gitberthe/BertheVarioTac/CompZoneAerienne/zones_gnuplot/000.png

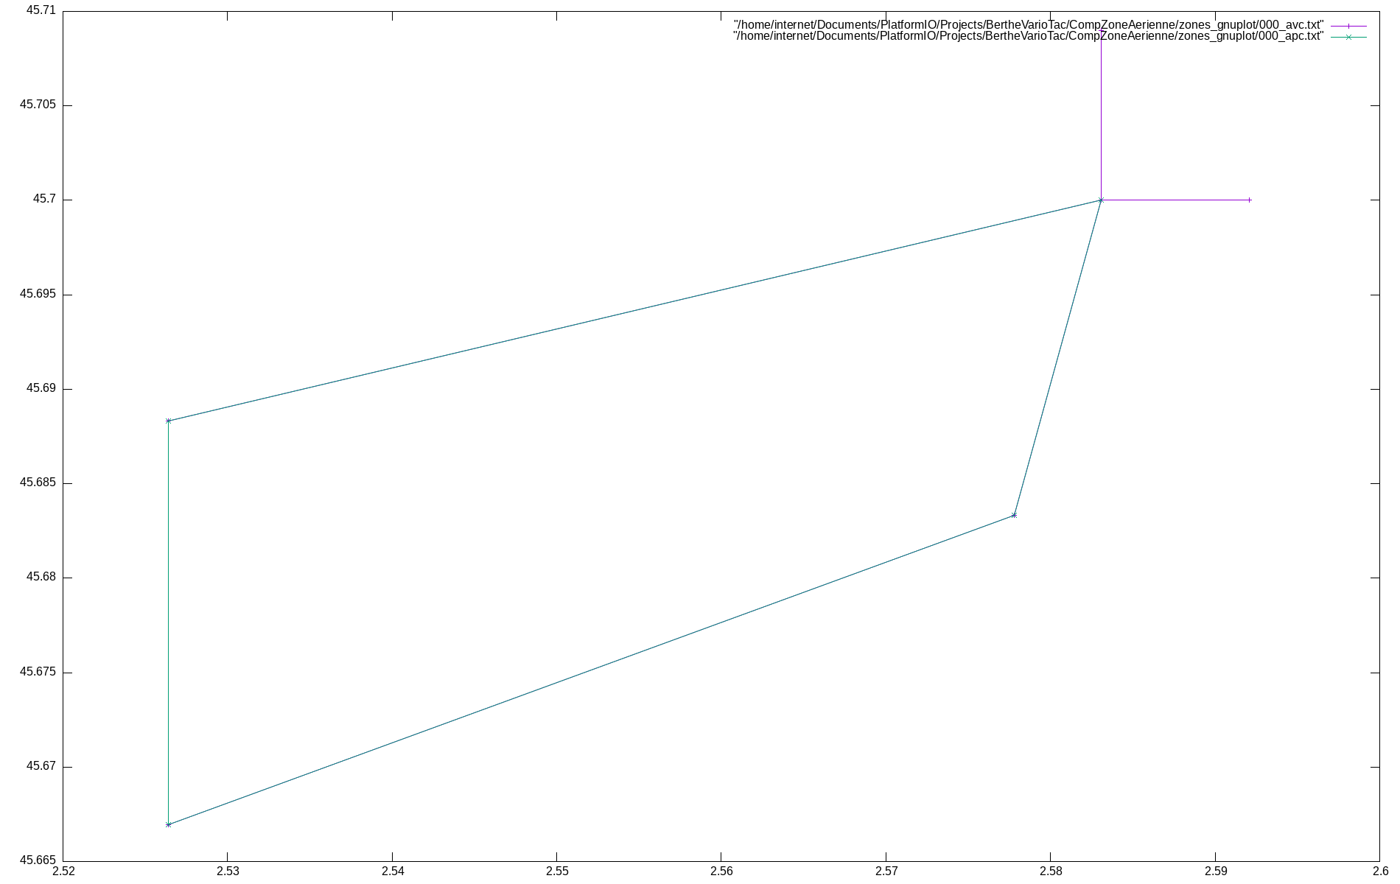
CompZoneAerienne/zones_gnuplot/000.png
