gitberthe/BertheVarioTac/CompZoneAerienne/zones_gnuplot/001.png

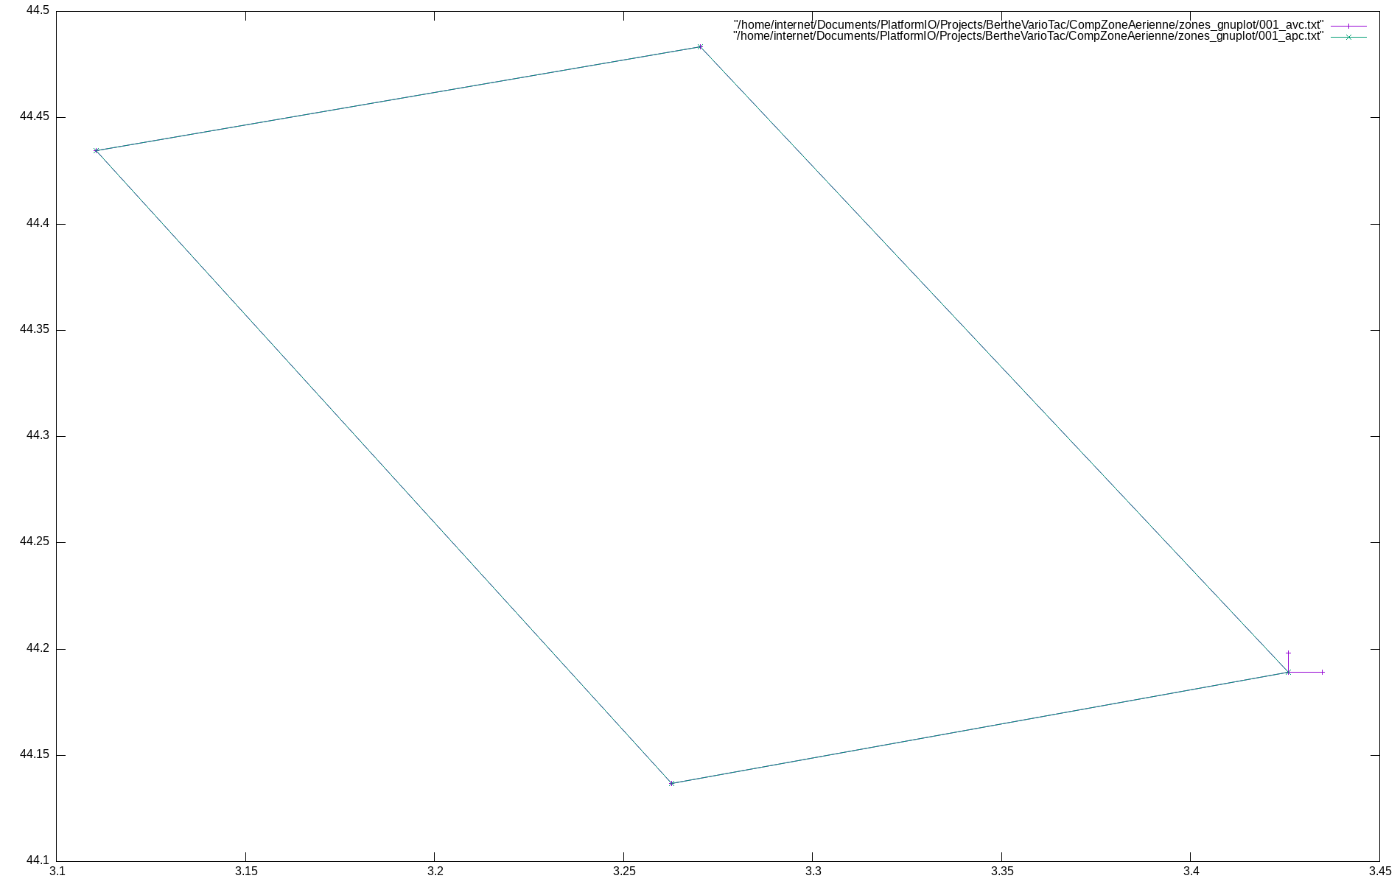
CompZoneAerienne/zones_gnuplot/001.png
