gitberthe/BertheVarioTac/CompZoneAerienne/zones_gnuplot/002.png

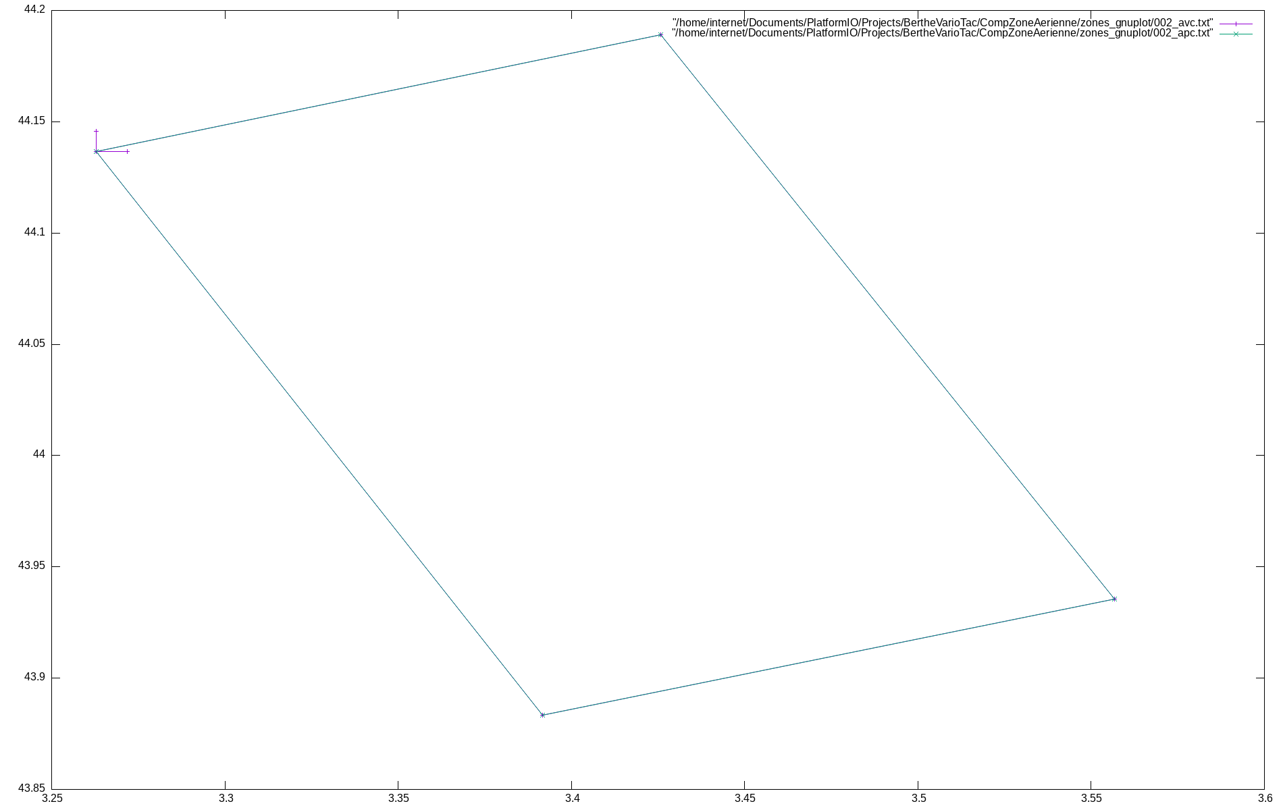
CompZoneAerienne/zones_gnuplot/002.png
