gitberthe/BertheVarioTac/CompZoneAerienne/zones_gnuplot/003.png

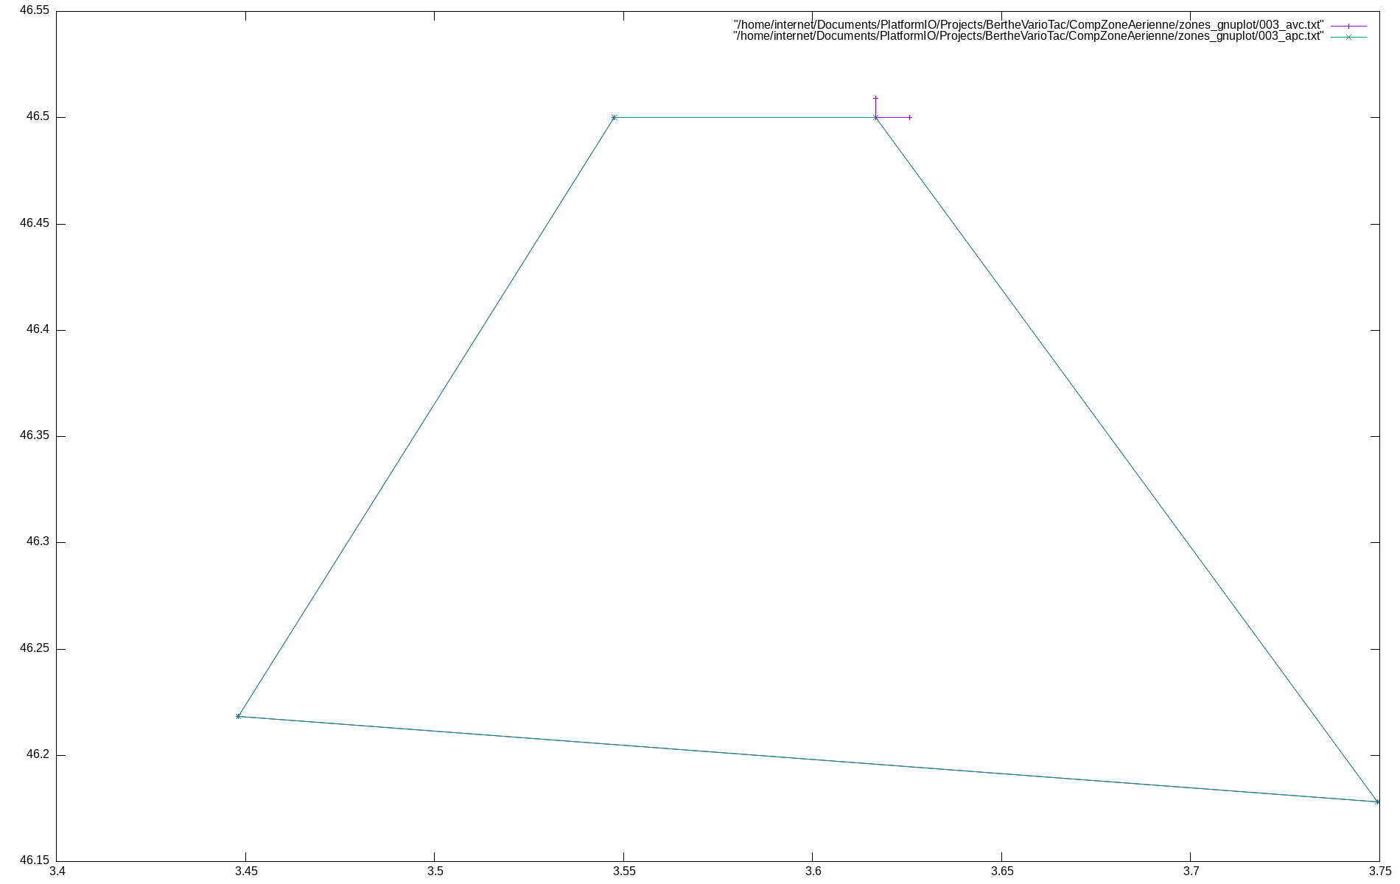
CompZoneAerienne/zones_gnuplot/003.png
