gitberthe/BertheVarioTac/CompZoneAerienne/zones_gnuplot/004.png

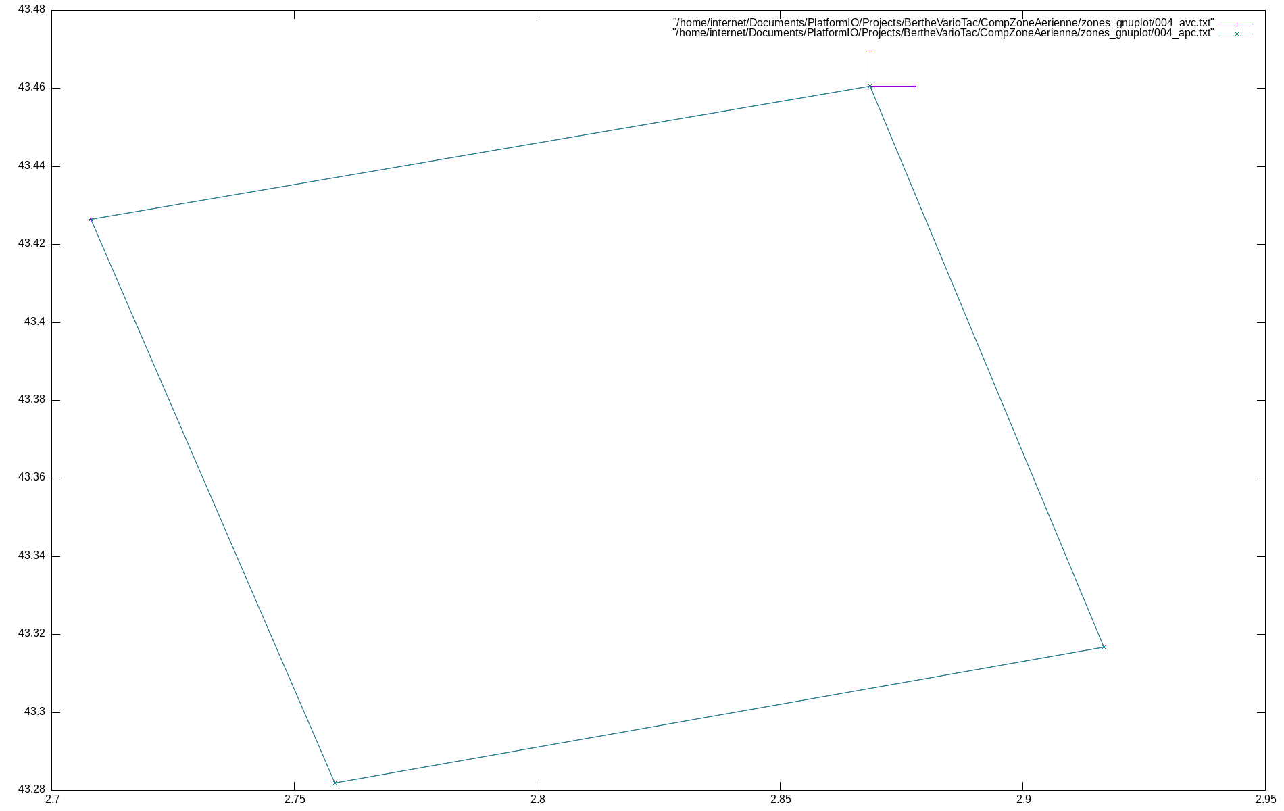
CompZoneAerienne/zones_gnuplot/004.png
