gitberthe/BertheVarioTac/CompZoneAerienne/zones_gnuplot/005.png

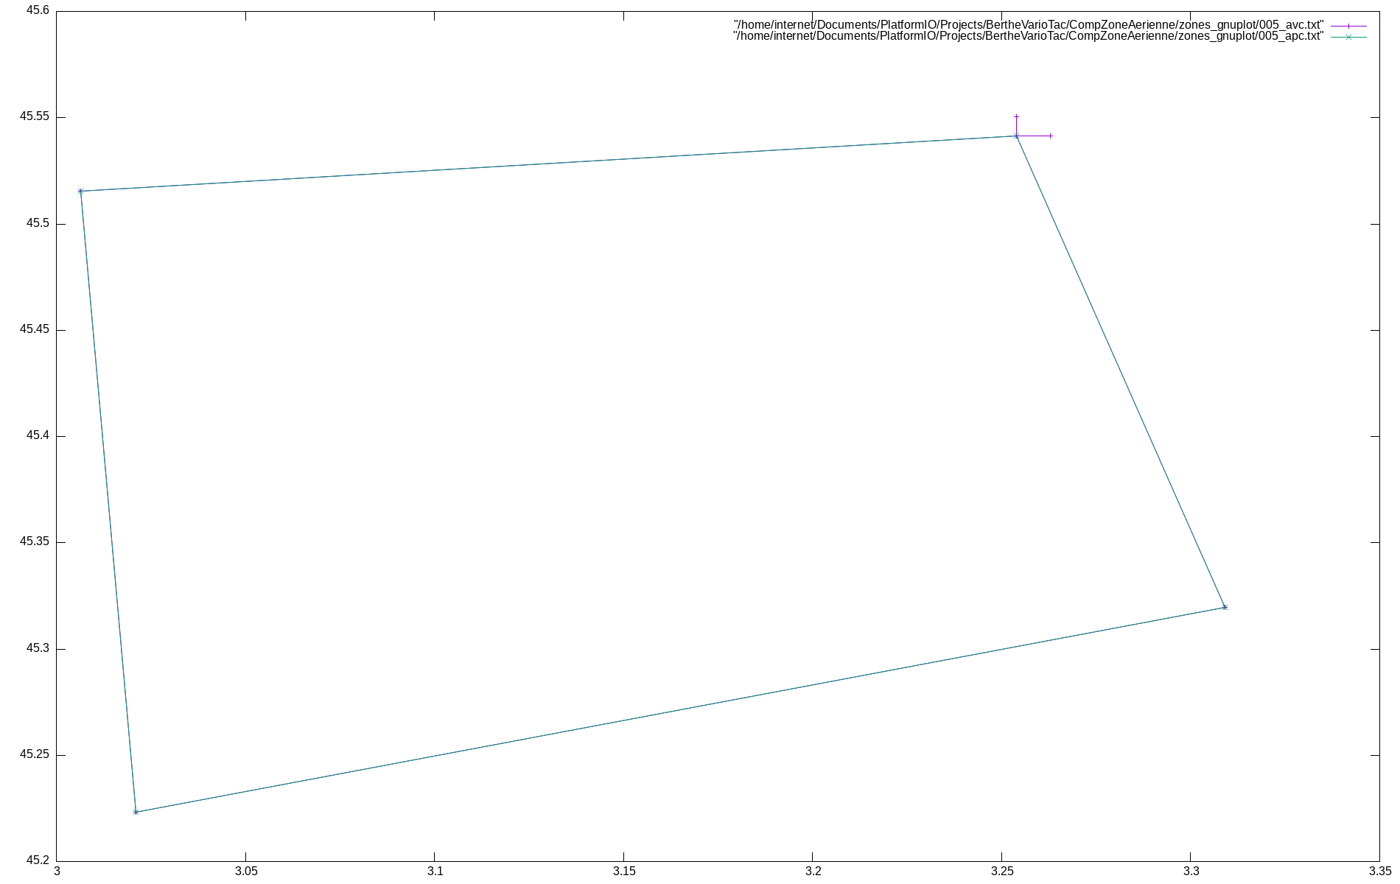
CompZoneAerienne/zones_gnuplot/005.png
