gitberthe/BertheVarioTac/CompZoneAerienne/zones_gnuplot/006.png

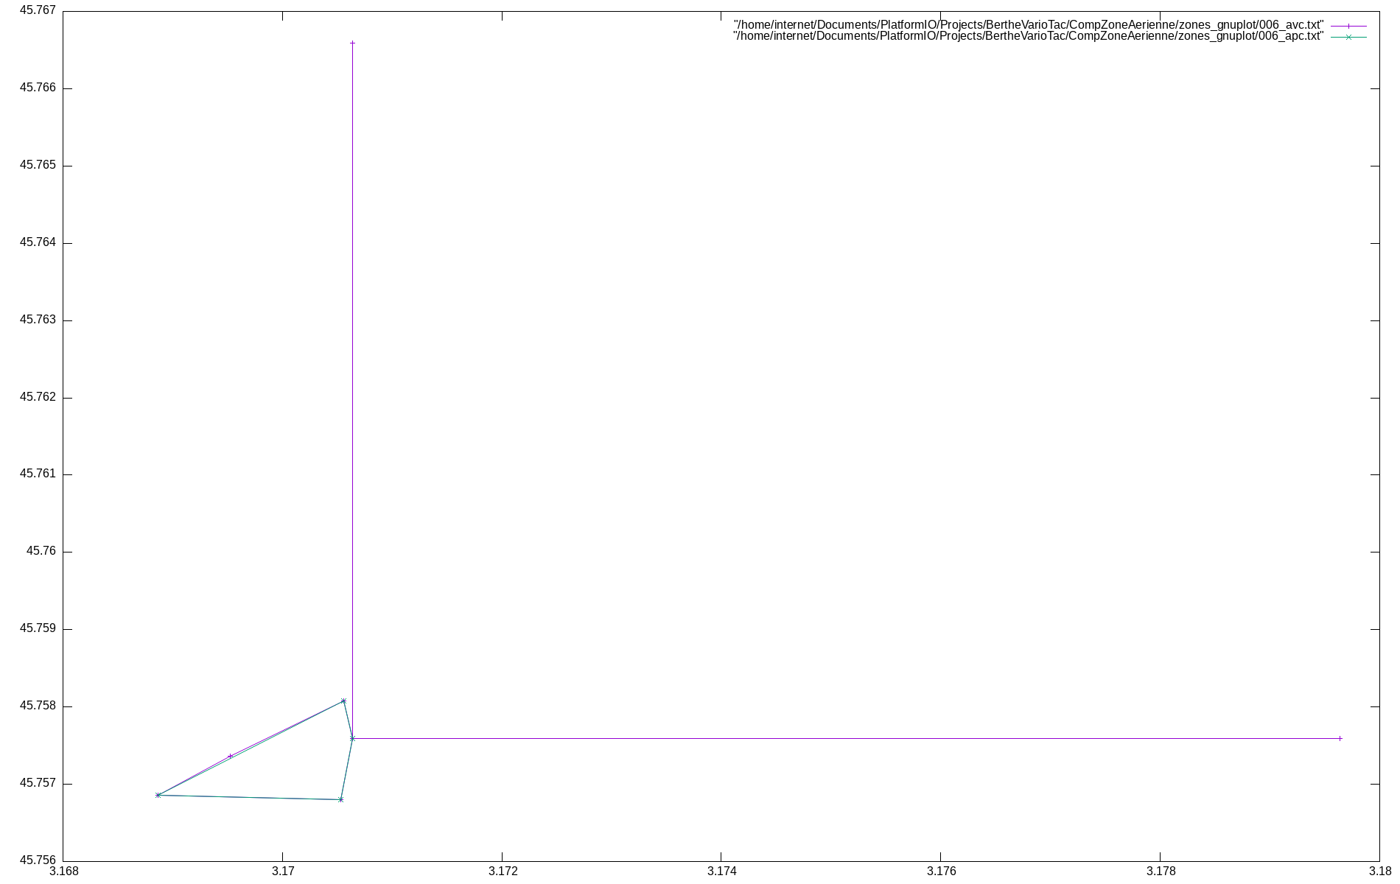
CompZoneAerienne/zones_gnuplot/006.png
