gitberthe/BertheVarioTac/CompZoneAerienne/zones_gnuplot/008.png

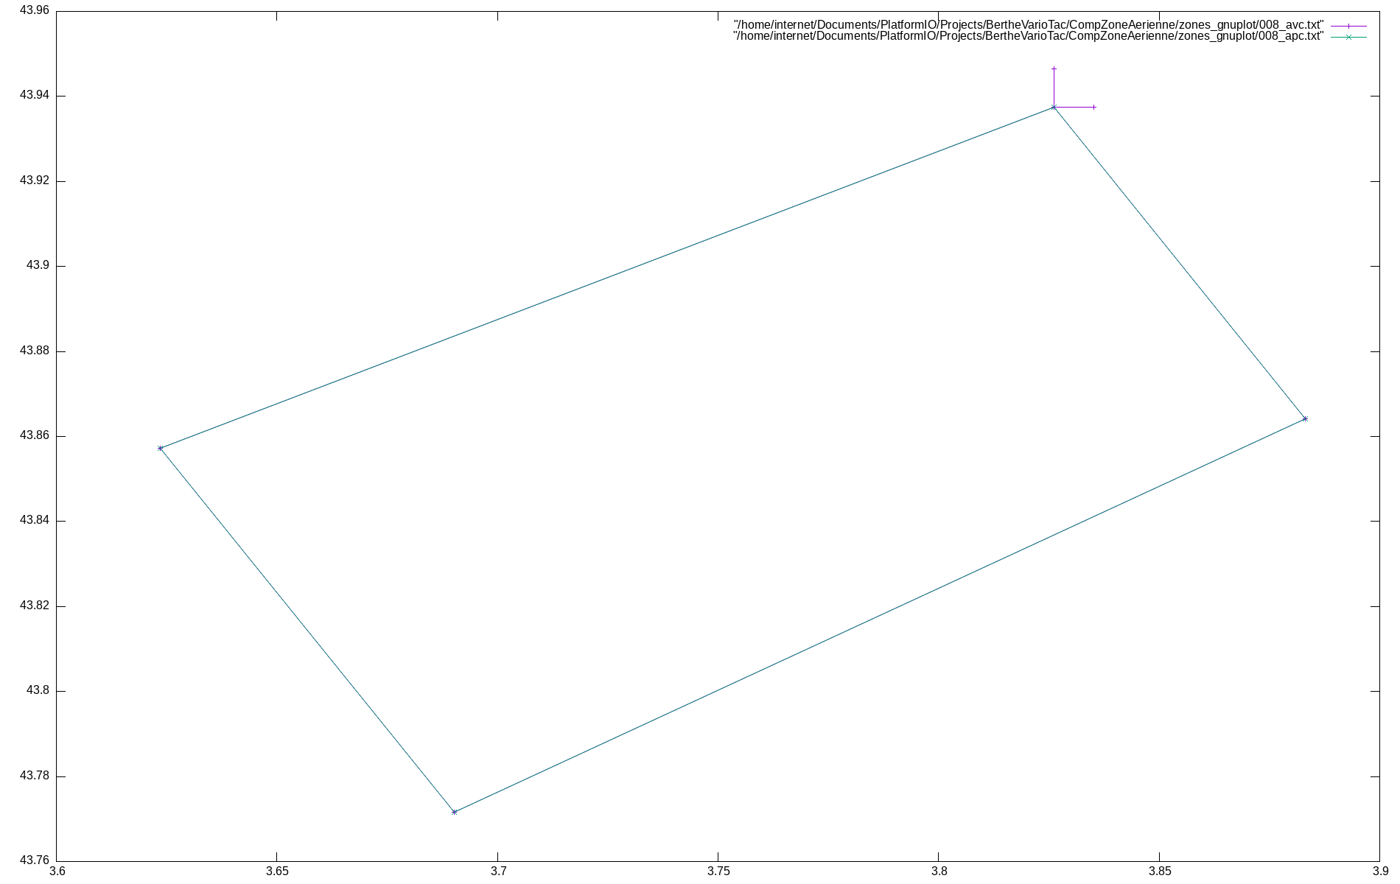
CompZoneAerienne/zones_gnuplot/008.png
