gitberthe/BertheVarioTac/CompZoneAerienne/zones_gnuplot/009.png

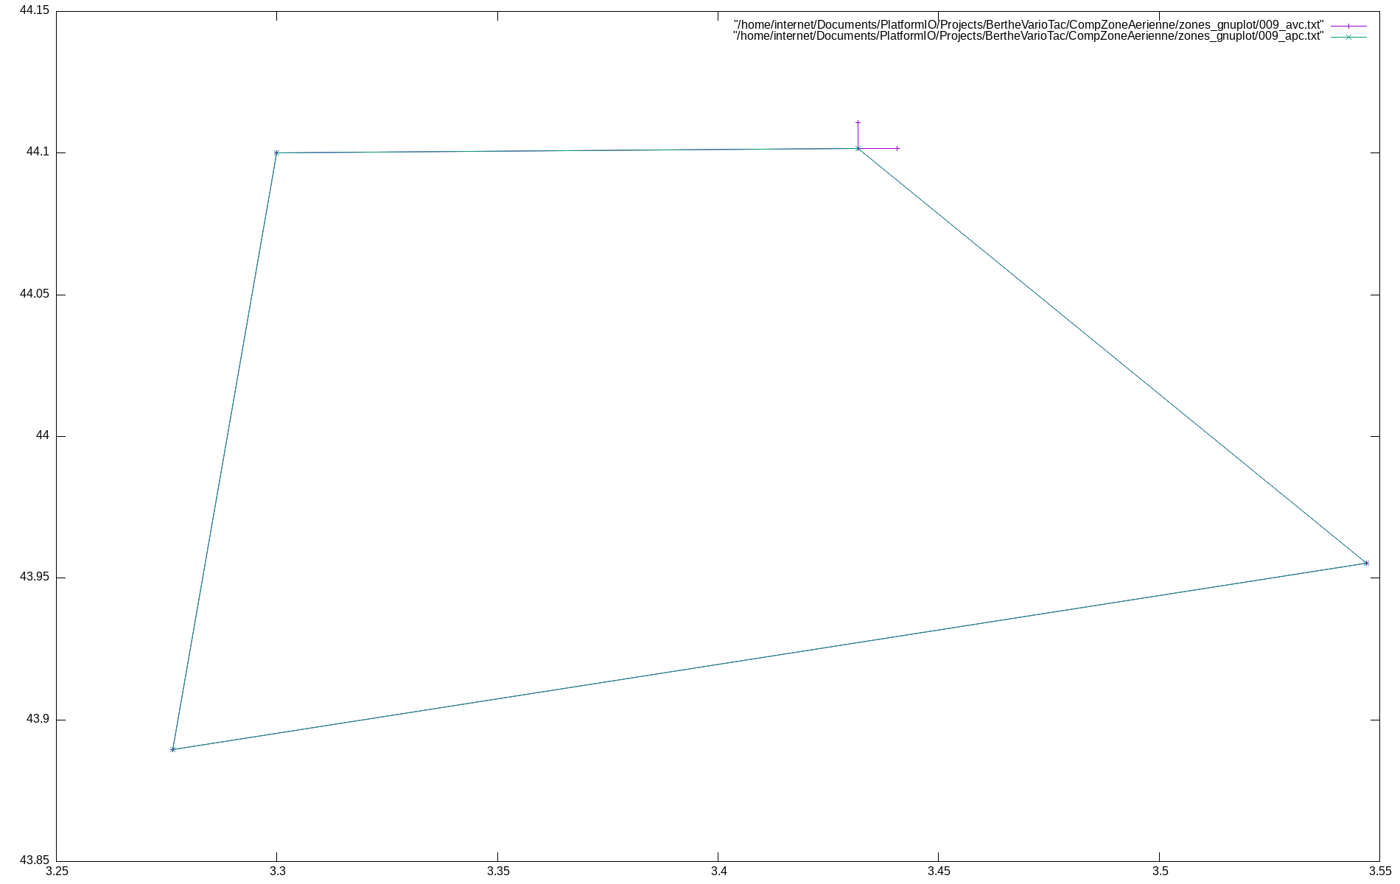
CompZoneAerienne/zones_gnuplot/009.png
