gitberthe/BertheVarioTac/CompZoneAerienne/zones_gnuplot/010.png

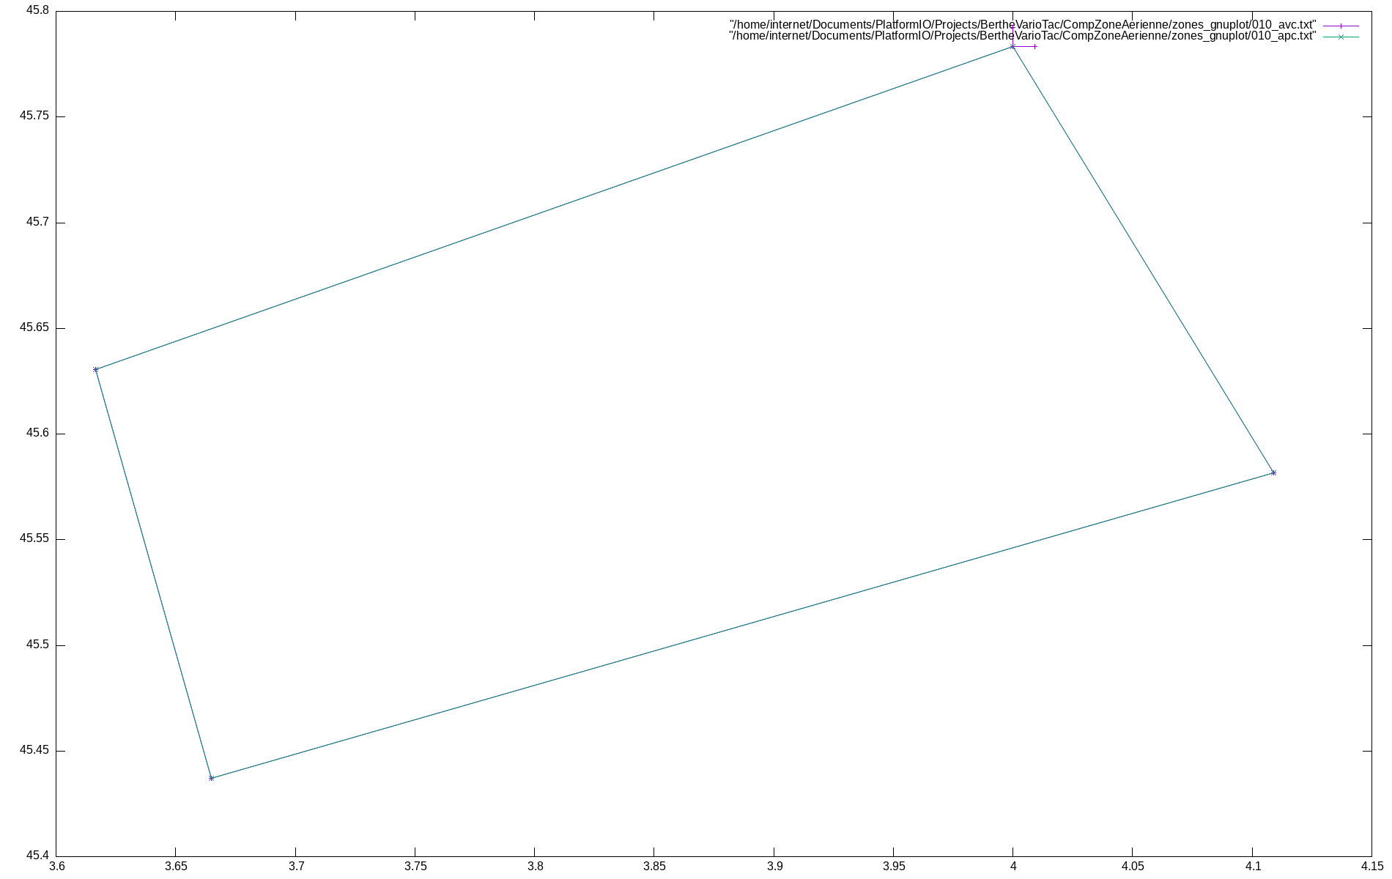
CompZoneAerienne/zones_gnuplot/010.png
