gitberthe/BertheVarioTac/CompZoneAerienne/zones_gnuplot/011.png

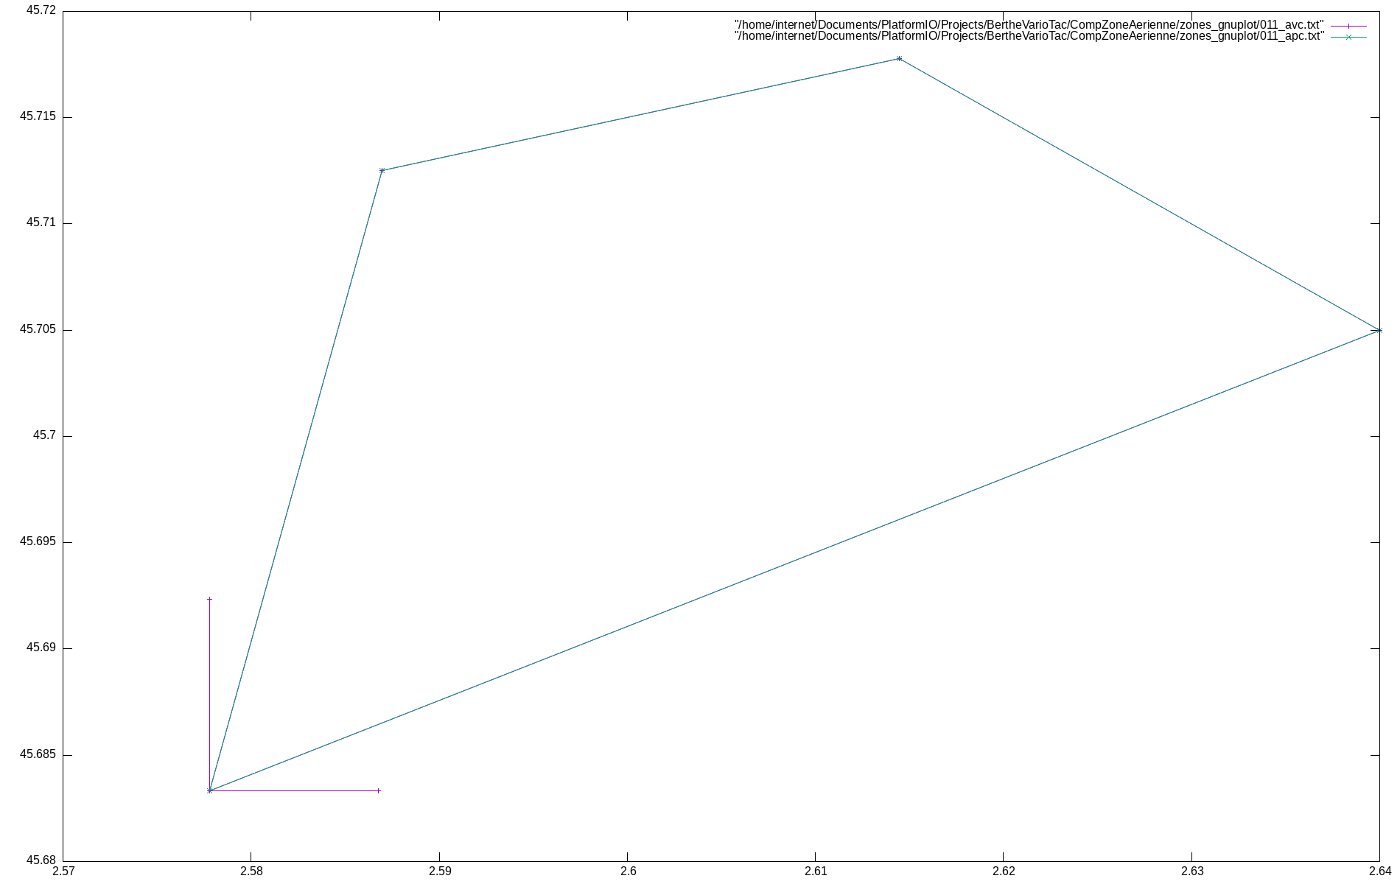
CompZoneAerienne/zones_gnuplot/011.png
