gitberthe/BertheVarioTac/CompZoneAerienne/zones_gnuplot/012.png

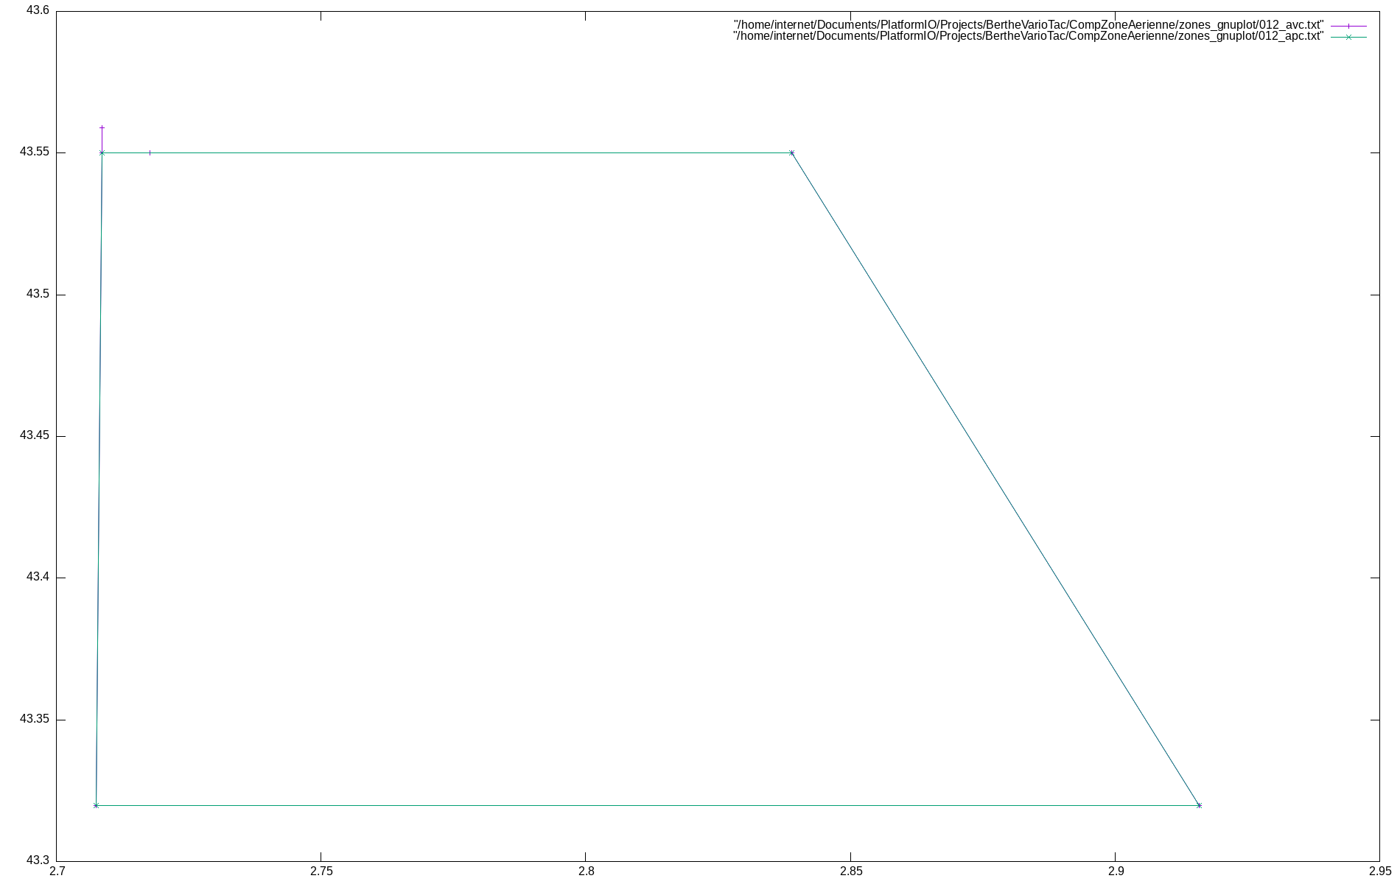
CompZoneAerienne/zones_gnuplot/012.png
