gitberthe/BertheVarioTac/CompZoneAerienne/zones_gnuplot/014.png

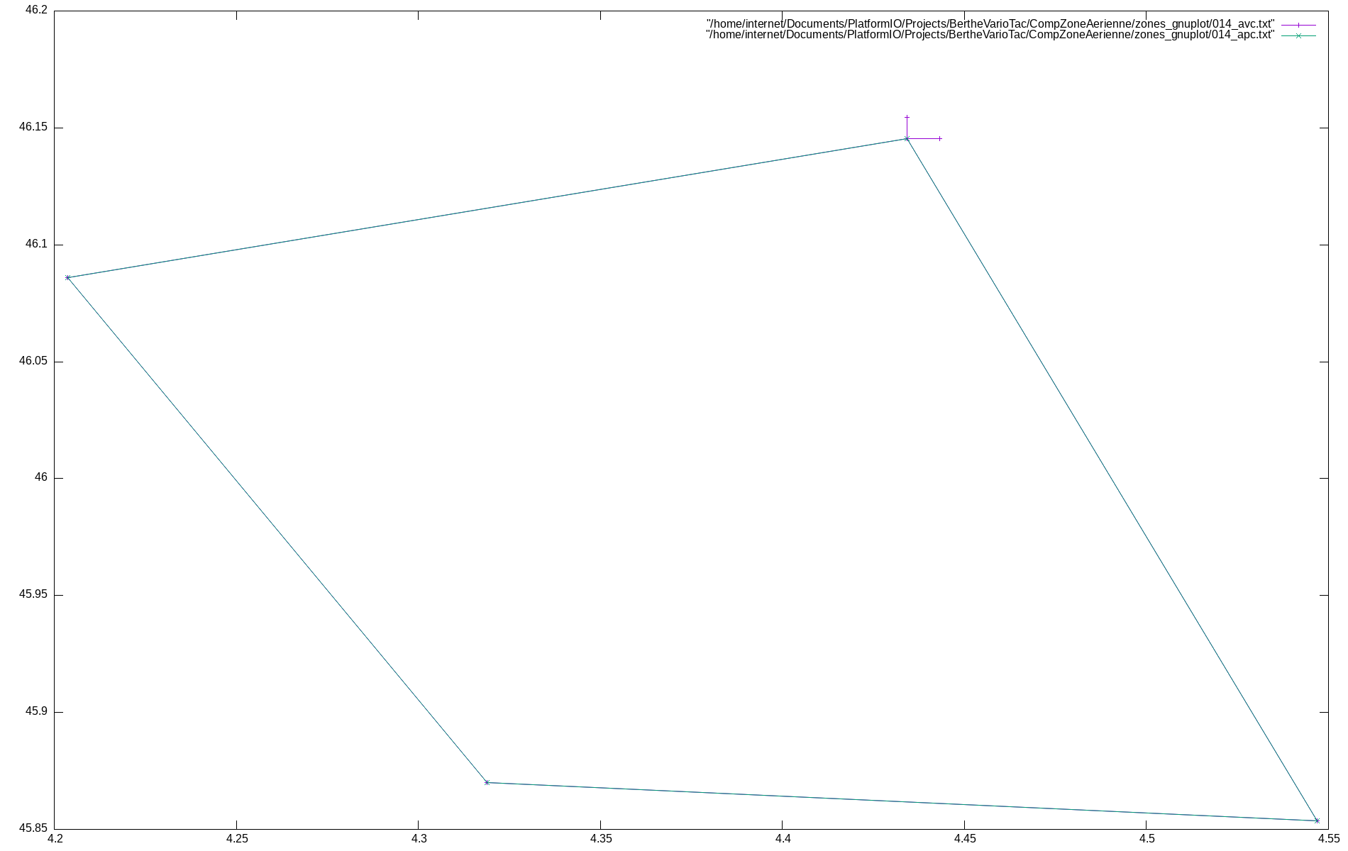
CompZoneAerienne/zones_gnuplot/014.png
