gitberthe/BertheVarioTac/CompZoneAerienne/zones_gnuplot/015.png

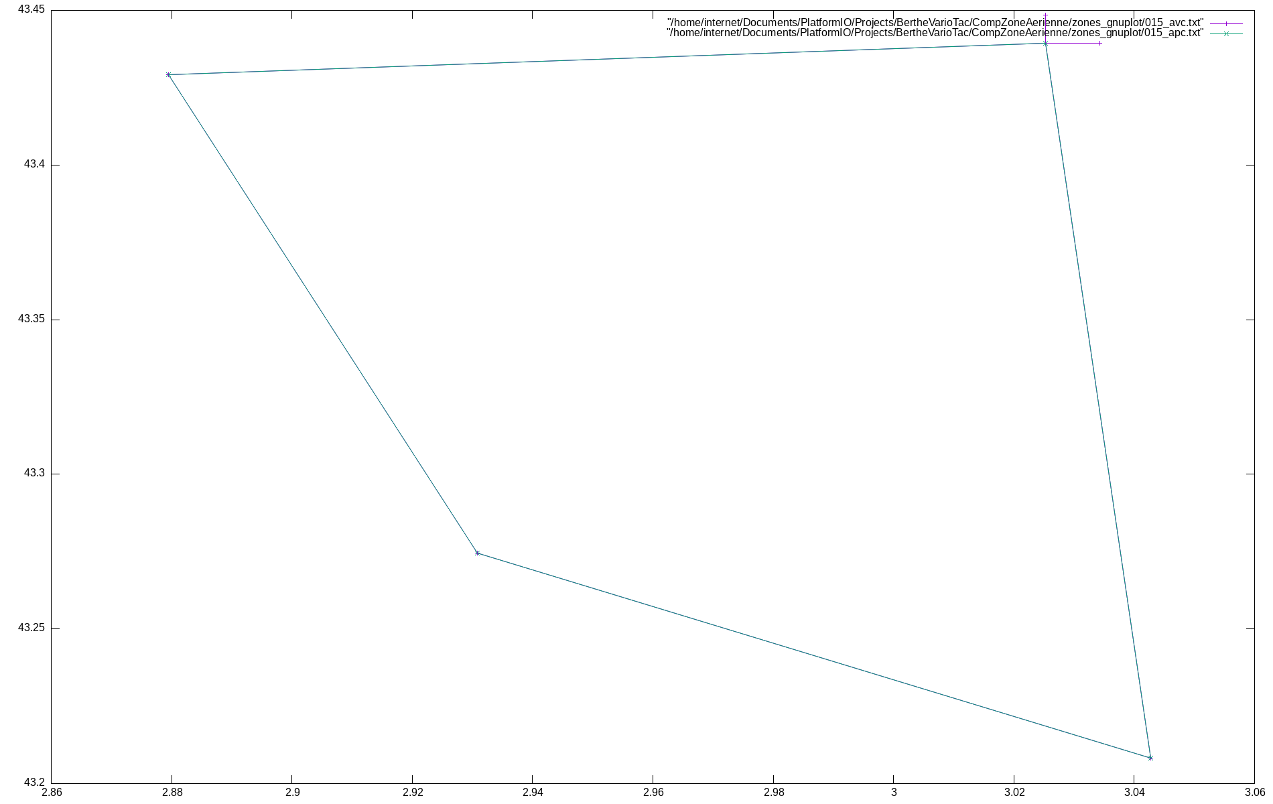
CompZoneAerienne/zones_gnuplot/015.png
