gitberthe/BertheVarioTac/CompZoneAerienne/zones_gnuplot/016.png

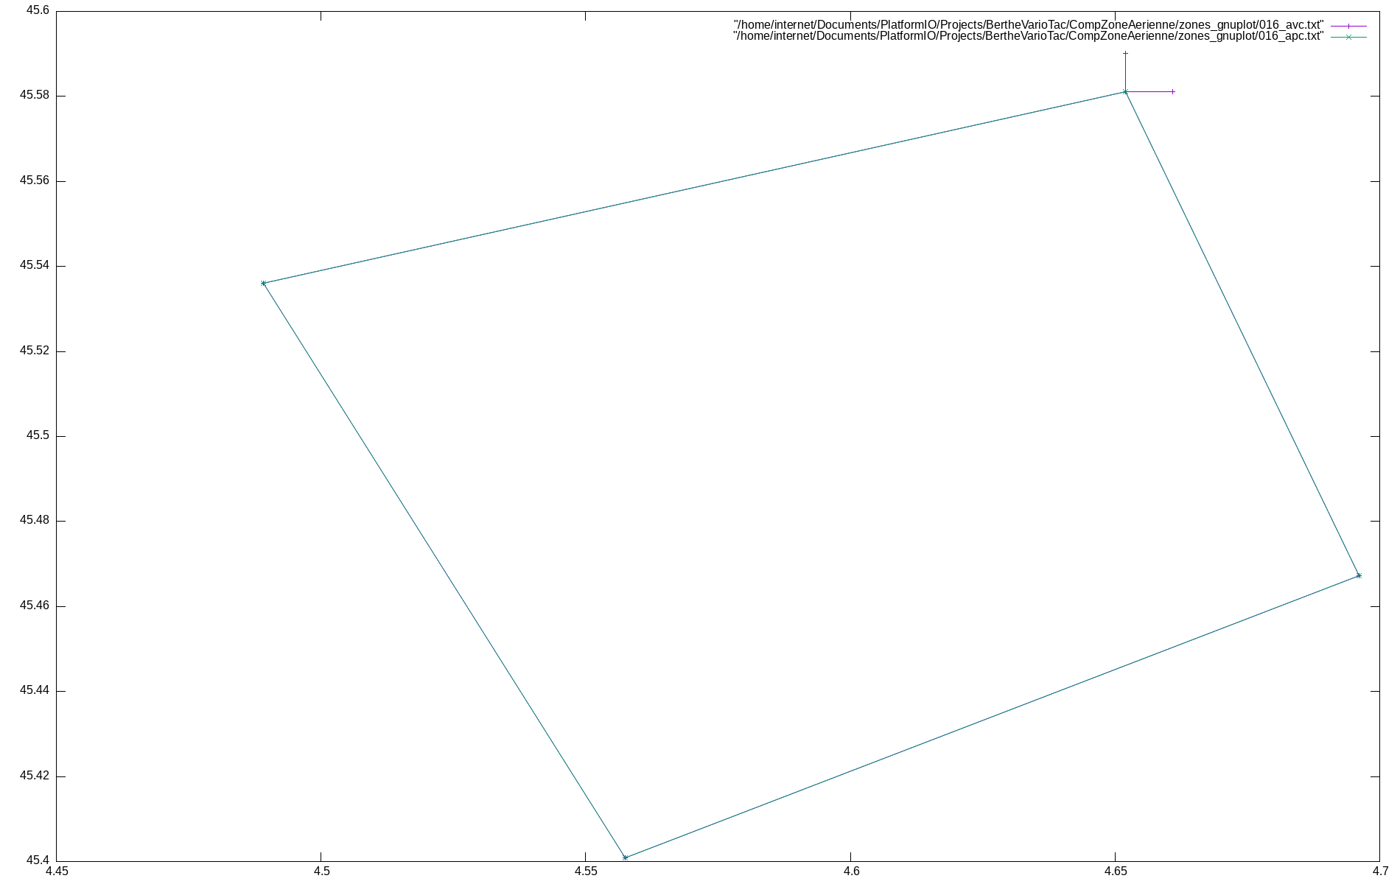
CompZoneAerienne/zones_gnuplot/016.png
