gitberthe/BertheVarioTac/CompZoneAerienne/zones_gnuplot/017.png

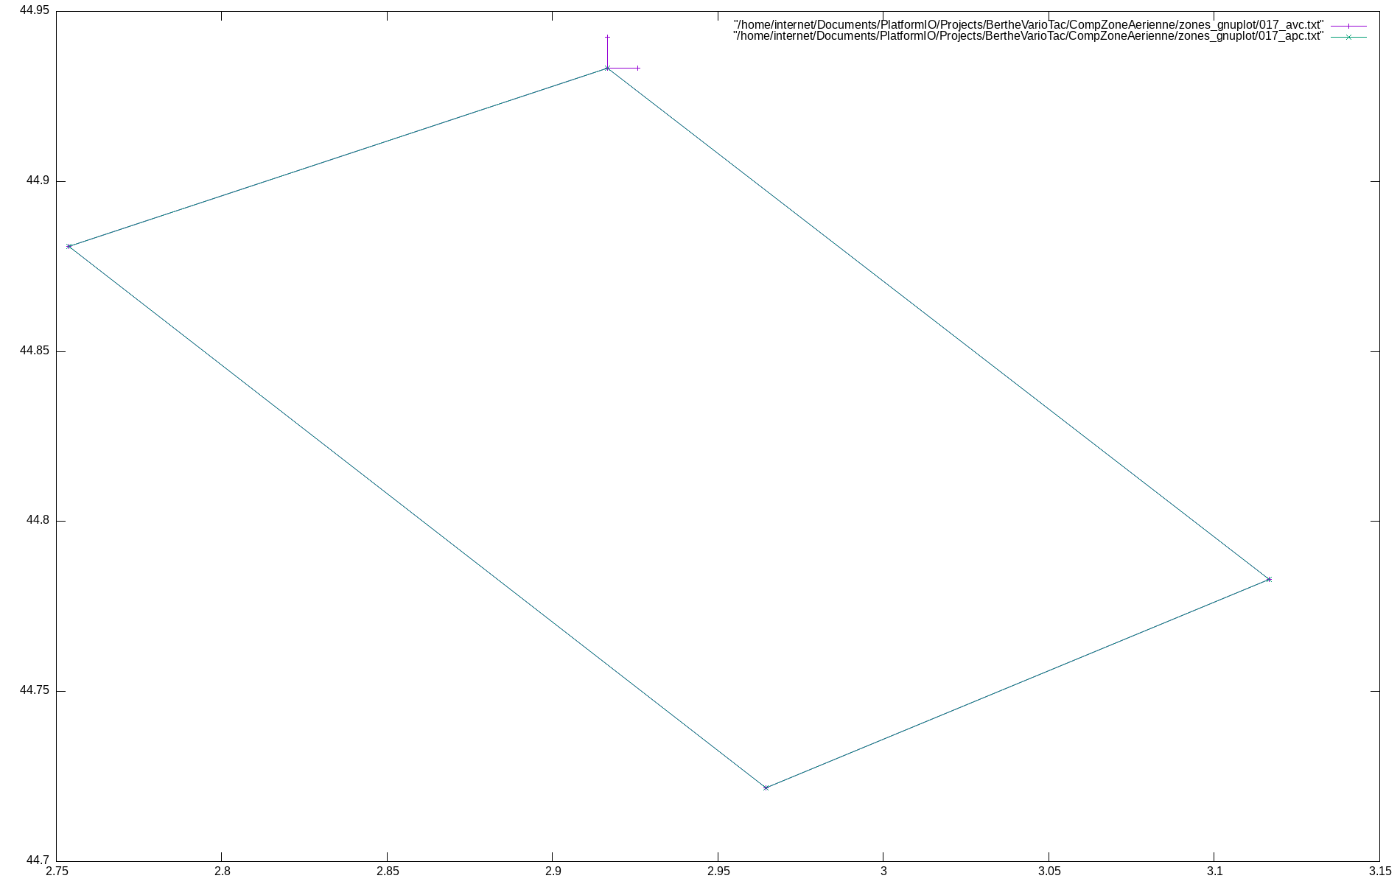
CompZoneAerienne/zones_gnuplot/017.png
