gitberthe/BertheVarioTac/CompZoneAerienne/zones_gnuplot/018.png

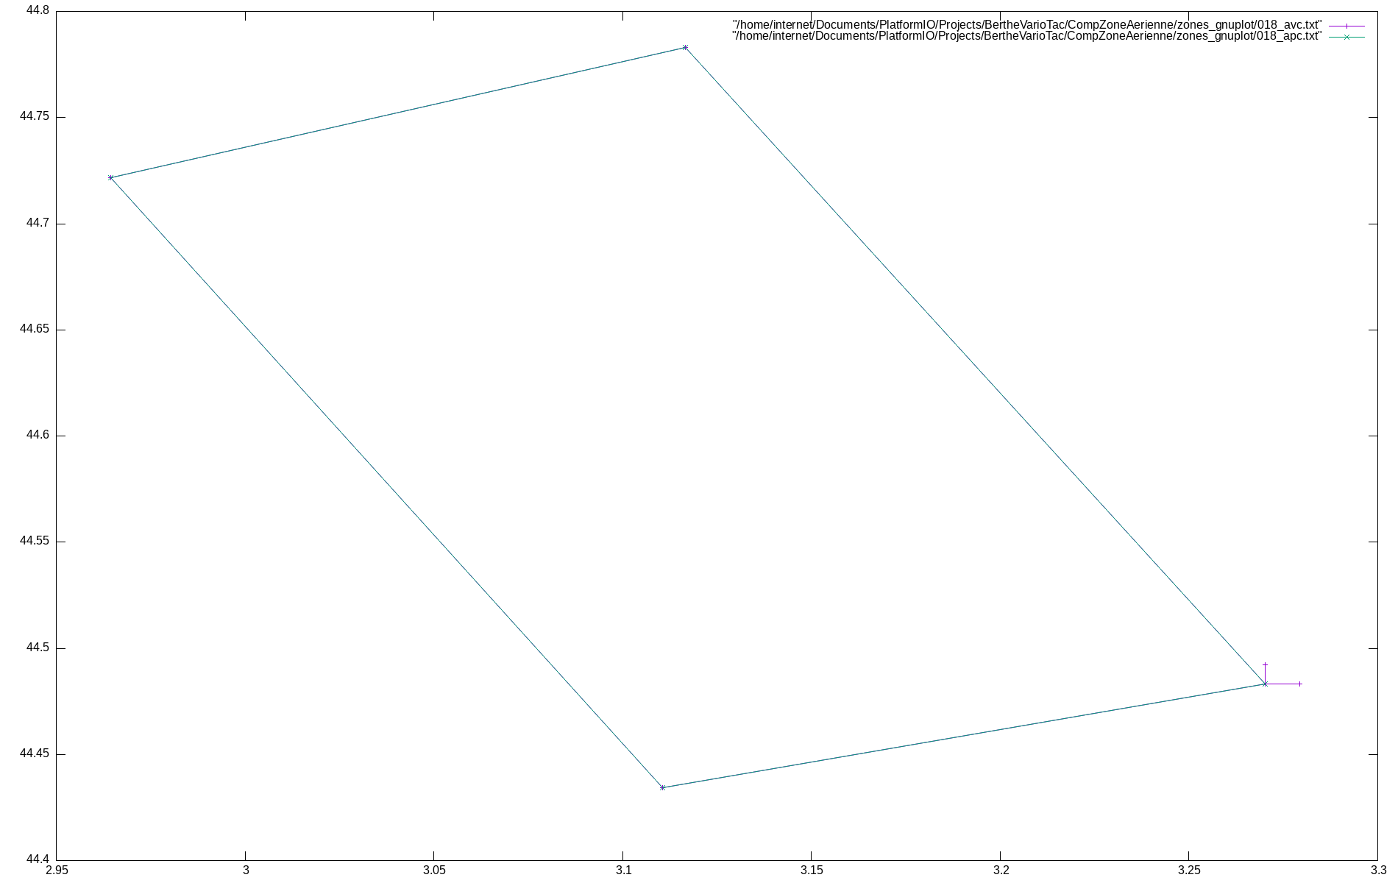
CompZoneAerienne/zones_gnuplot/018.png
