gitberthe/BertheVarioTac/CompZoneAerienne/zones_gnuplot/019.png

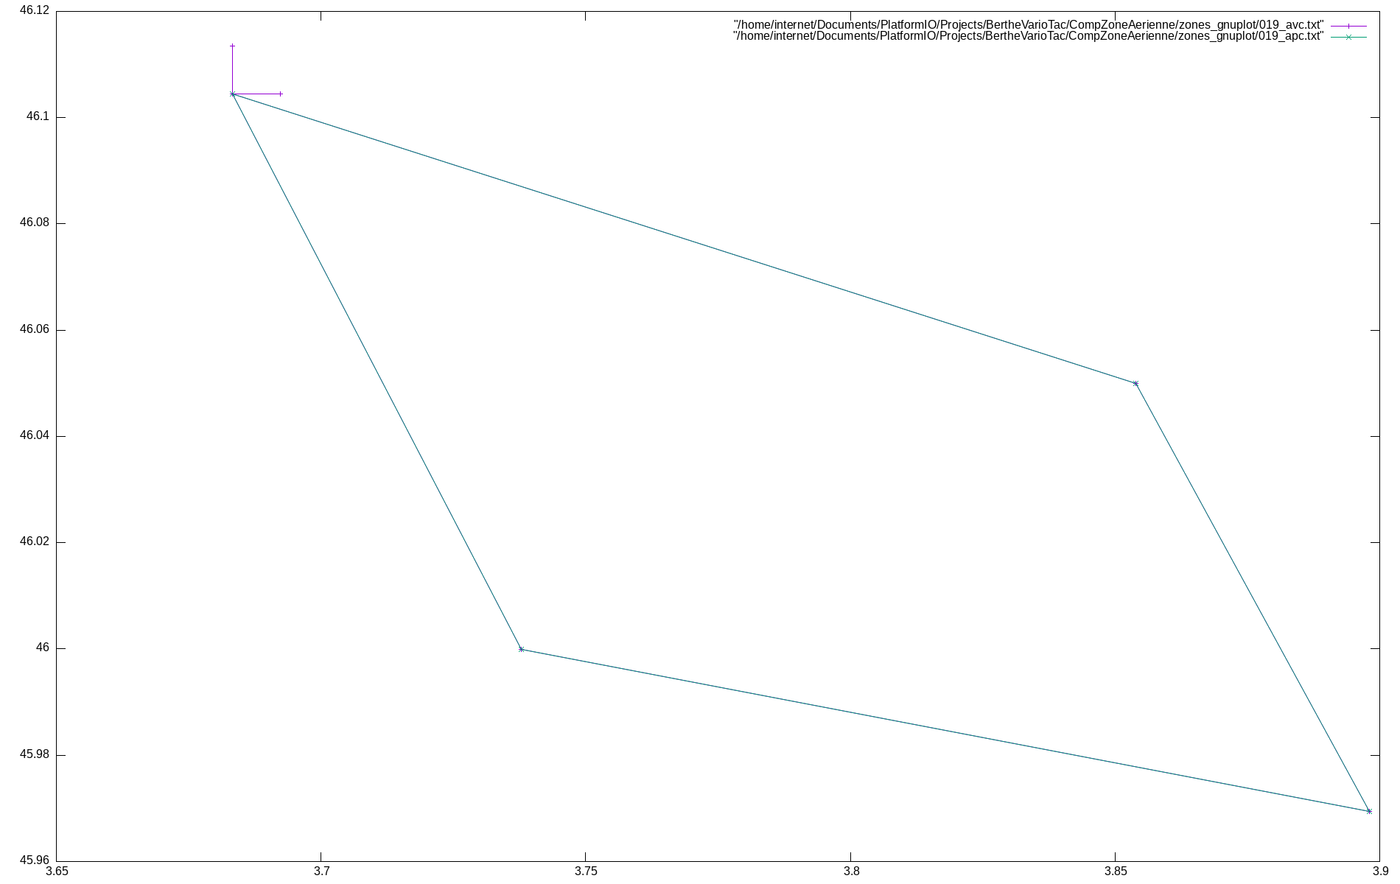
CompZoneAerienne/zones_gnuplot/019.png
