gitberthe/BertheVarioTac/CompZoneAerienne/zones_gnuplot/020.png

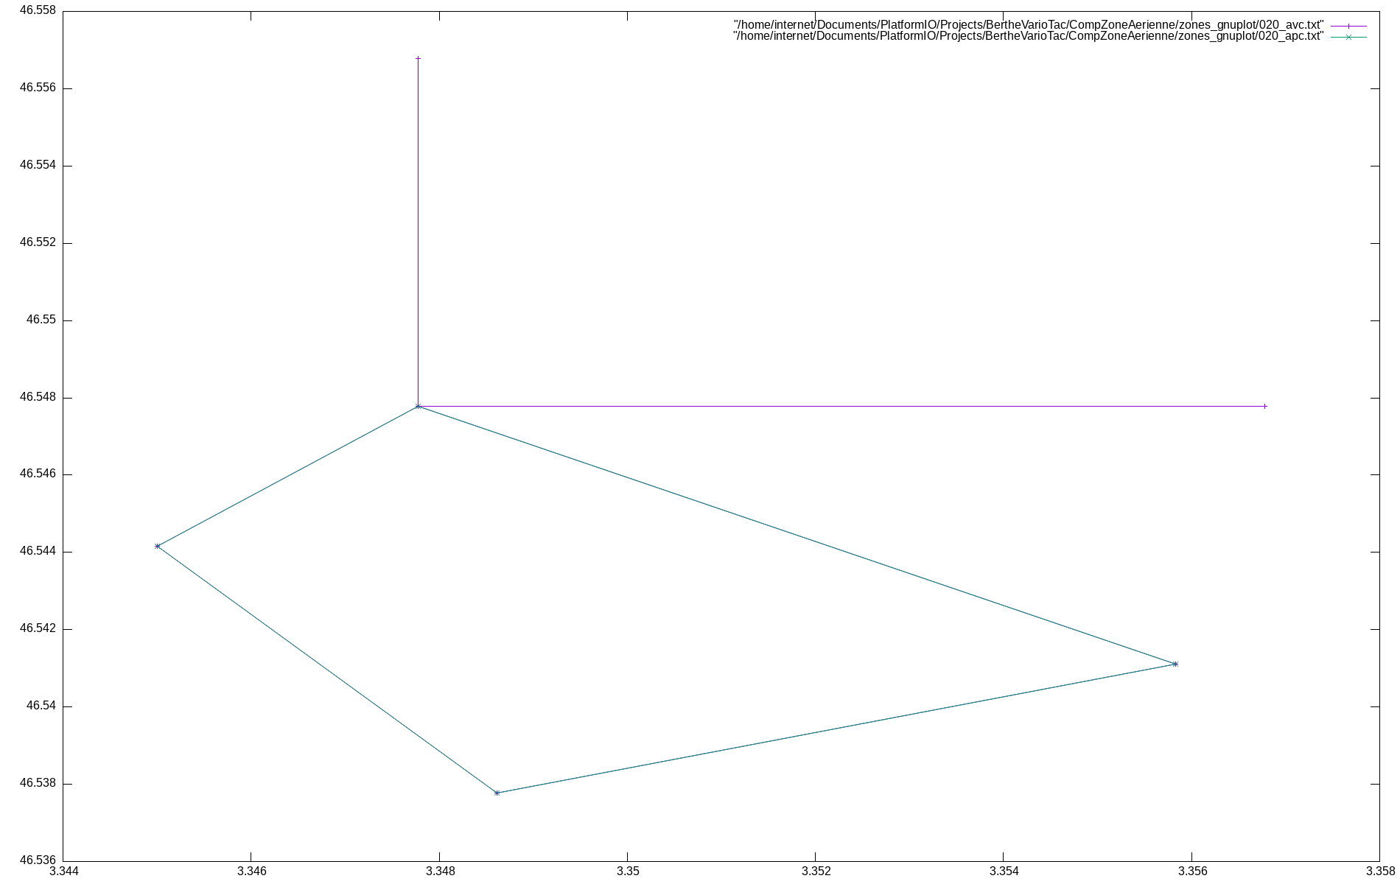
CompZoneAerienne/zones_gnuplot/020.png
