gitberthe/BertheVarioTac/CompZoneAerienne/zones_gnuplot/022.png

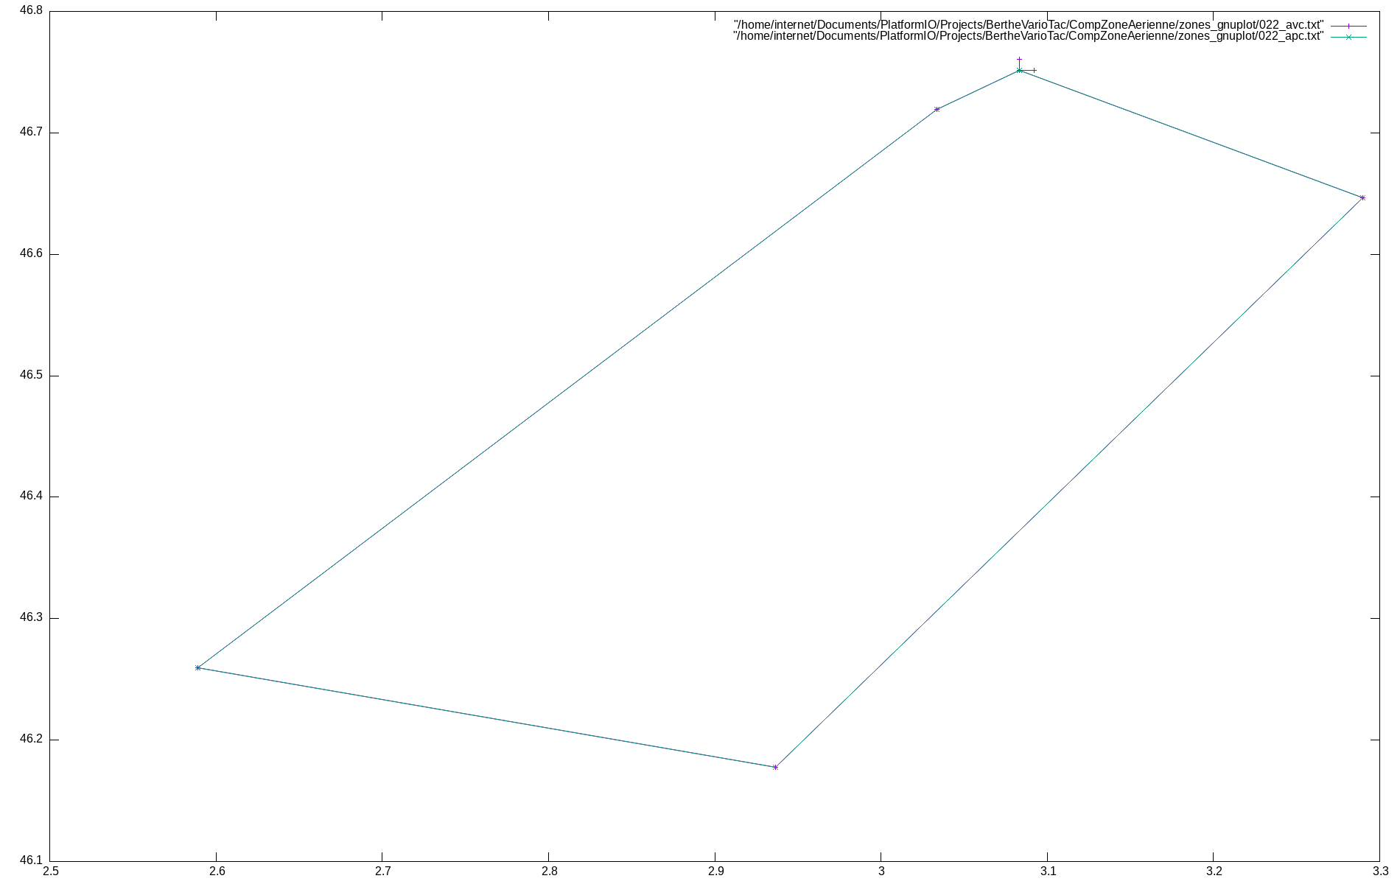
CompZoneAerienne/zones_gnuplot/022.png
