gitberthe/BertheVarioTac/CompZoneAerienne/zones_gnuplot/023.png

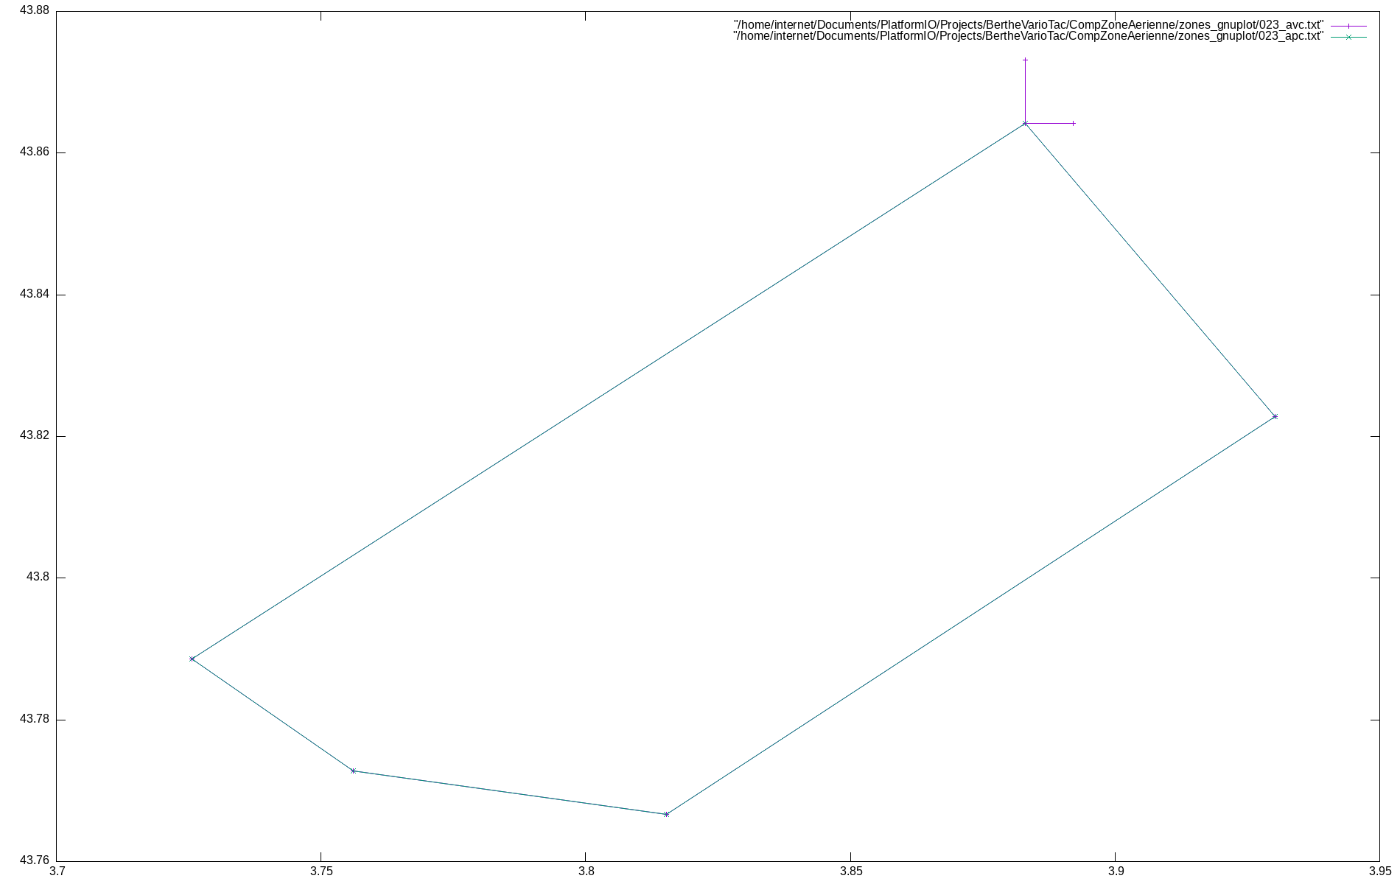
CompZoneAerienne/zones_gnuplot/023.png
