gitberthe/BertheVarioTac/CompZoneAerienne/zones_gnuplot/024.png

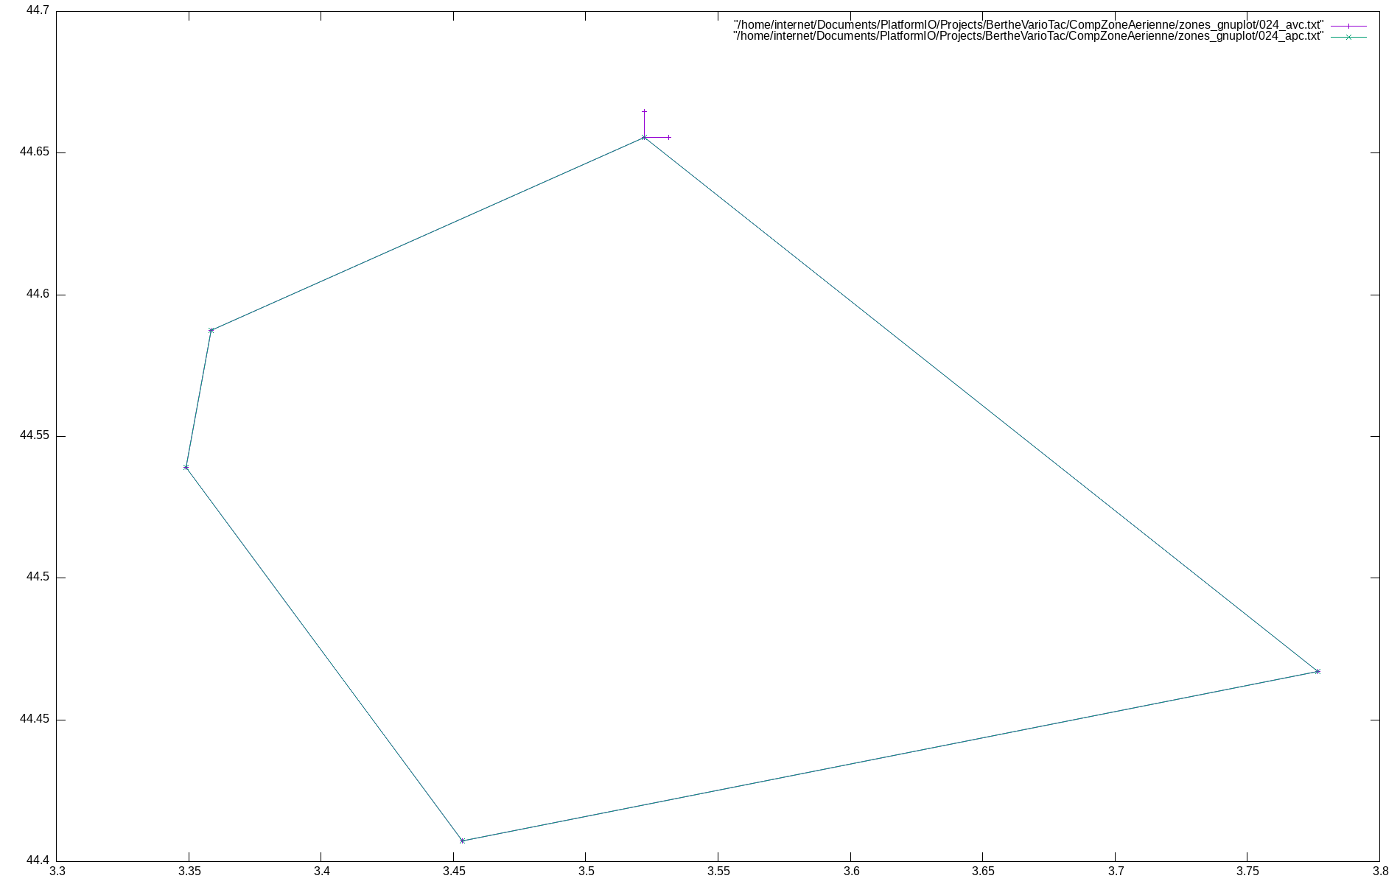
CompZoneAerienne/zones_gnuplot/024.png
