gitberthe/BertheVarioTac/CompZoneAerienne/zones_gnuplot/025.png

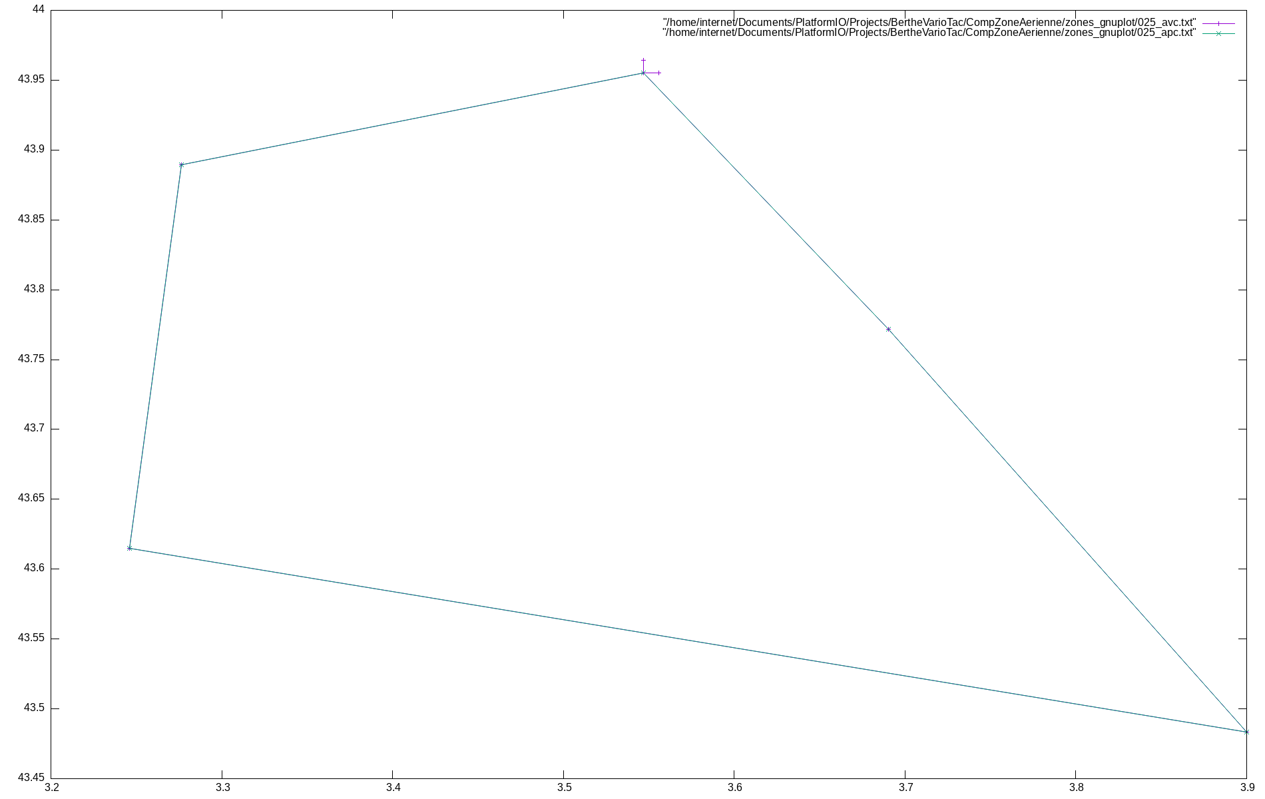
CompZoneAerienne/zones_gnuplot/025.png
