gitberthe/BertheVarioTac/CompZoneAerienne/zones_gnuplot/026.png

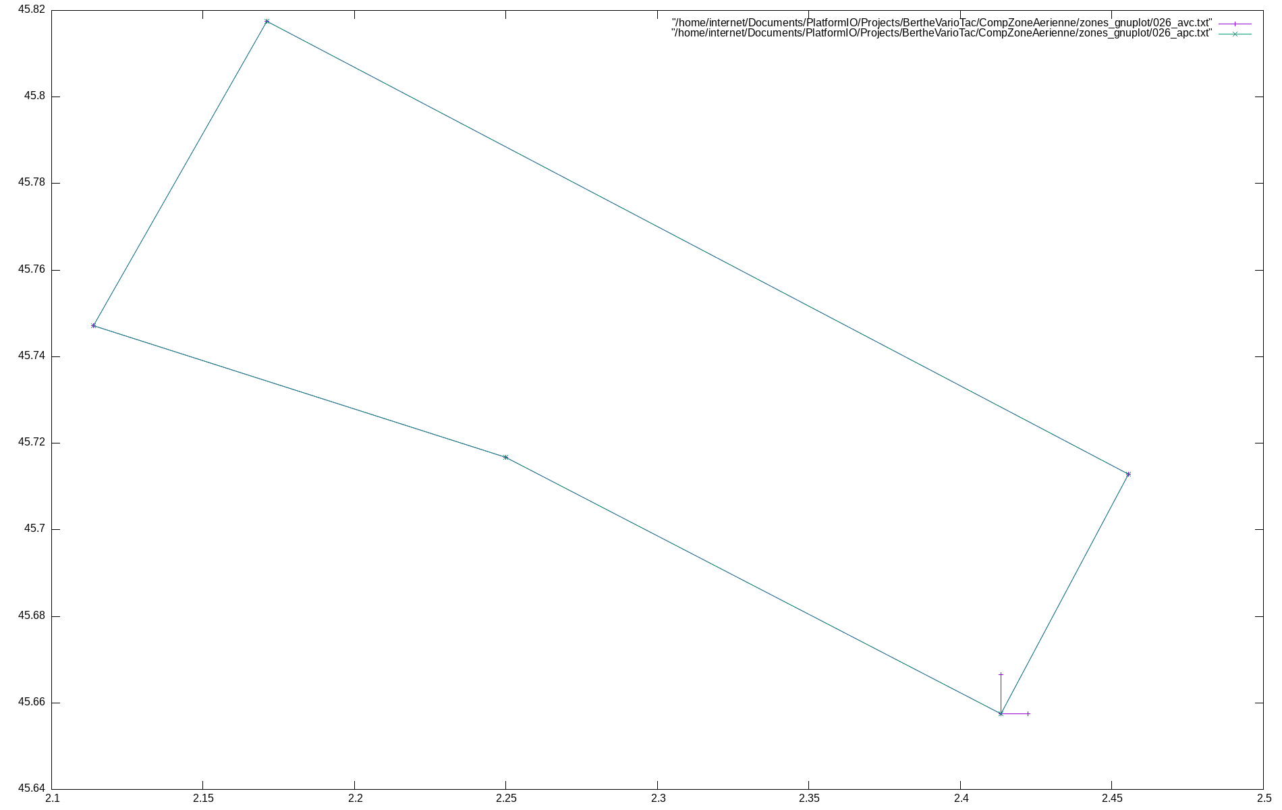
CompZoneAerienne/zones_gnuplot/026.png
