gitberthe/BertheVarioTac/CompZoneAerienne/zones_gnuplot/027.png

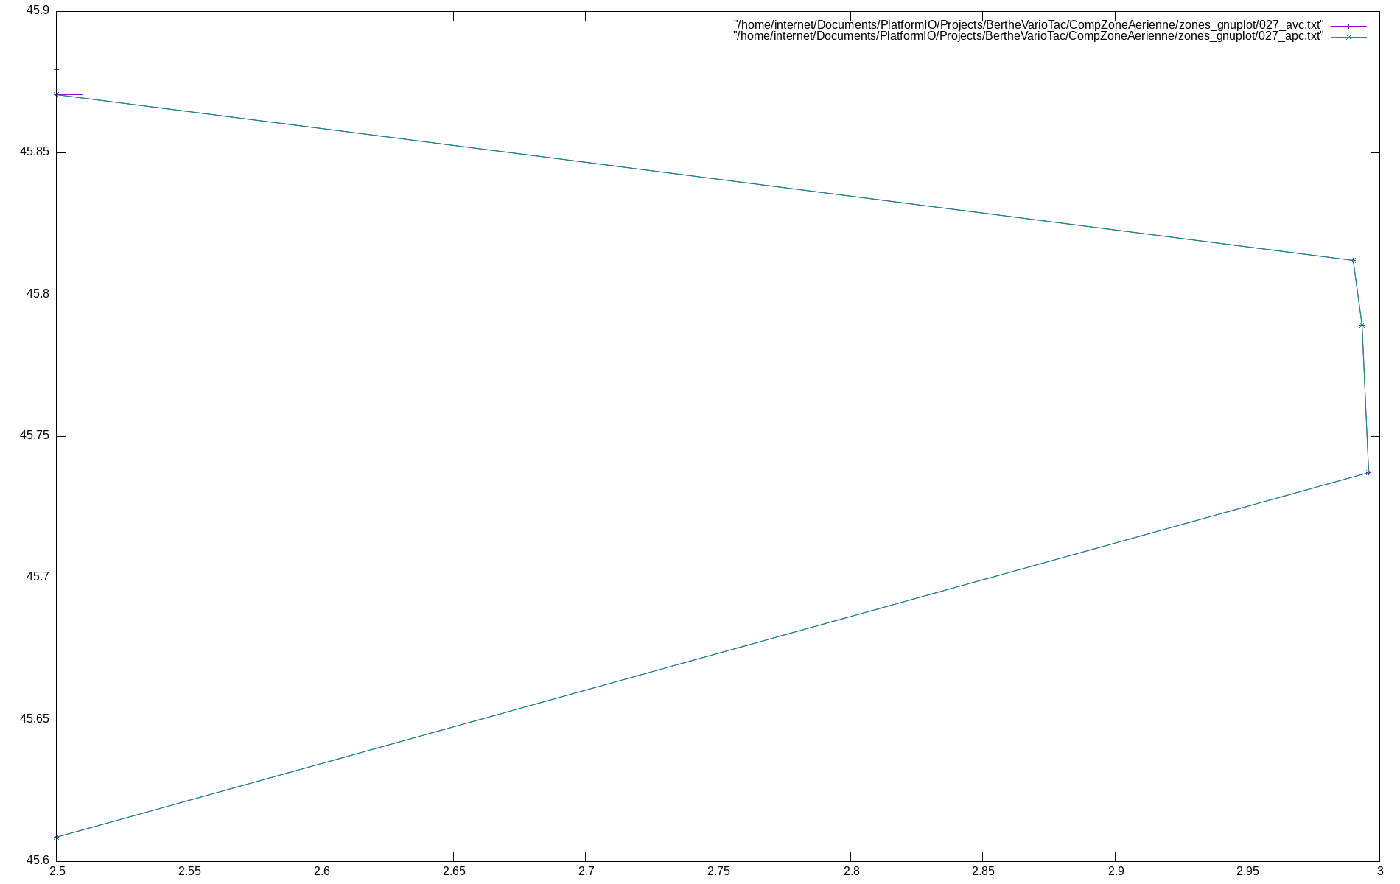
CompZoneAerienne/zones_gnuplot/027.png
