gitberthe/BertheVarioTac/CompZoneAerienne/zones_gnuplot/030.png

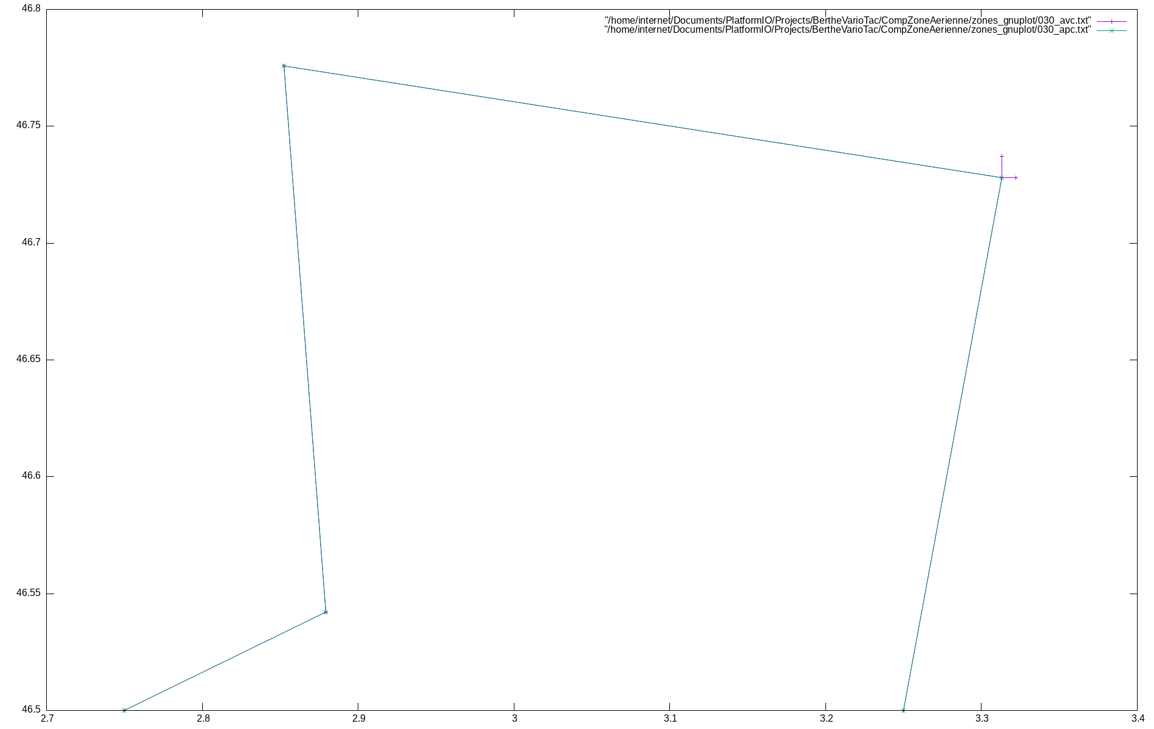
CompZoneAerienne/zones_gnuplot/030.png
