gitberthe/BertheVarioTac/CompZoneAerienne/zones_gnuplot/032.png

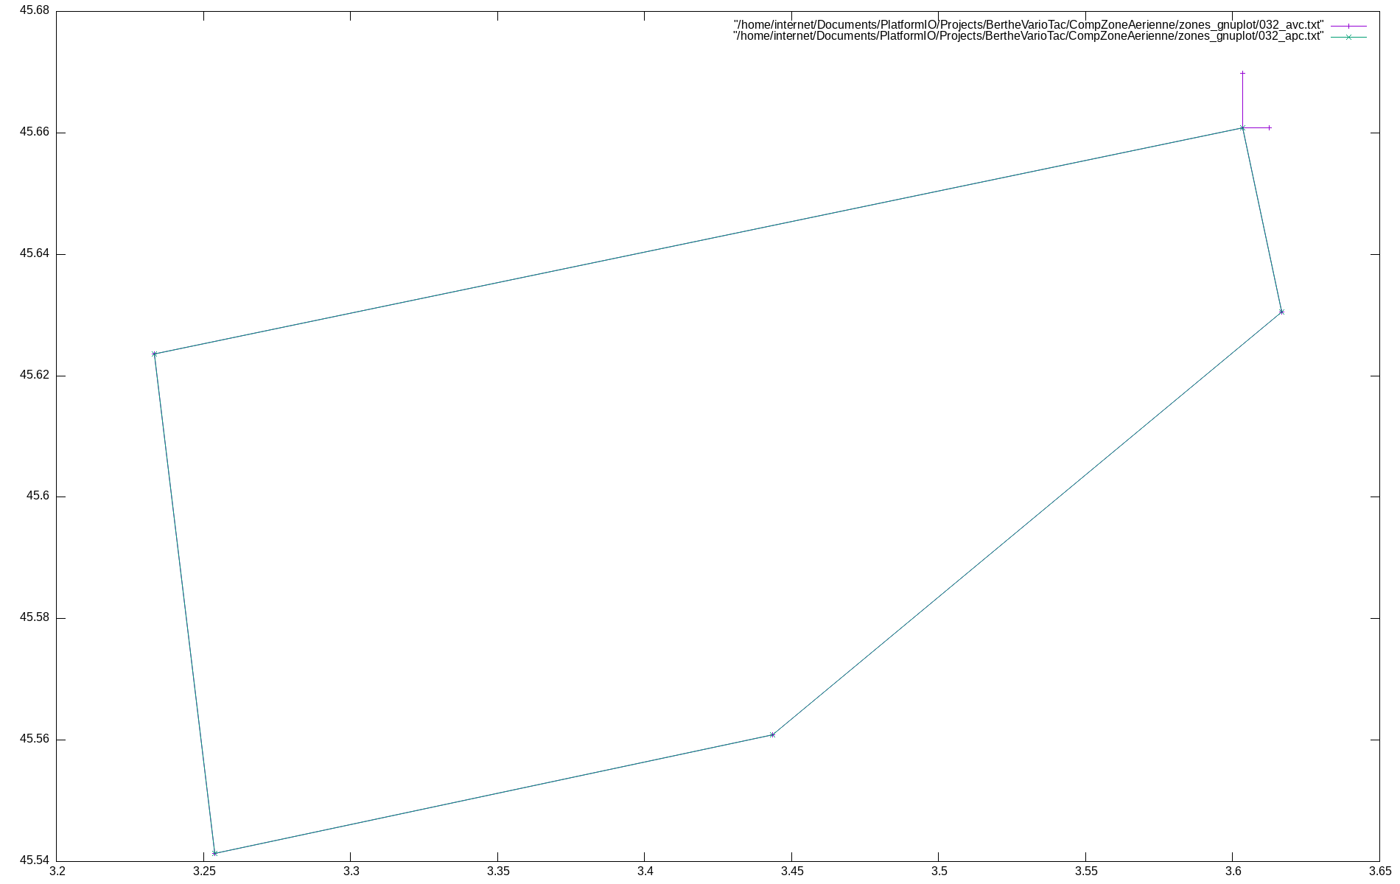
CompZoneAerienne/zones_gnuplot/032.png
