gitberthe/BertheVarioTac/CompZoneAerienne/zones_gnuplot/034.png

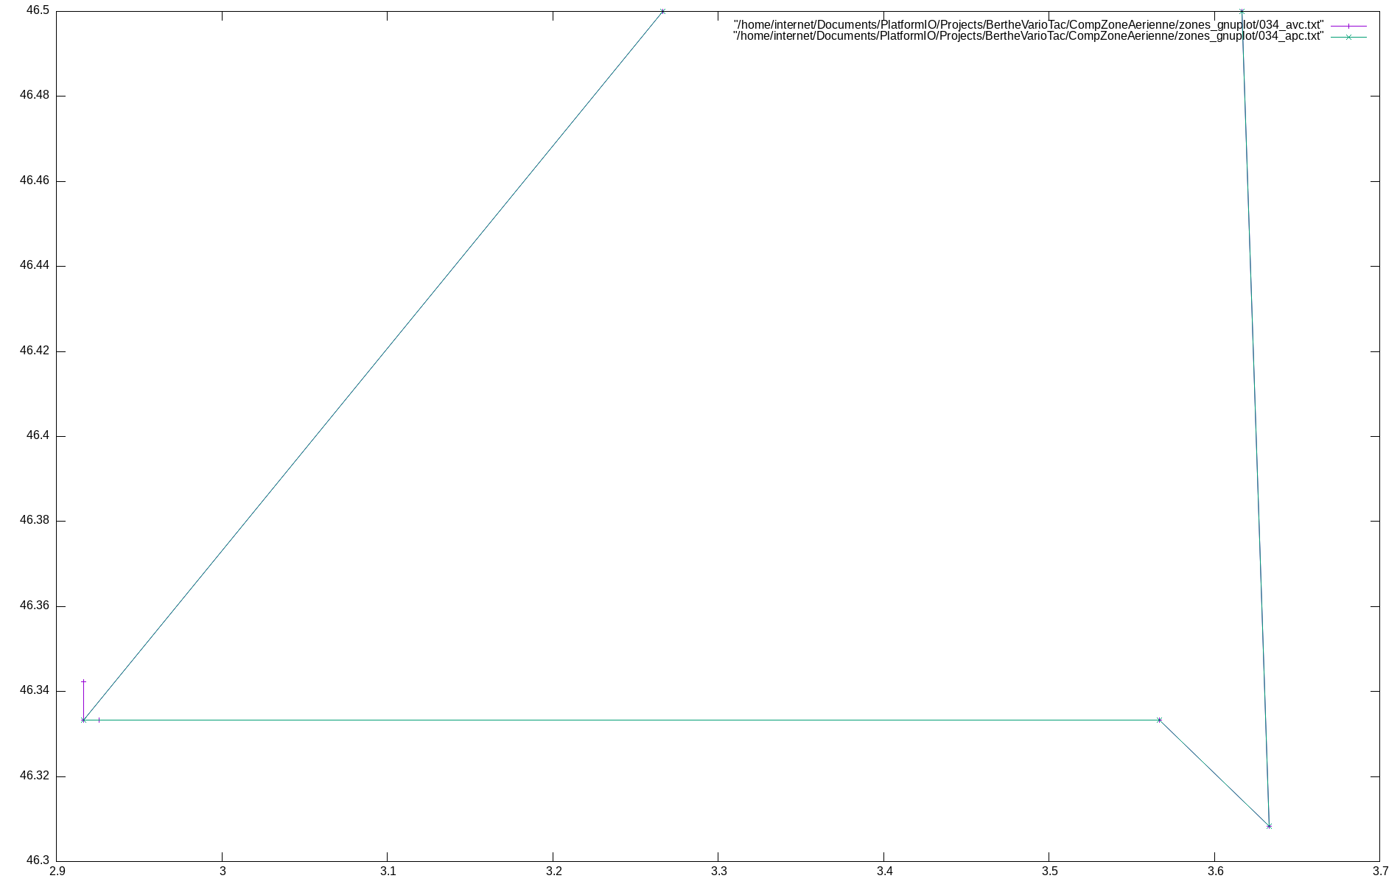
CompZoneAerienne/zones_gnuplot/034.png
