gitberthe/BertheVarioTac/CompZoneAerienne/zones_gnuplot/035.png

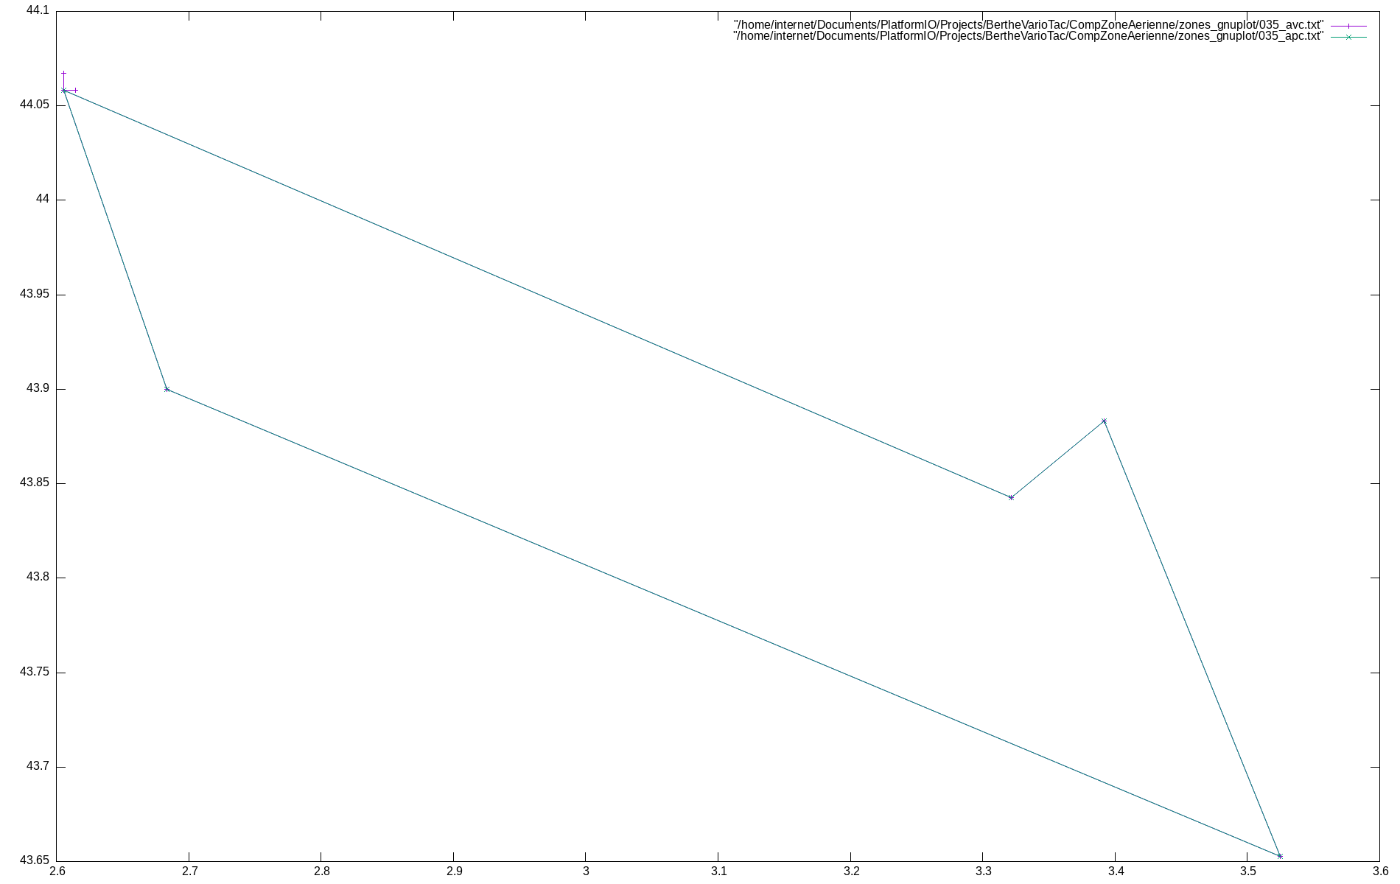
CompZoneAerienne/zones_gnuplot/035.png
