gitberthe/BertheVarioTac/CompZoneAerienne/zones_gnuplot/036.png

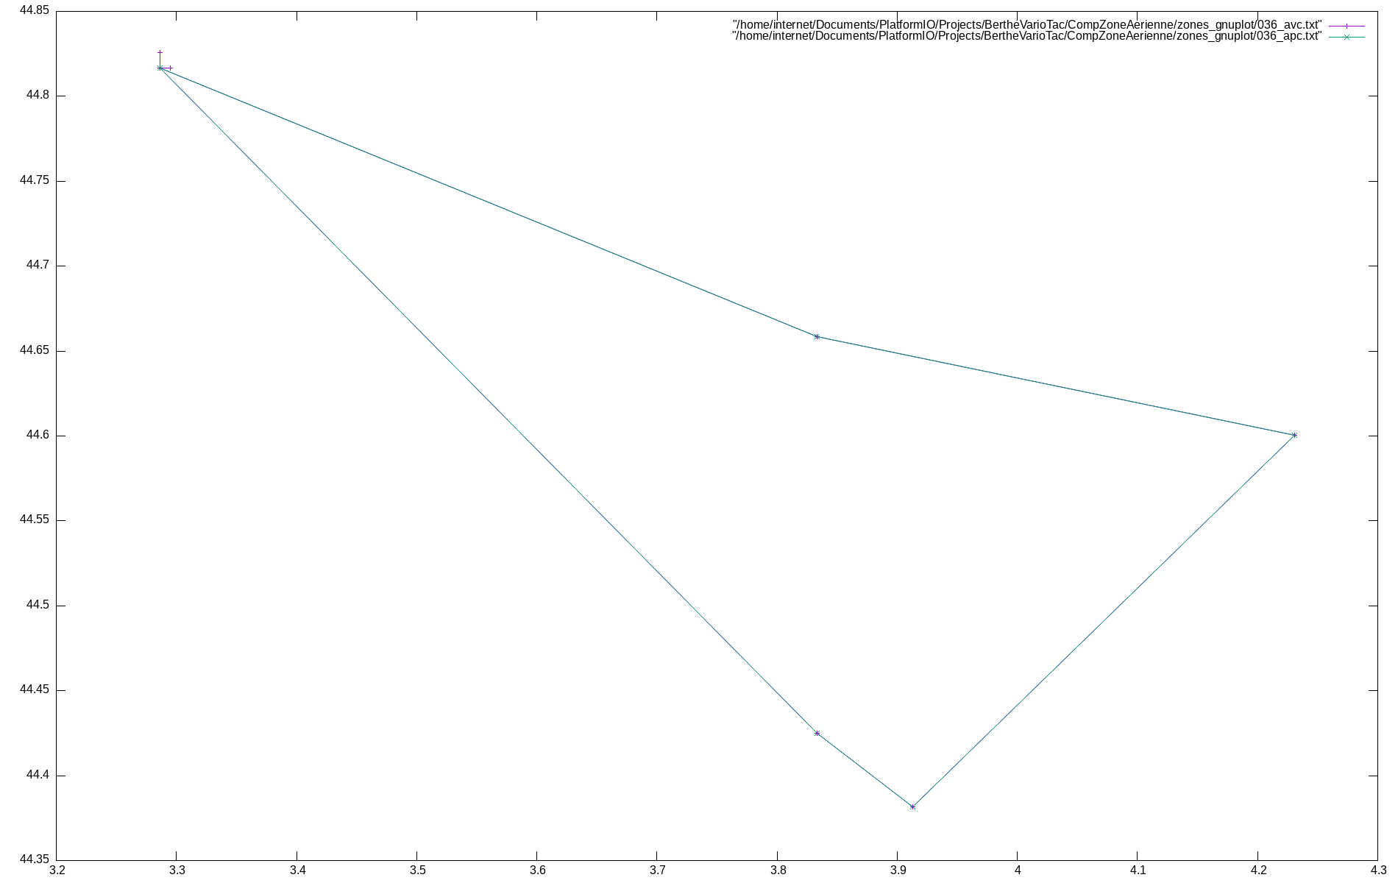
CompZoneAerienne/zones_gnuplot/036.png
