gitberthe/BertheVarioTac/CompZoneAerienne/zones_gnuplot/037.png

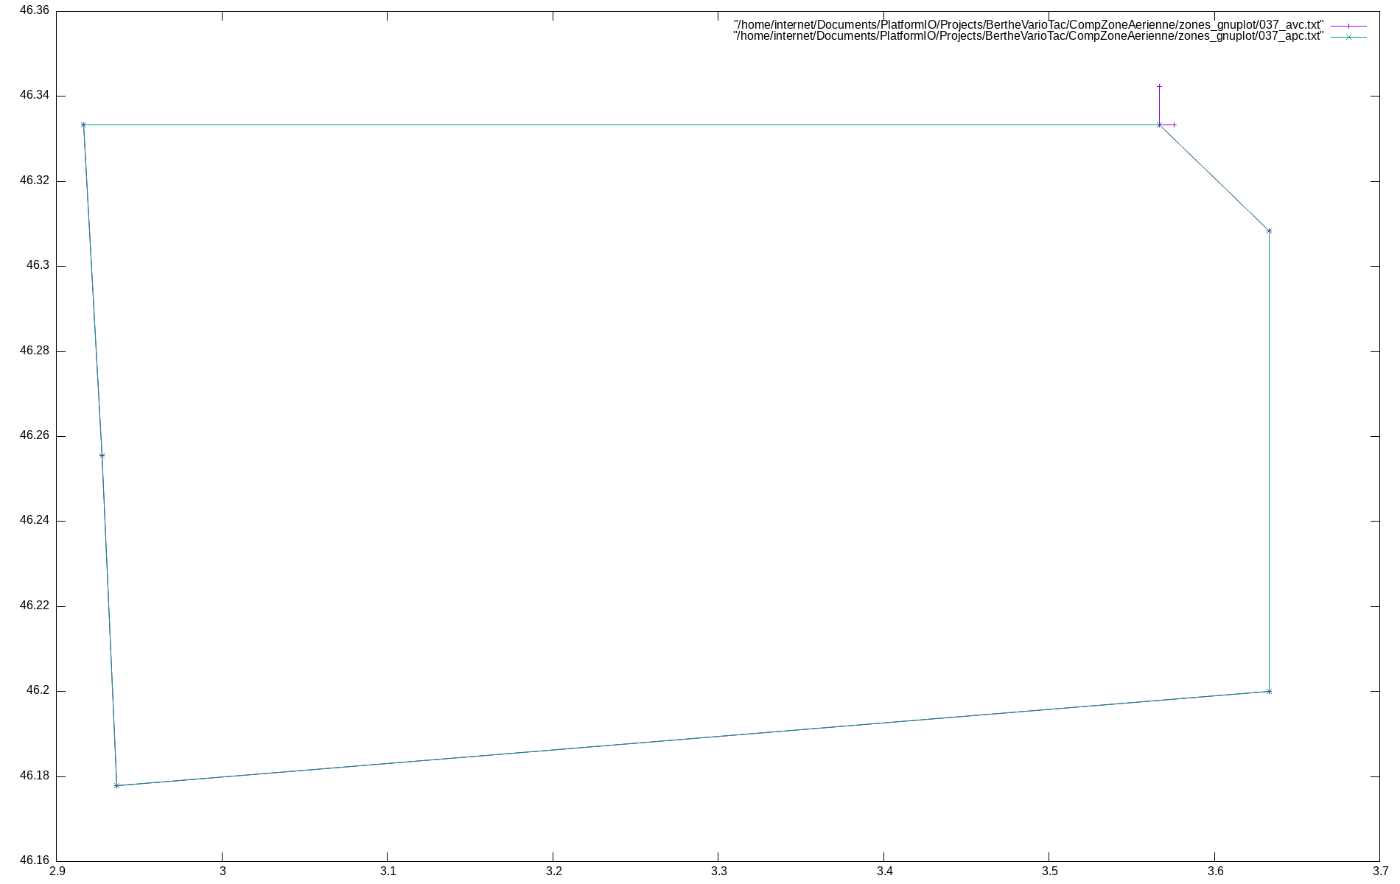
CompZoneAerienne/zones_gnuplot/037.png
