gitberthe/BertheVarioTac/CompZoneAerienne/zones_gnuplot/038.png

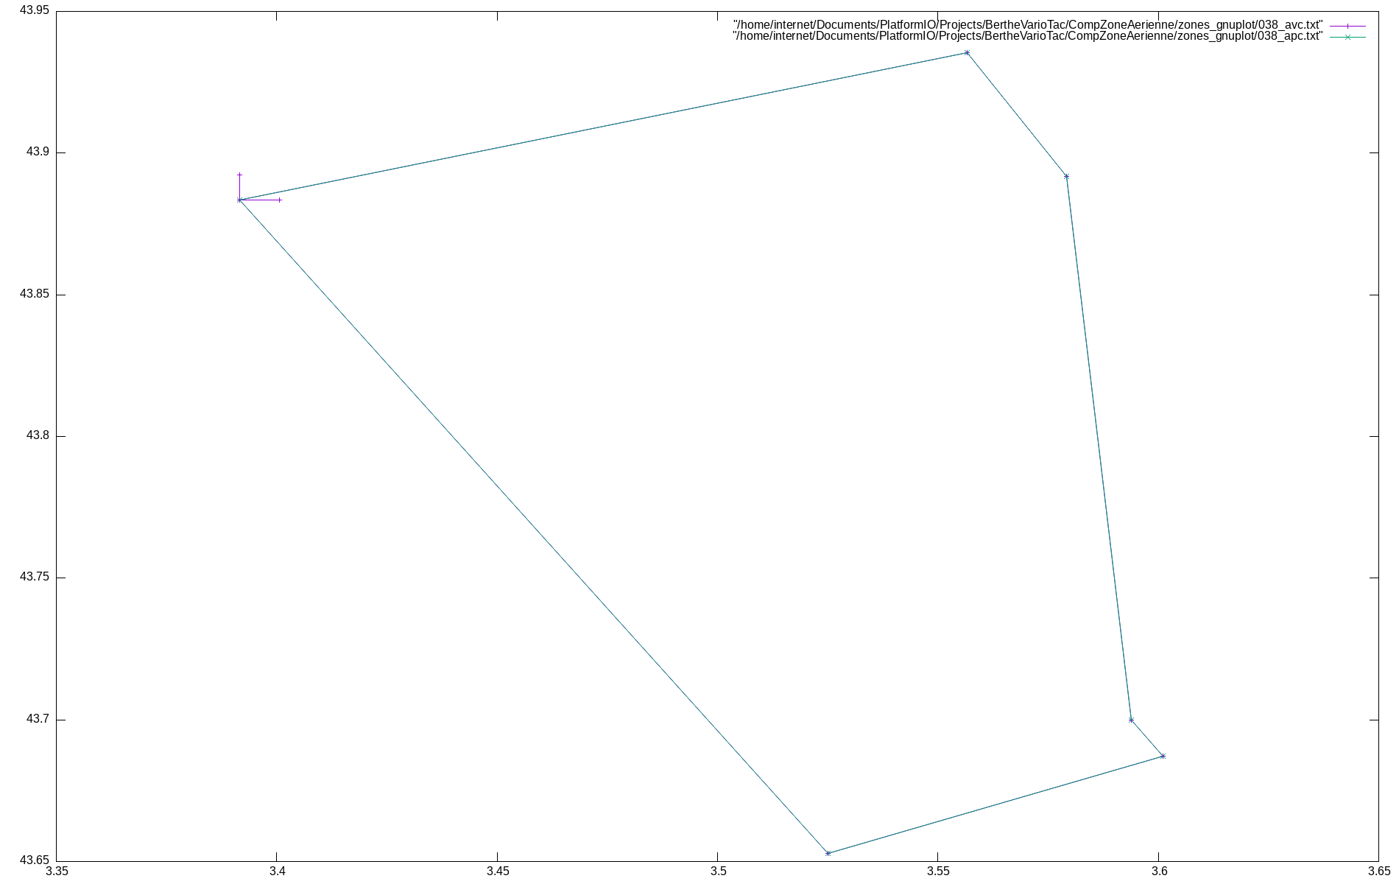
CompZoneAerienne/zones_gnuplot/038.png
