gitberthe/BertheVarioTac/CompZoneAerienne/zones_gnuplot/039.png

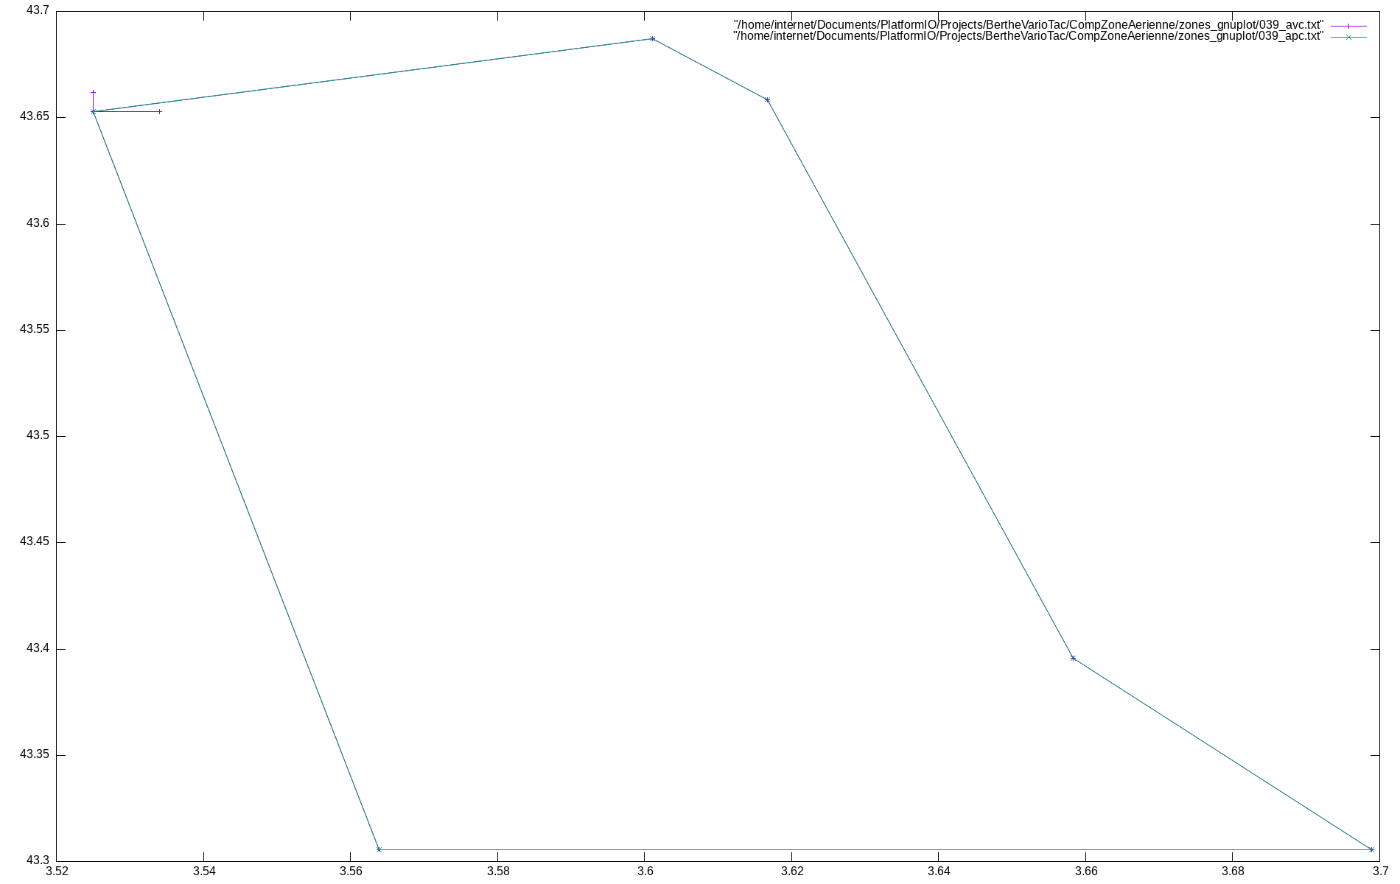
CompZoneAerienne/zones_gnuplot/039.png
