gitberthe/BertheVarioTac/CompZoneAerienne/zones_gnuplot/040.png

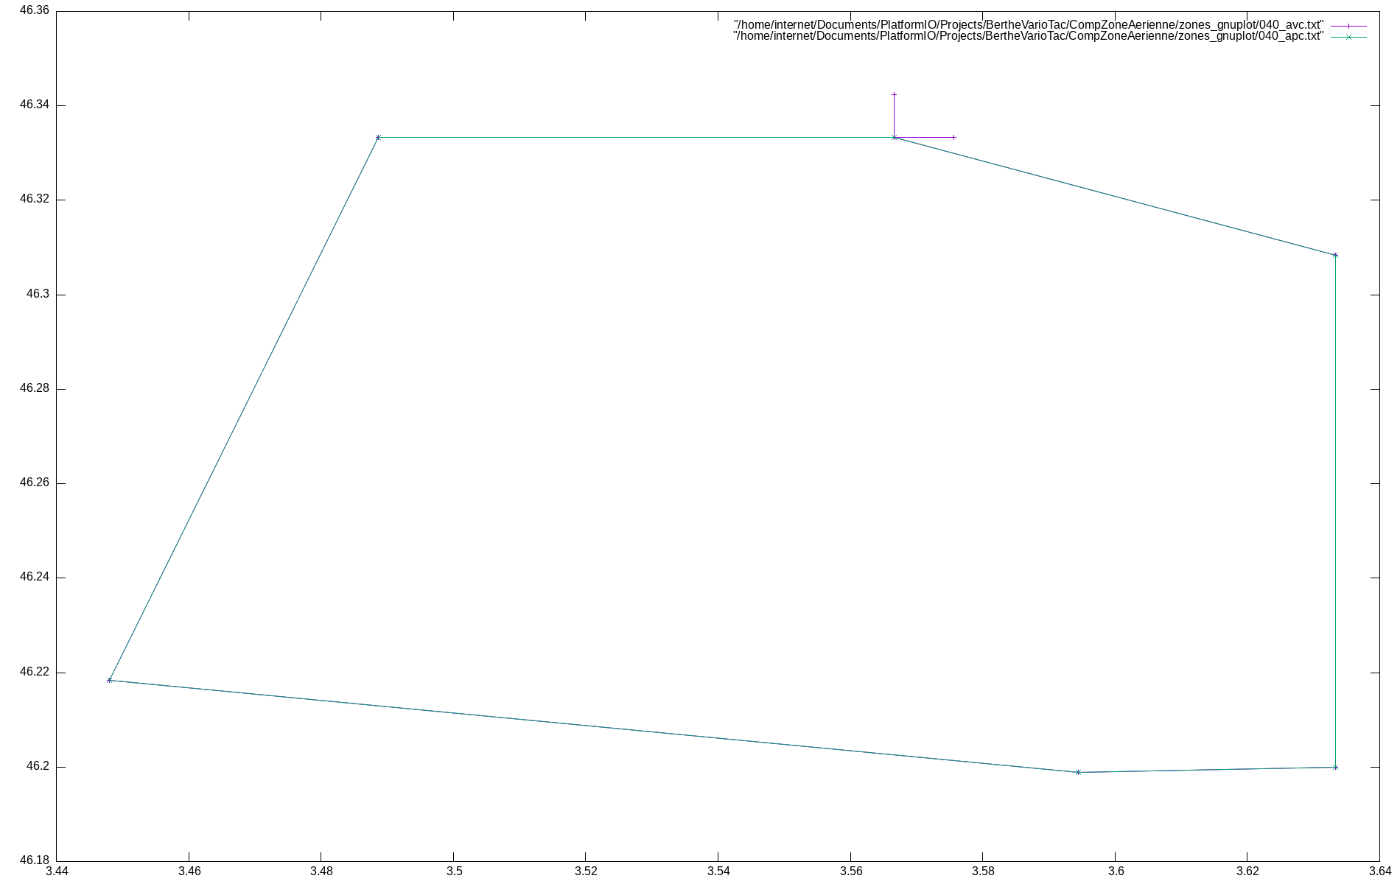
CompZoneAerienne/zones_gnuplot/040.png
