gitberthe/BertheVarioTac/CompZoneAerienne/zones_gnuplot/042.png

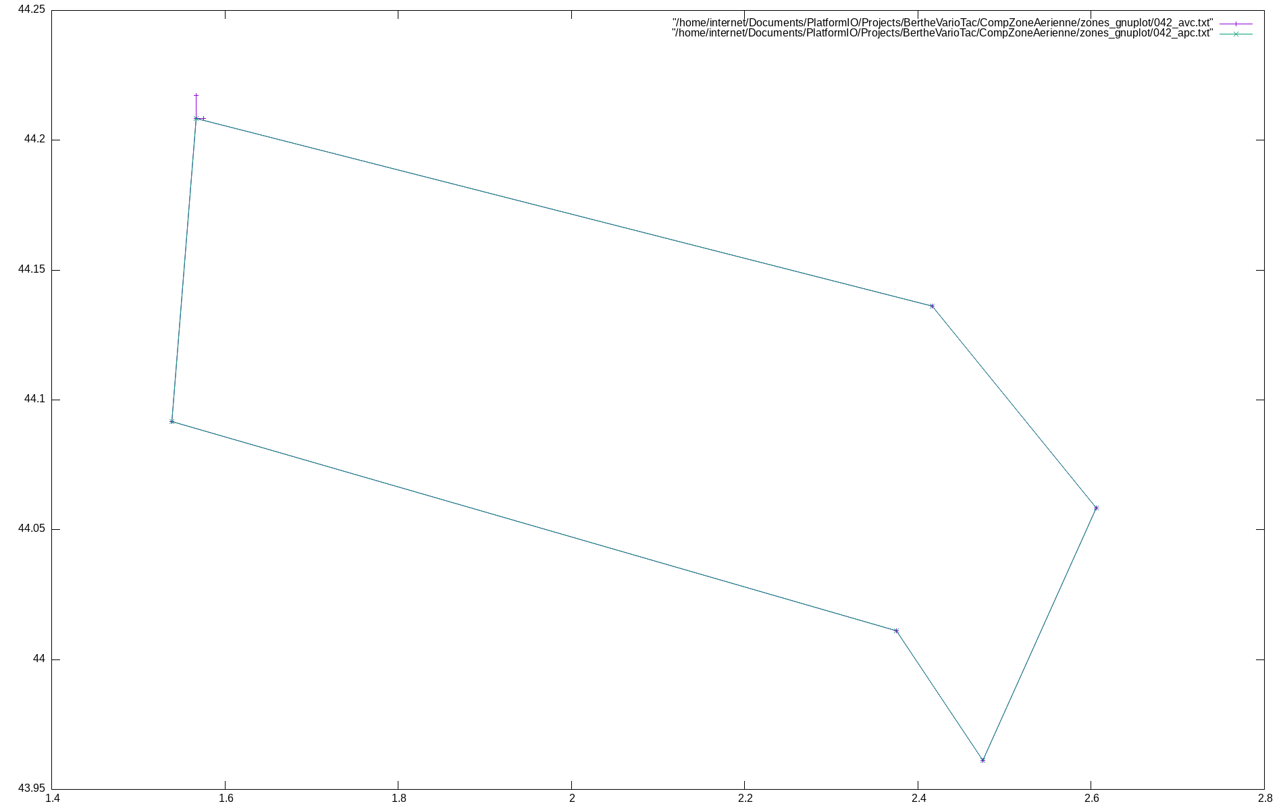
CompZoneAerienne/zones_gnuplot/042.png
