gitberthe/BertheVarioTac/CompZoneAerienne/zones_gnuplot/043.png

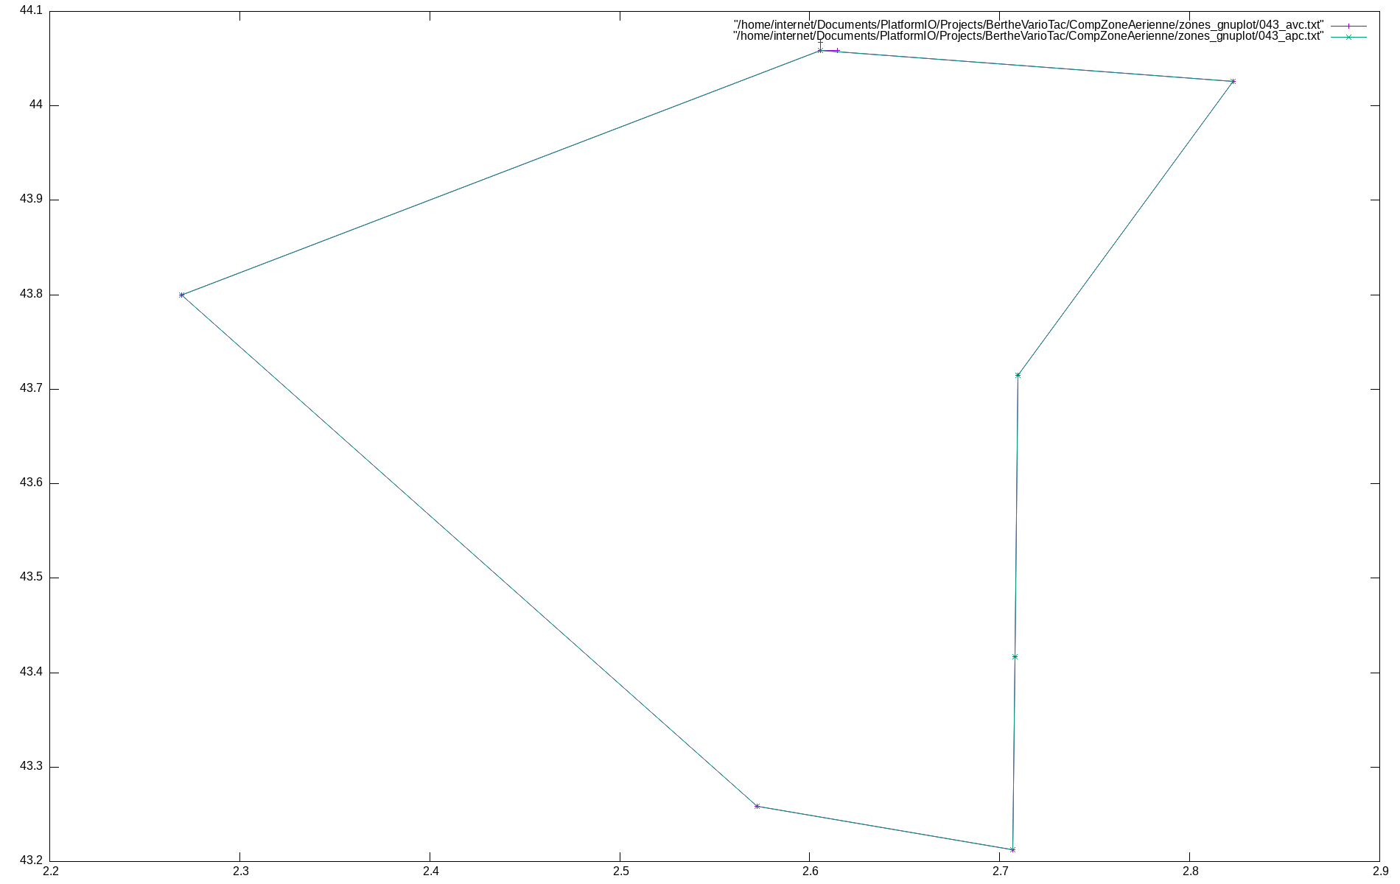
CompZoneAerienne/zones_gnuplot/043.png
