gitberthe/BertheVarioTac/CompZoneAerienne/zones_gnuplot/044.png

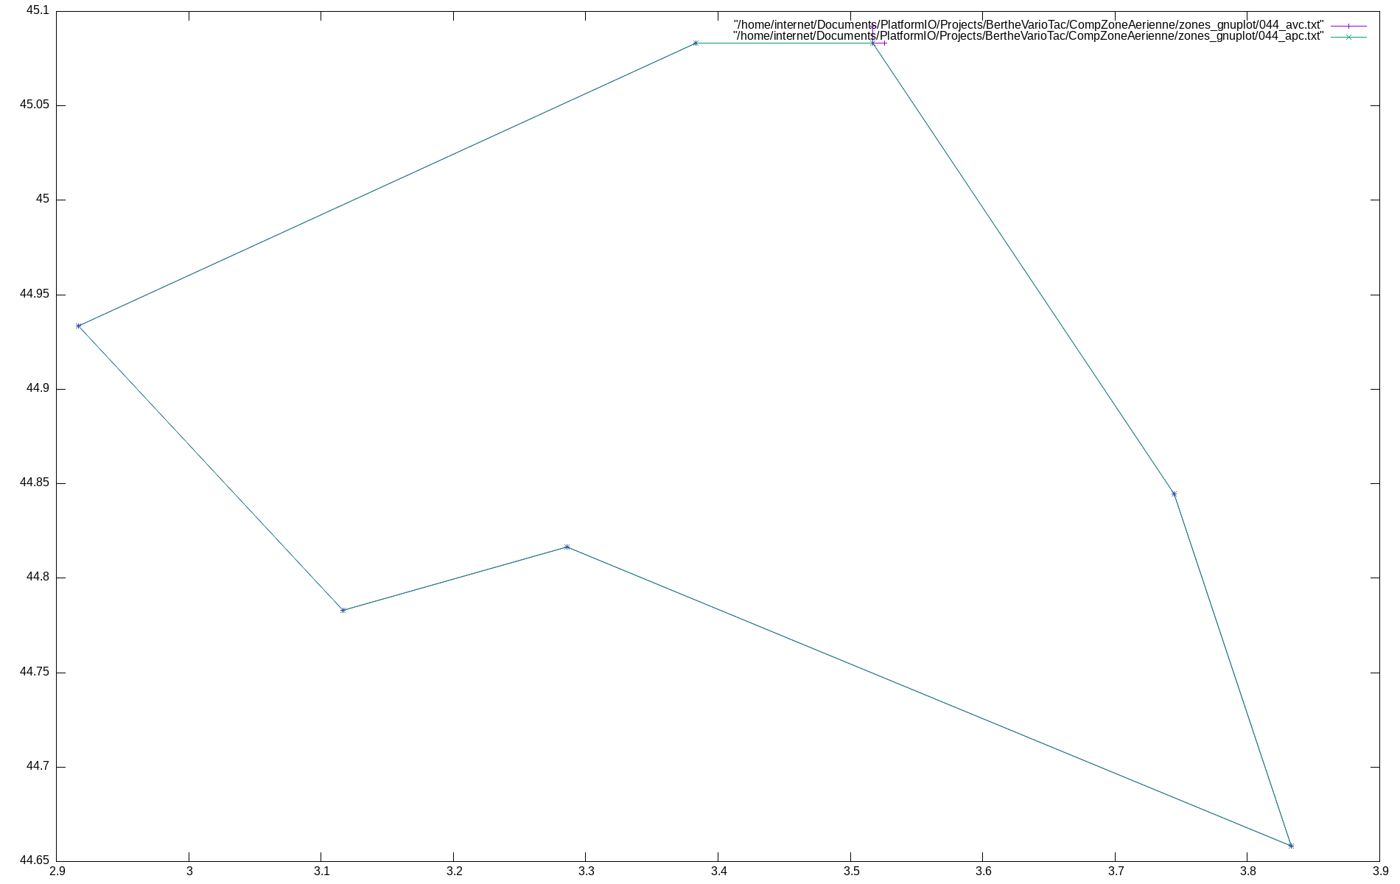
CompZoneAerienne/zones_gnuplot/044.png
