gitberthe/BertheVarioTac/CompZoneAerienne/zones_gnuplot/046.png

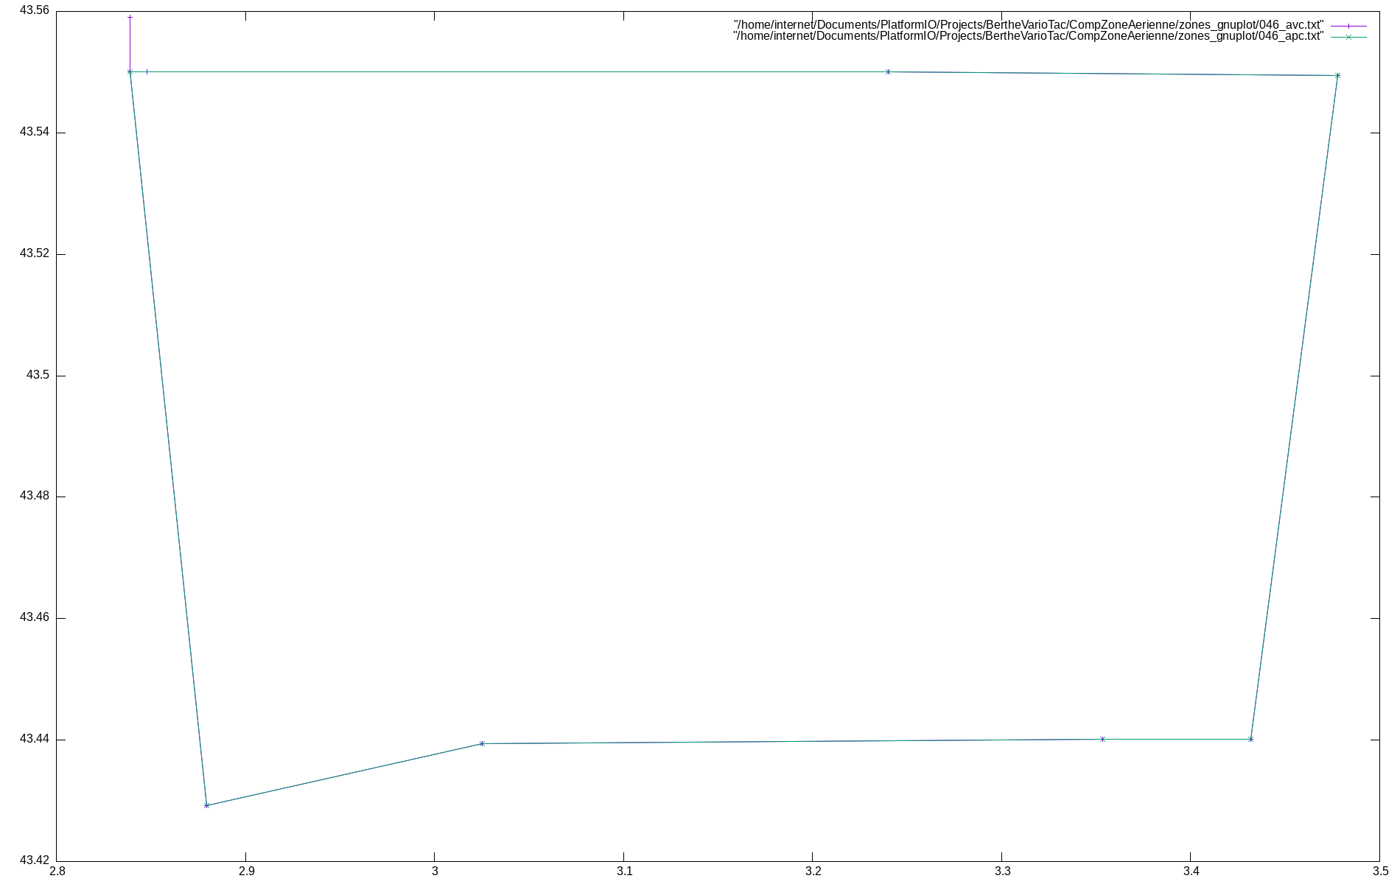
CompZoneAerienne/zones_gnuplot/046.png
