gitberthe/BertheVarioTac/CompZoneAerienne/zones_gnuplot/047.png

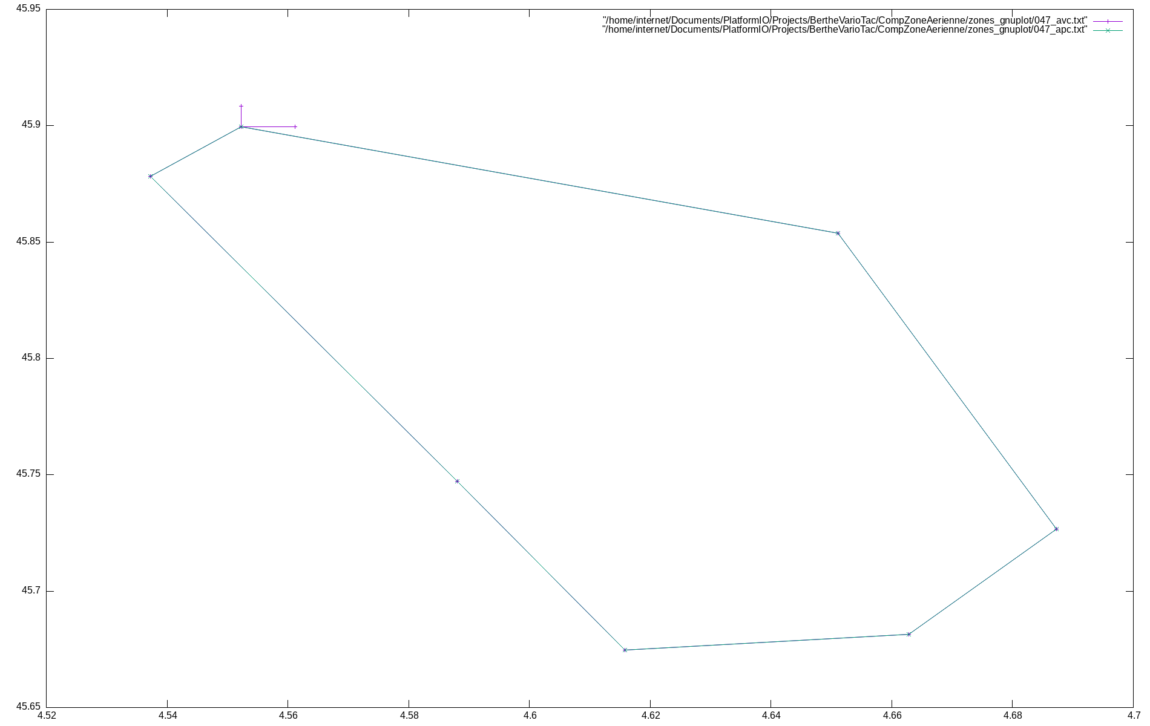
CompZoneAerienne/zones_gnuplot/047.png
