gitberthe/BertheVarioTac/CompZoneAerienne/zones_gnuplot/048.png

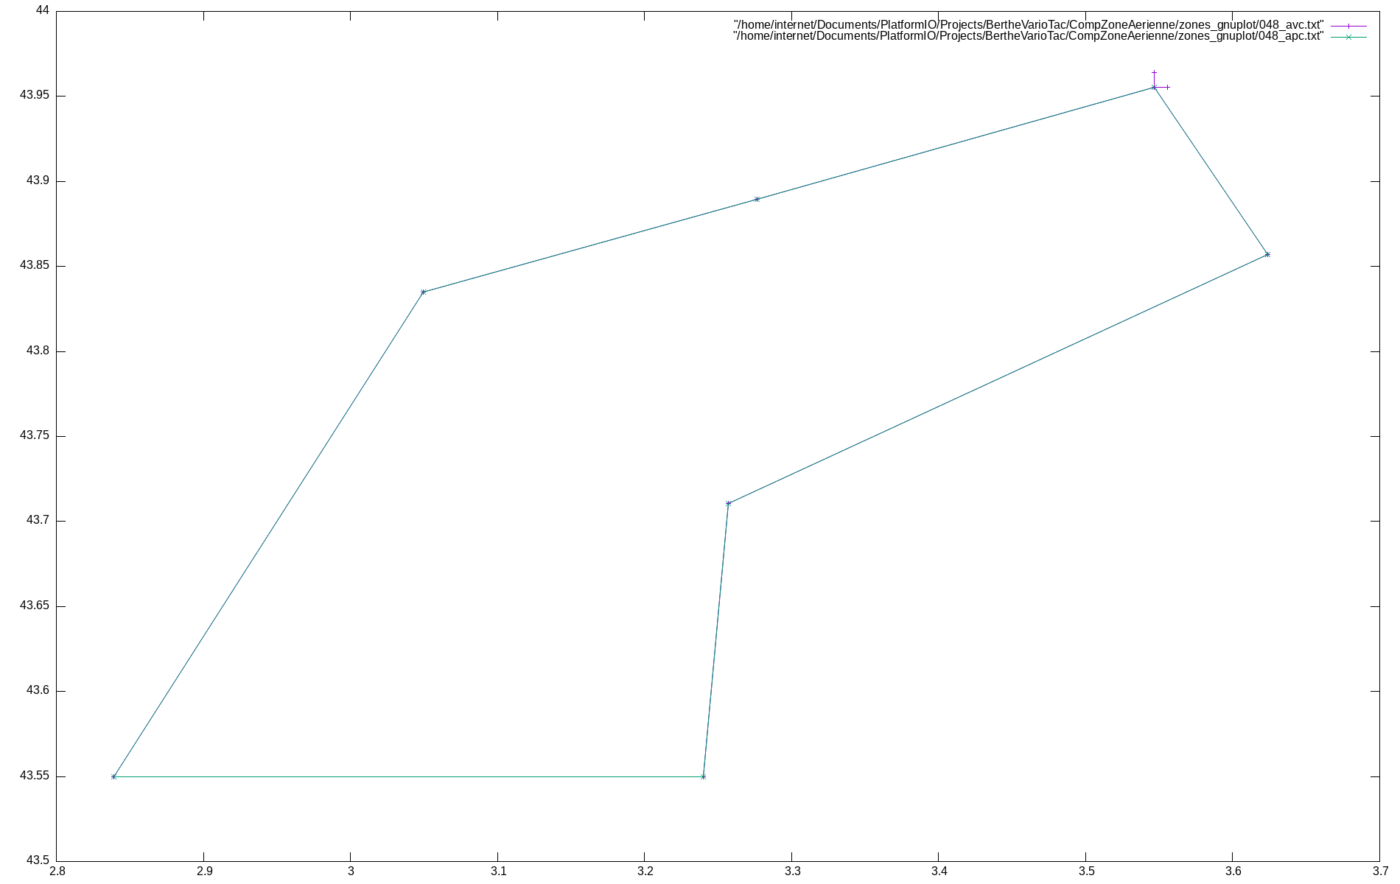
CompZoneAerienne/zones_gnuplot/048.png
