gitberthe/BertheVarioTac/CompZoneAerienne/zones_gnuplot/051.png

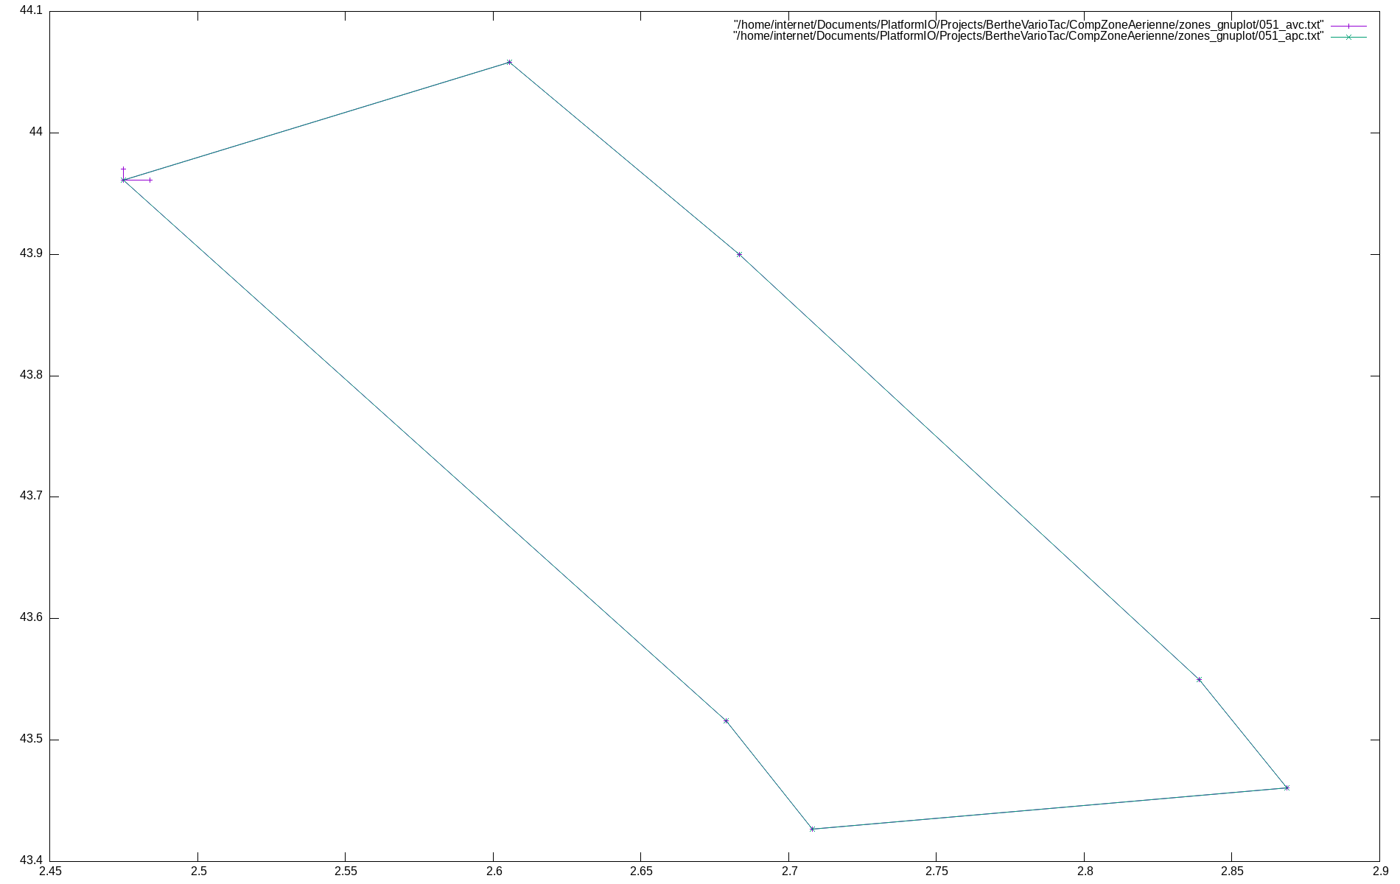
CompZoneAerienne/zones_gnuplot/051.png
