gitberthe/BertheVarioTac/CompZoneAerienne/zones_gnuplot/052.png

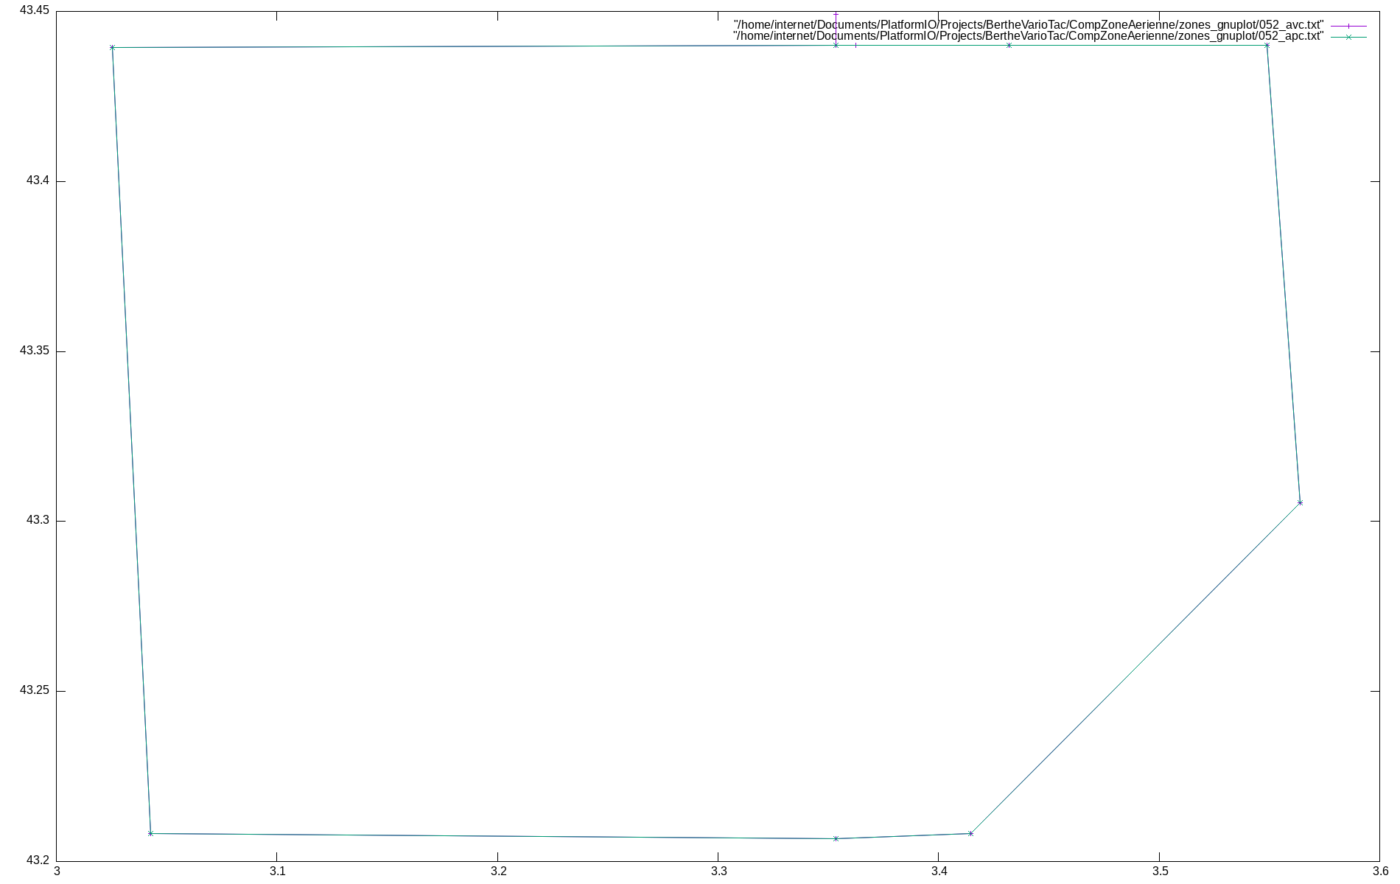
CompZoneAerienne/zones_gnuplot/052.png
