gitberthe/BertheVarioTac/CompZoneAerienne/zones_gnuplot/054.png

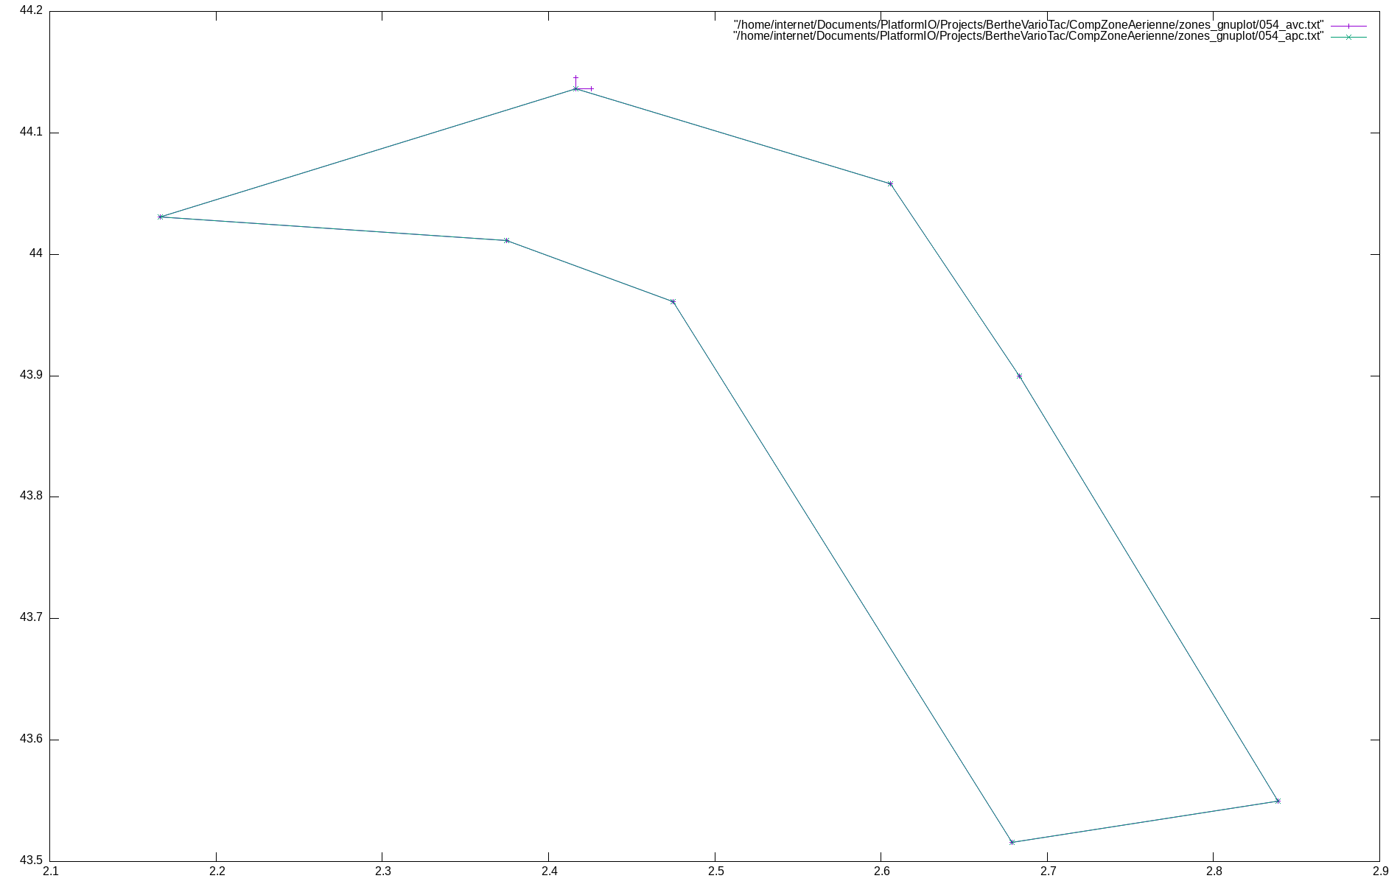
CompZoneAerienne/zones_gnuplot/054.png
