gitberthe/BertheVarioTac/CompZoneAerienne/zones_gnuplot/056.png

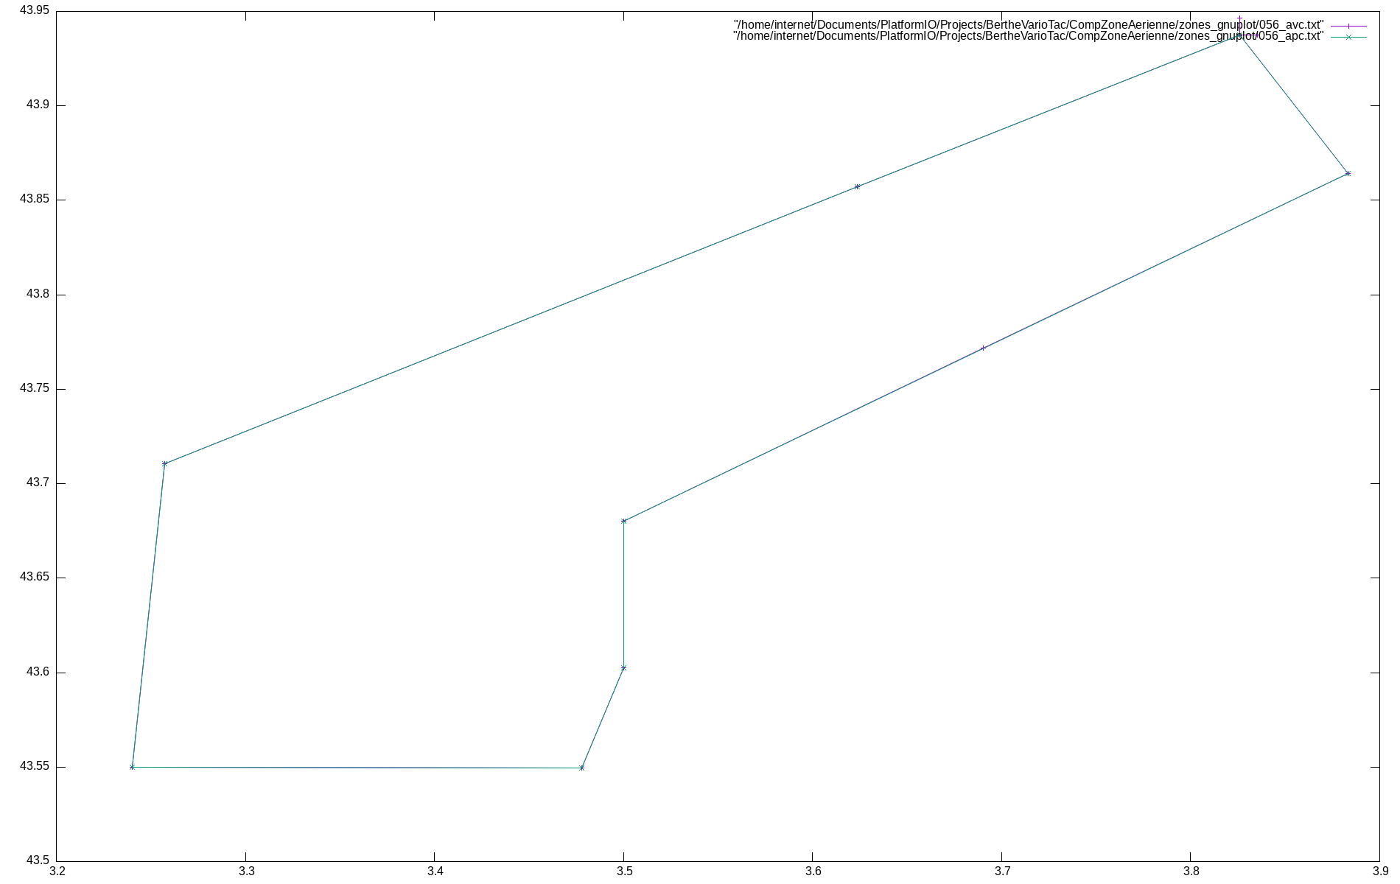
CompZoneAerienne/zones_gnuplot/056.png
