gitberthe/BertheVarioTac/CompZoneAerienne/zones_gnuplot/058.png

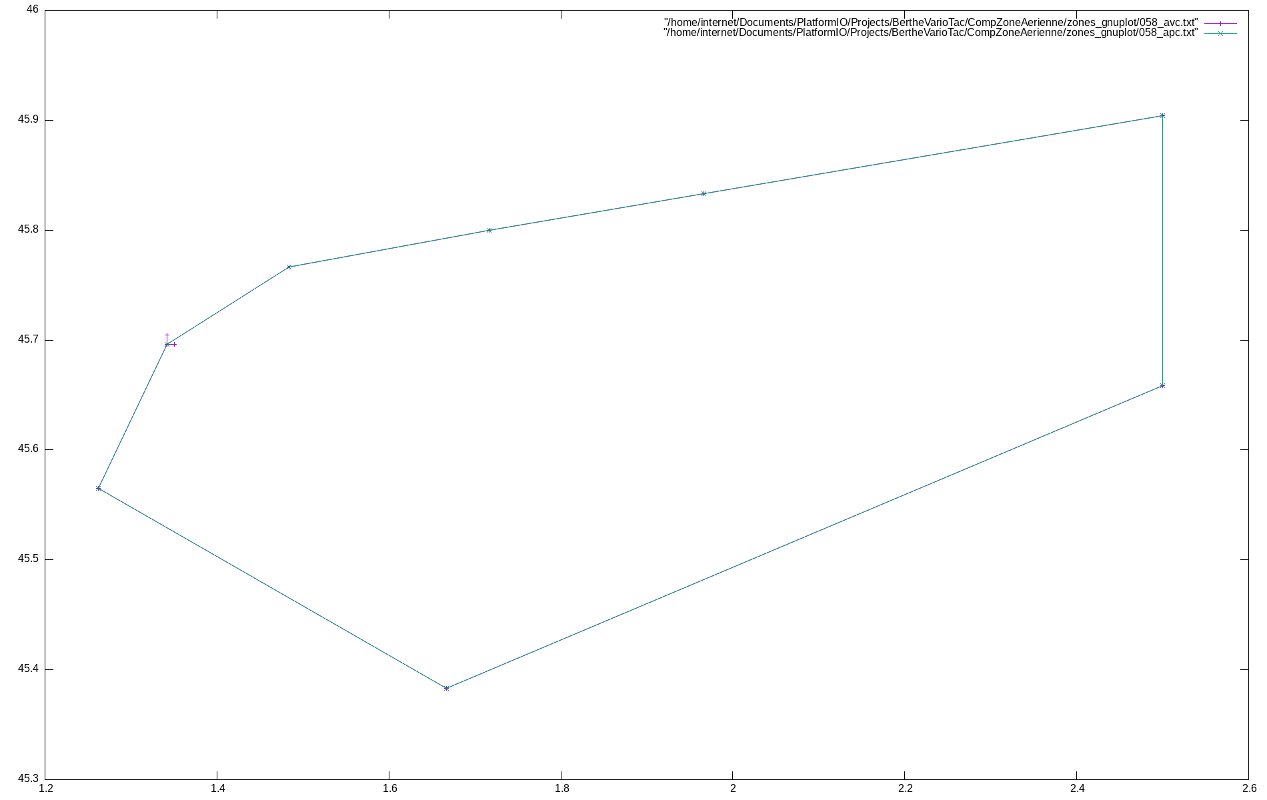
CompZoneAerienne/zones_gnuplot/058.png
