gitberthe/BertheVarioTac/CompZoneAerienne/zones_gnuplot/059.png

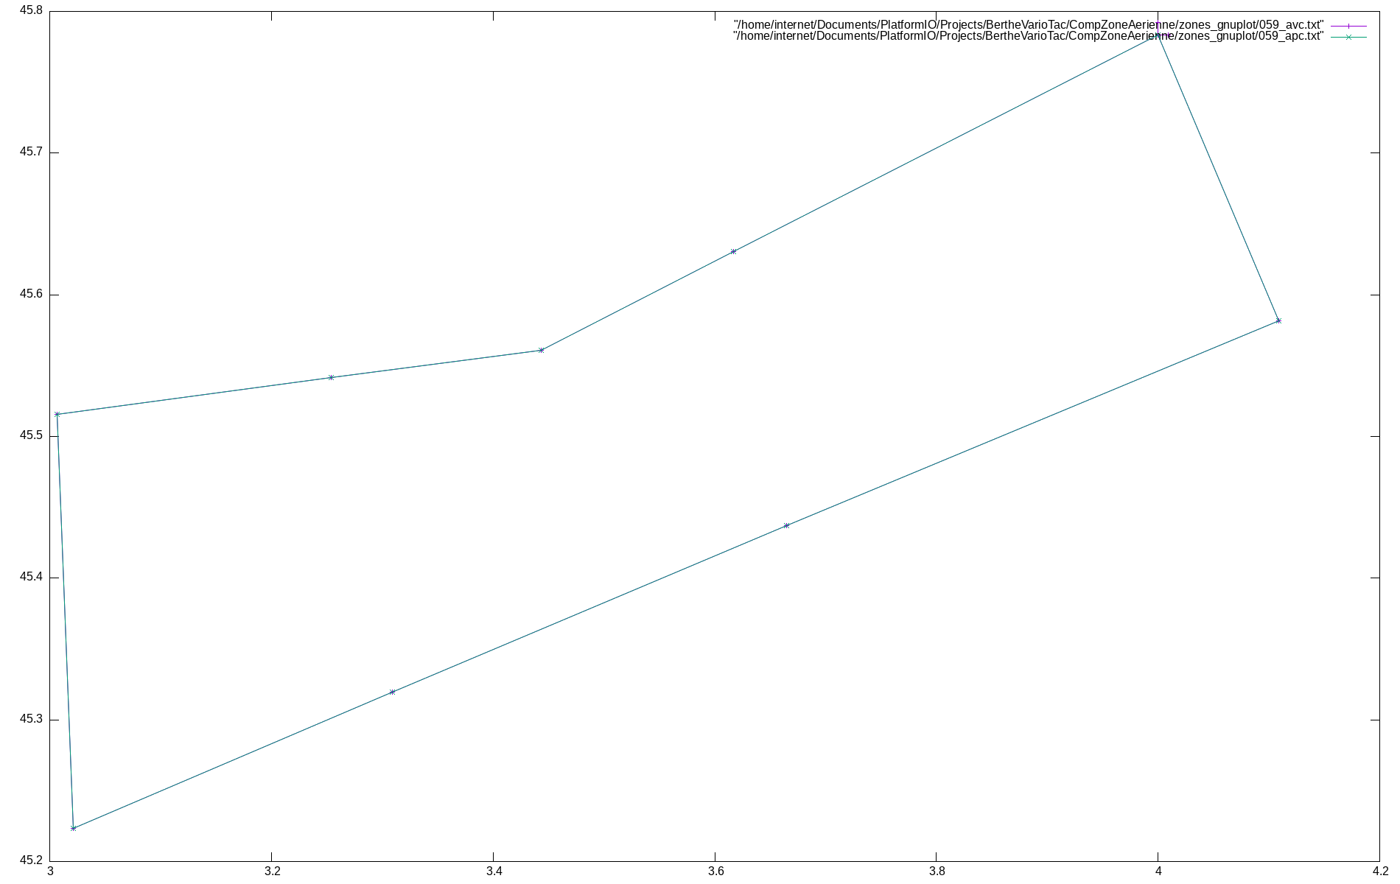
CompZoneAerienne/zones_gnuplot/059.png
