gitberthe/BertheVarioTac/CompZoneAerienne/zones_gnuplot/060.png

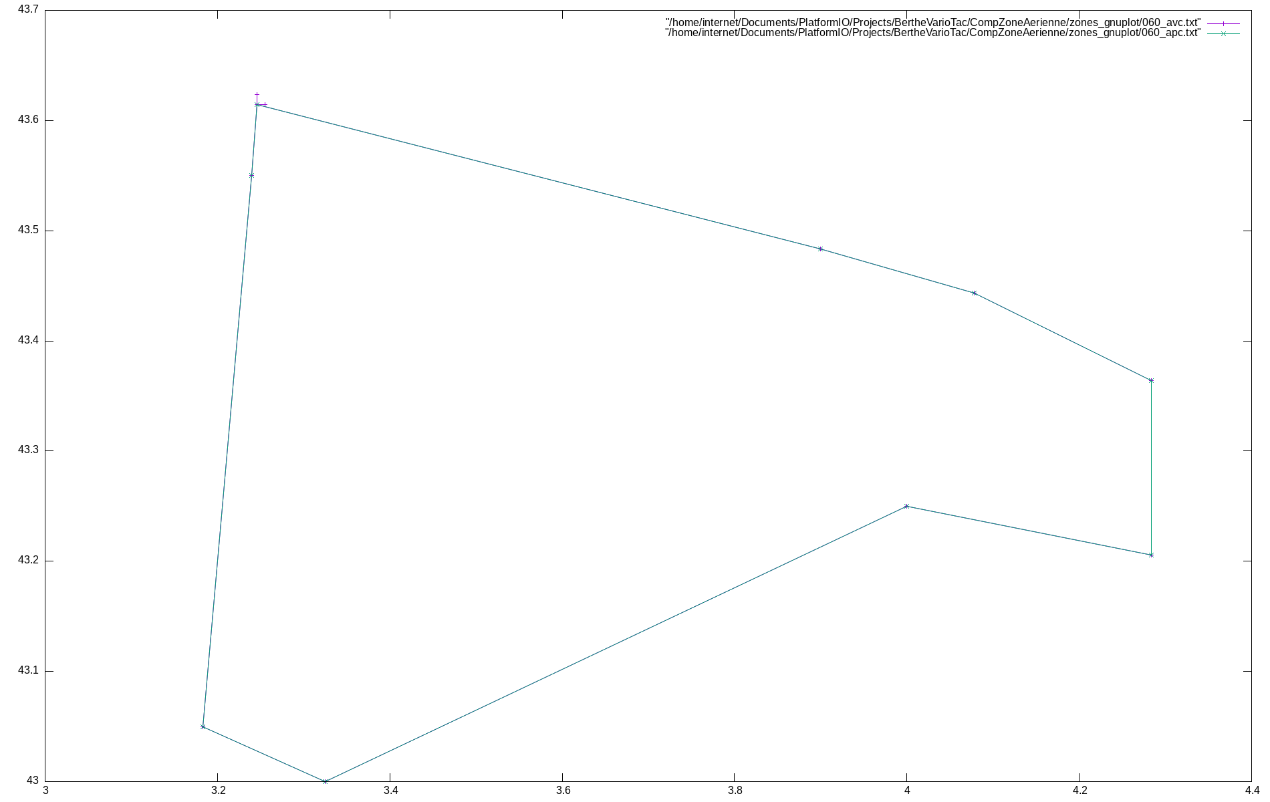
CompZoneAerienne/zones_gnuplot/060.png
