gitberthe/BertheVarioTac/CompZoneAerienne/zones_gnuplot/062.png

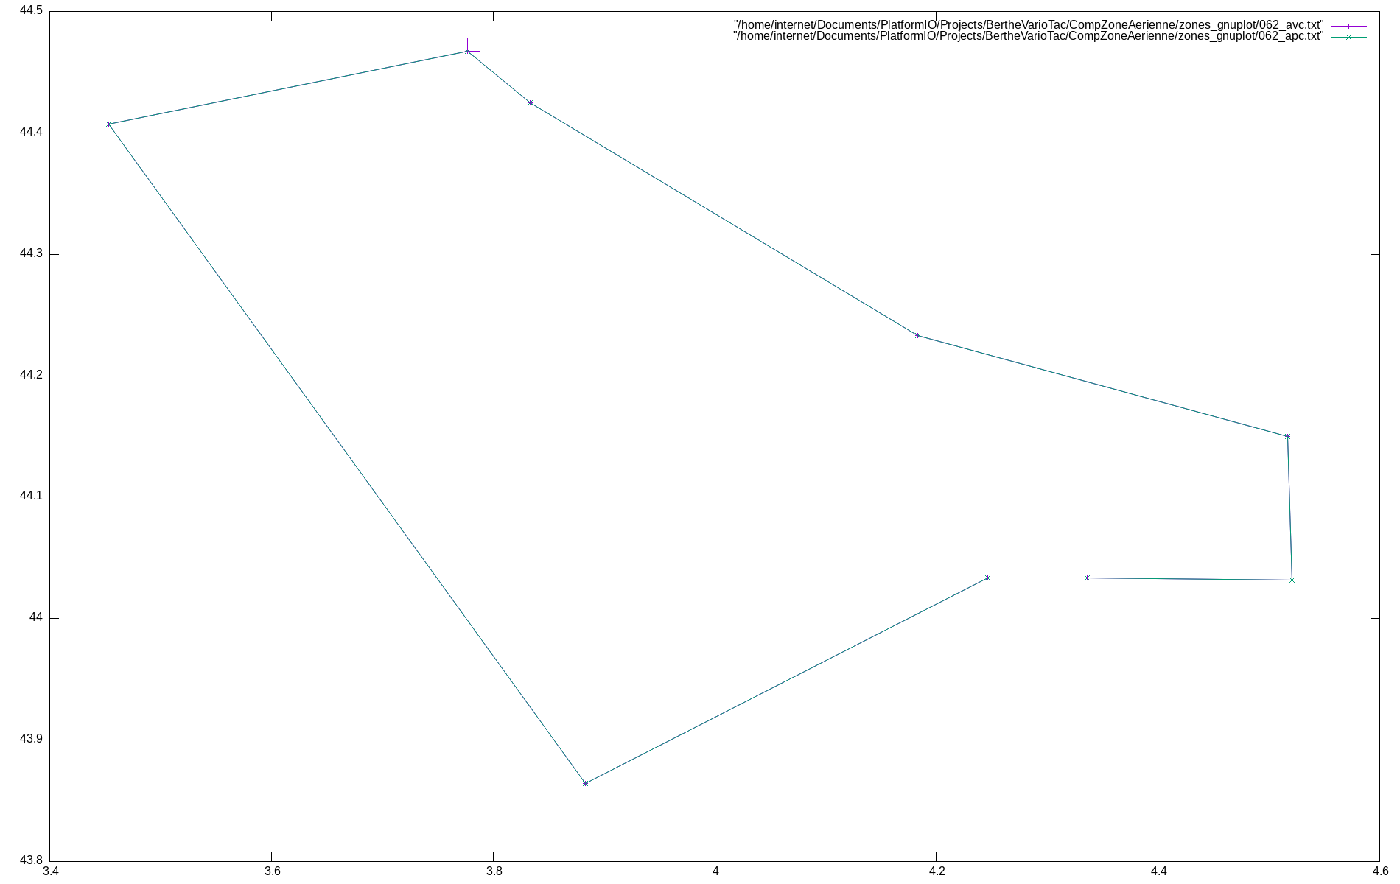
CompZoneAerienne/zones_gnuplot/062.png
