gitberthe/BertheVarioTac/CompZoneAerienne/zones_gnuplot/064.png

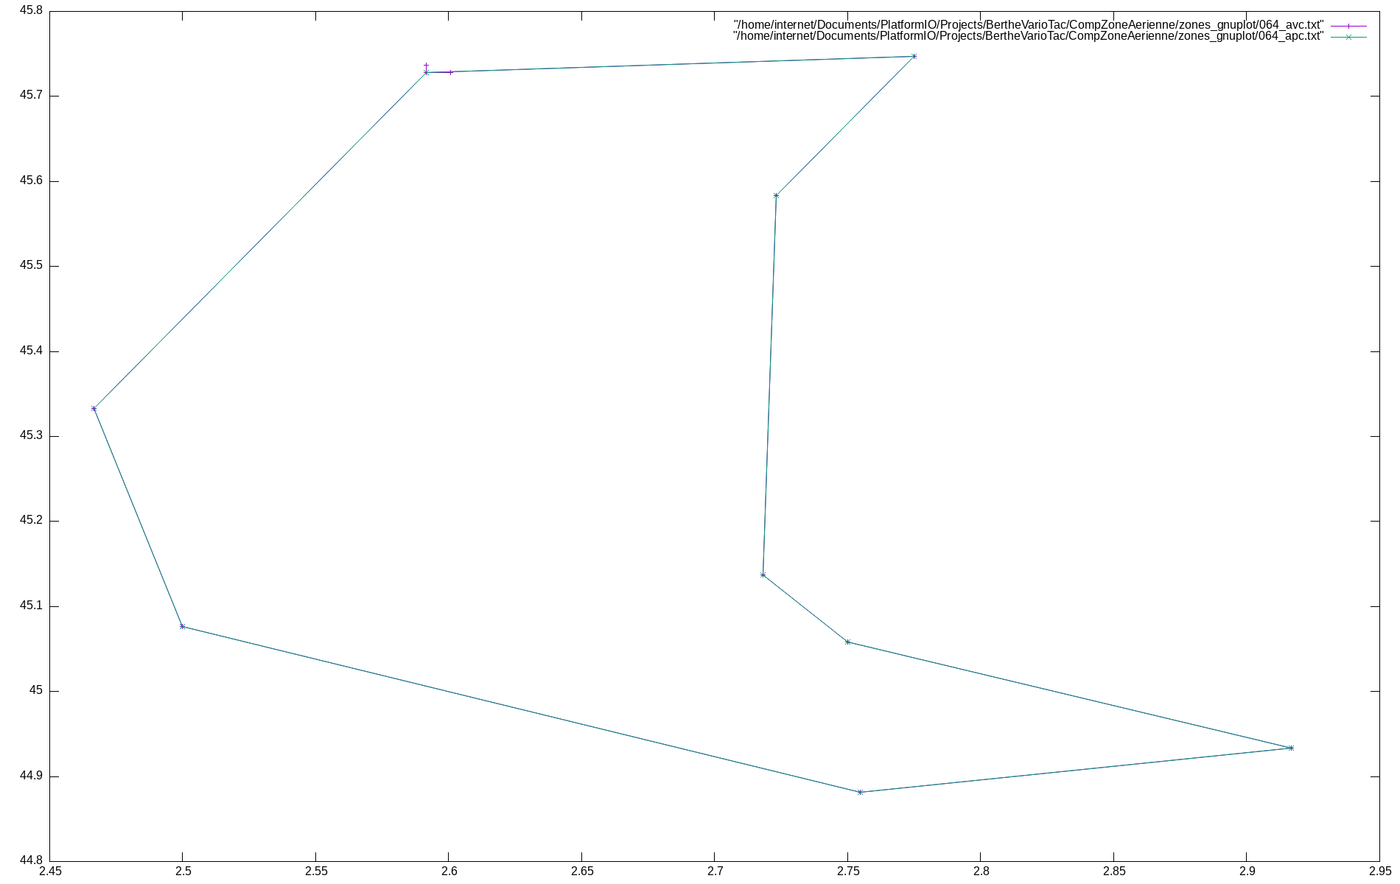
CompZoneAerienne/zones_gnuplot/064.png
