gitberthe/BertheVarioTac/CompZoneAerienne/zones_gnuplot/065.png

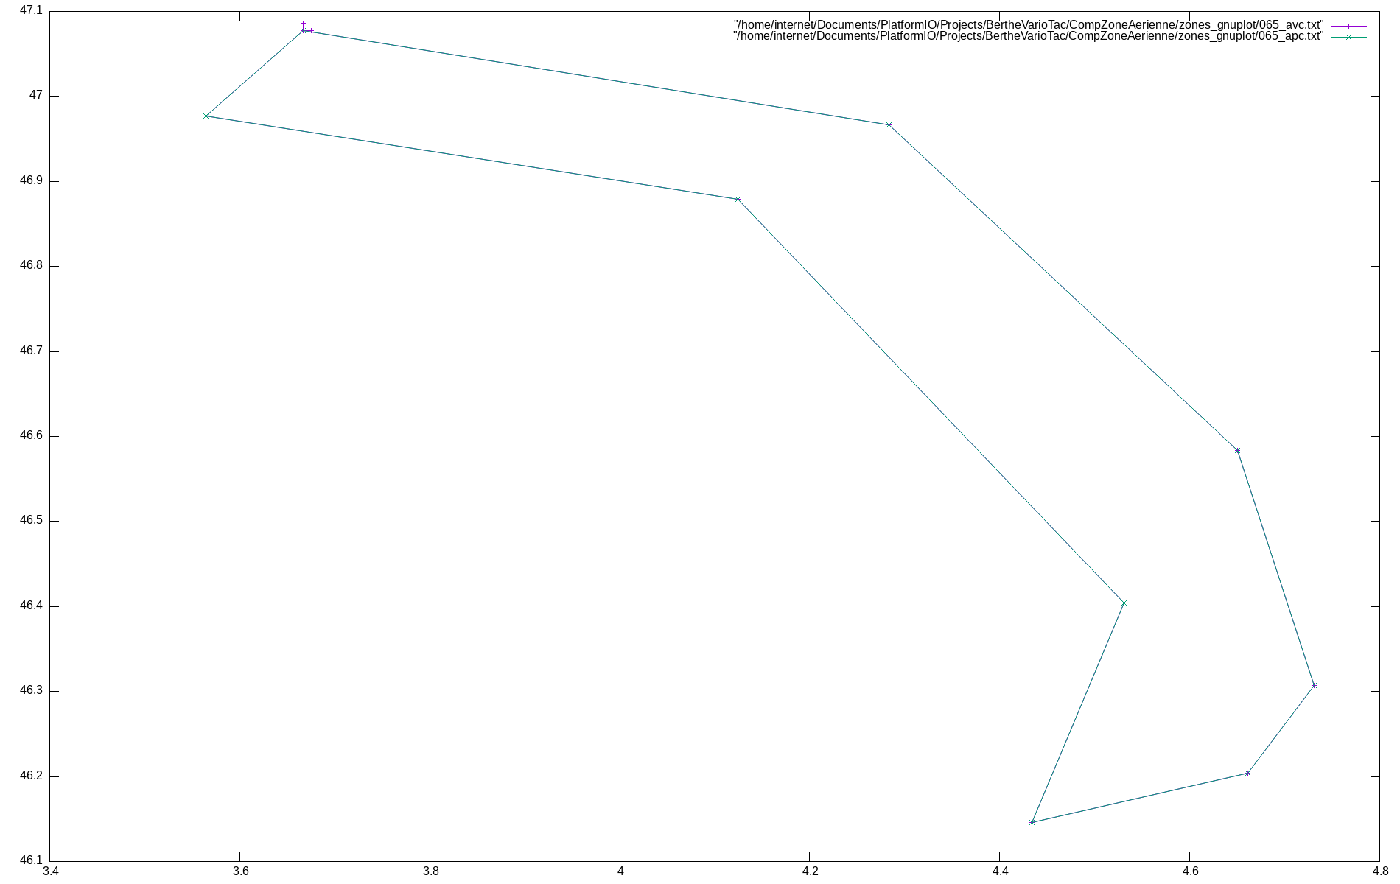
CompZoneAerienne/zones_gnuplot/065.png
