gitberthe/BertheVarioTac/CompZoneAerienne/zones_gnuplot/066.png

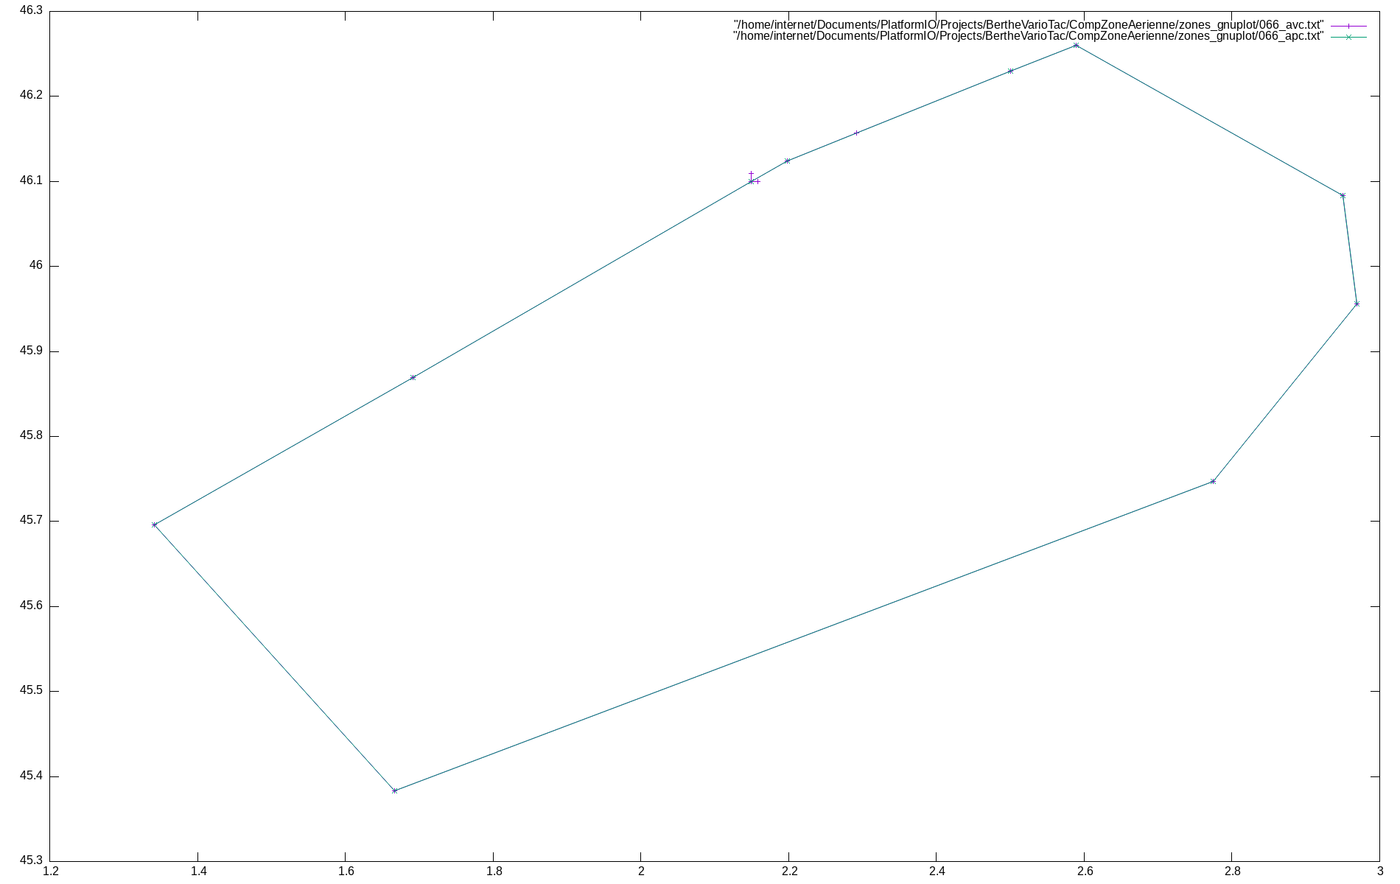
CompZoneAerienne/zones_gnuplot/066.png
