gitberthe/BertheVarioTac/CompZoneAerienne/zones_gnuplot/067.png

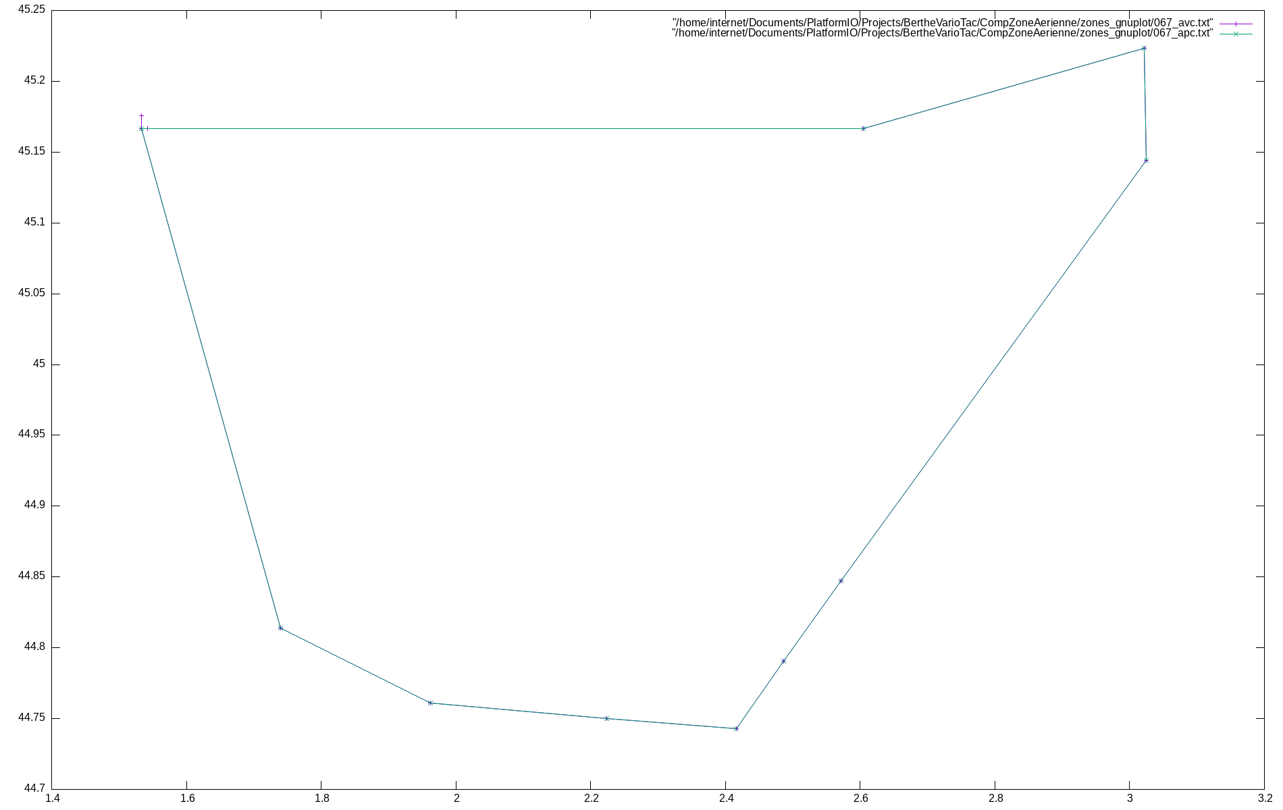
CompZoneAerienne/zones_gnuplot/067.png
