gitberthe/BertheVarioTac/CompZoneAerienne/zones_gnuplot/069.png

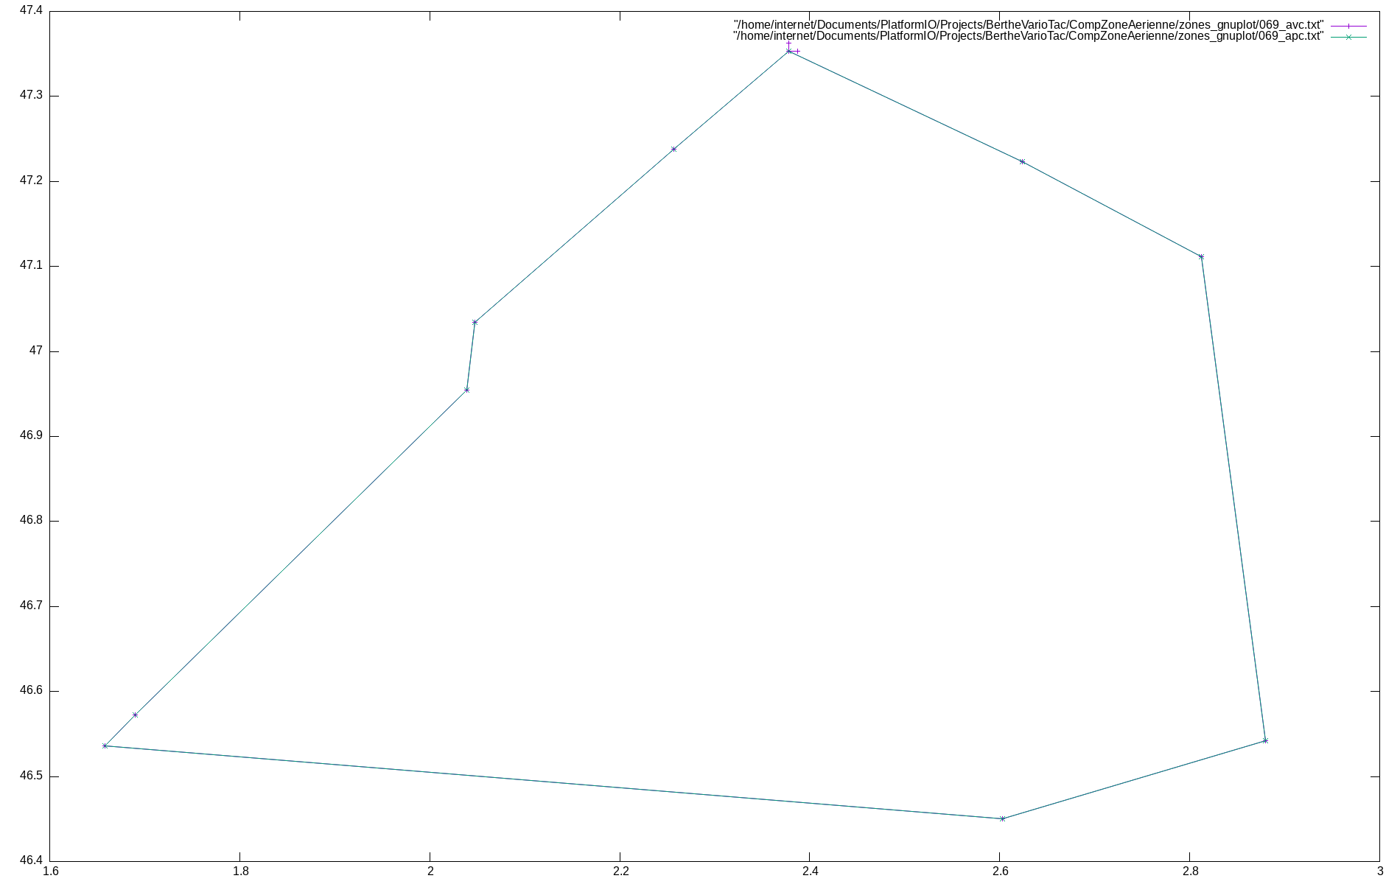
CompZoneAerienne/zones_gnuplot/069.png
