gitberthe/BertheVarioTac/CompZoneAerienne/zones_gnuplot/070.png

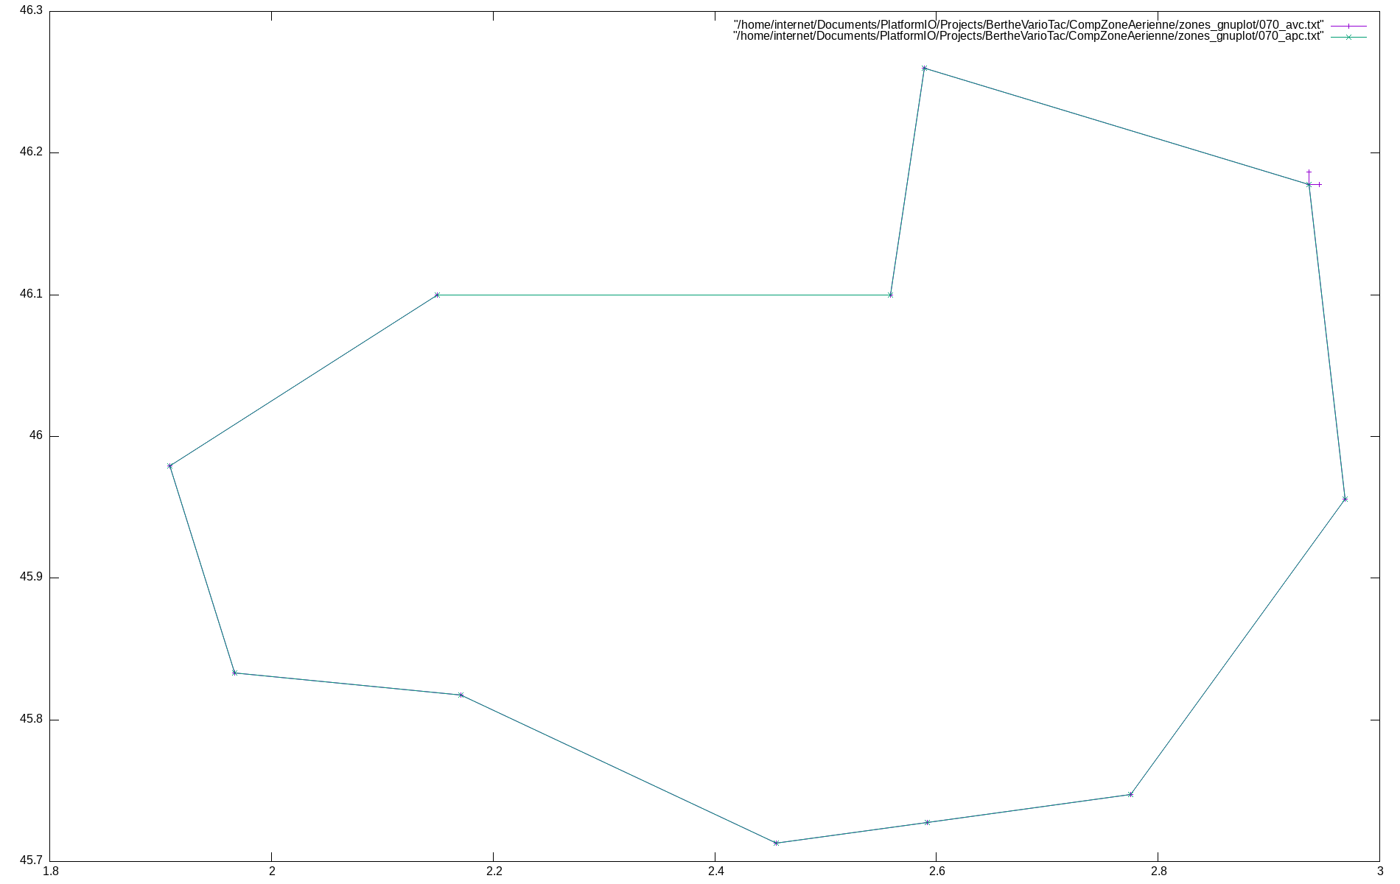
CompZoneAerienne/zones_gnuplot/070.png
