gitberthe/BertheVarioTac/CompZoneAerienne/zones_gnuplot/071.png

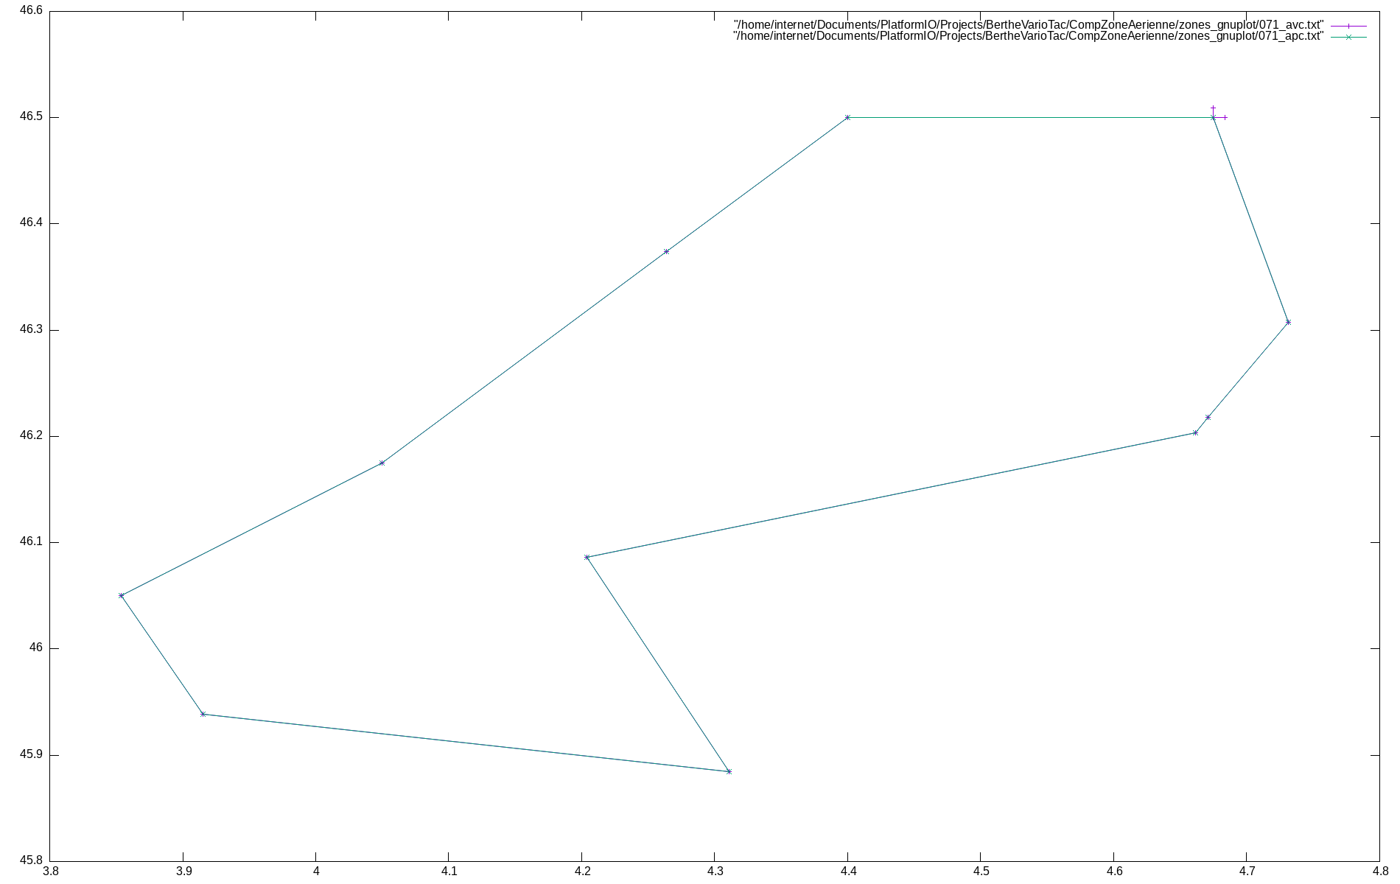
CompZoneAerienne/zones_gnuplot/071.png
