gitberthe/BertheVarioTac/CompZoneAerienne/zones_gnuplot/072.png

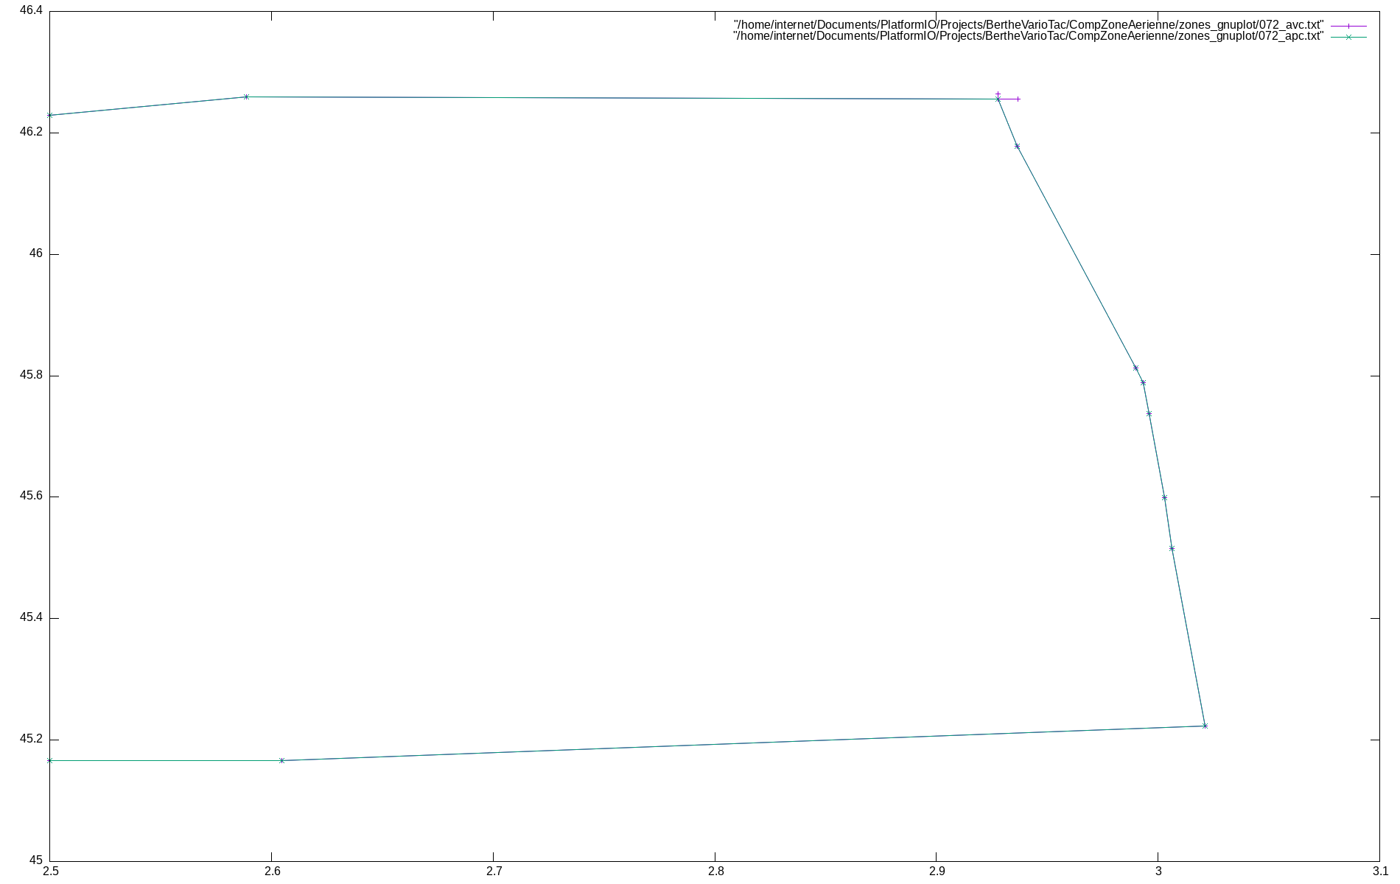
CompZoneAerienne/zones_gnuplot/072.png
