gitberthe/BertheVarioTac/CompZoneAerienne/zones_gnuplot/074.png

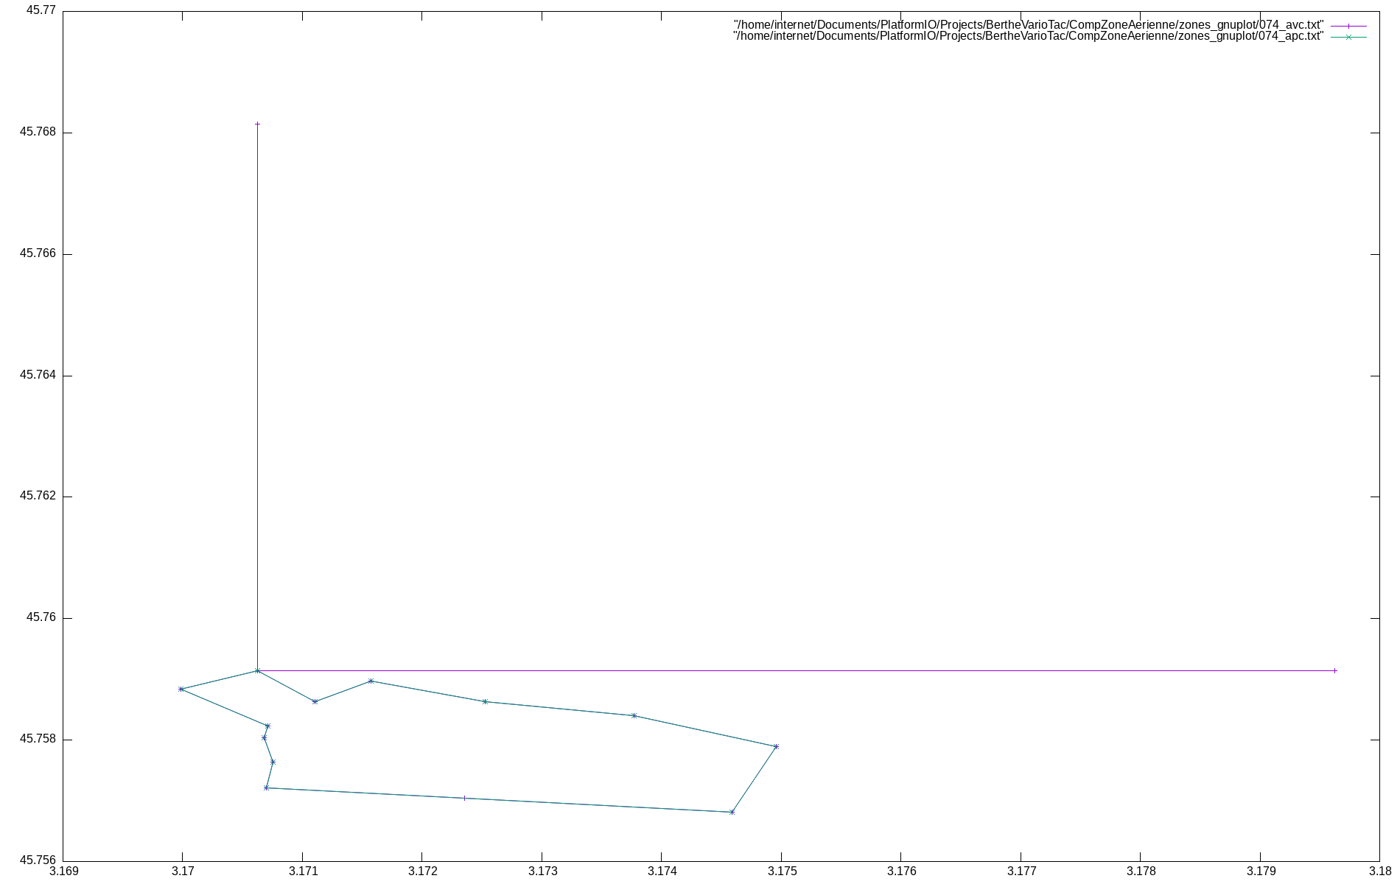
CompZoneAerienne/zones_gnuplot/074.png
