gitberthe/BertheVarioTac/CompZoneAerienne/zones_gnuplot/075.png

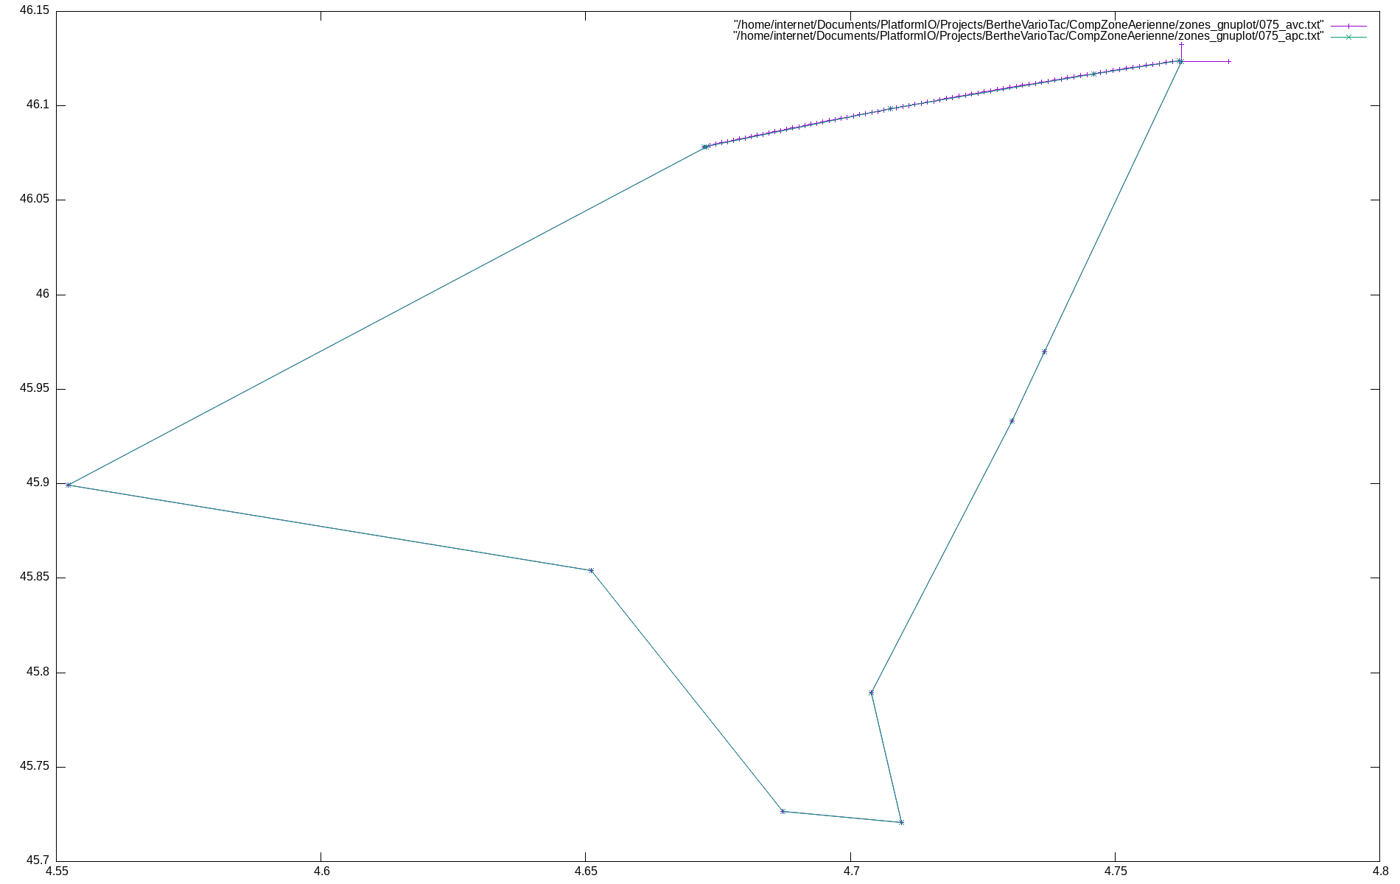
CompZoneAerienne/zones_gnuplot/075.png
