gitberthe/BertheVarioTac/CompZoneAerienne/zones_gnuplot/076.png

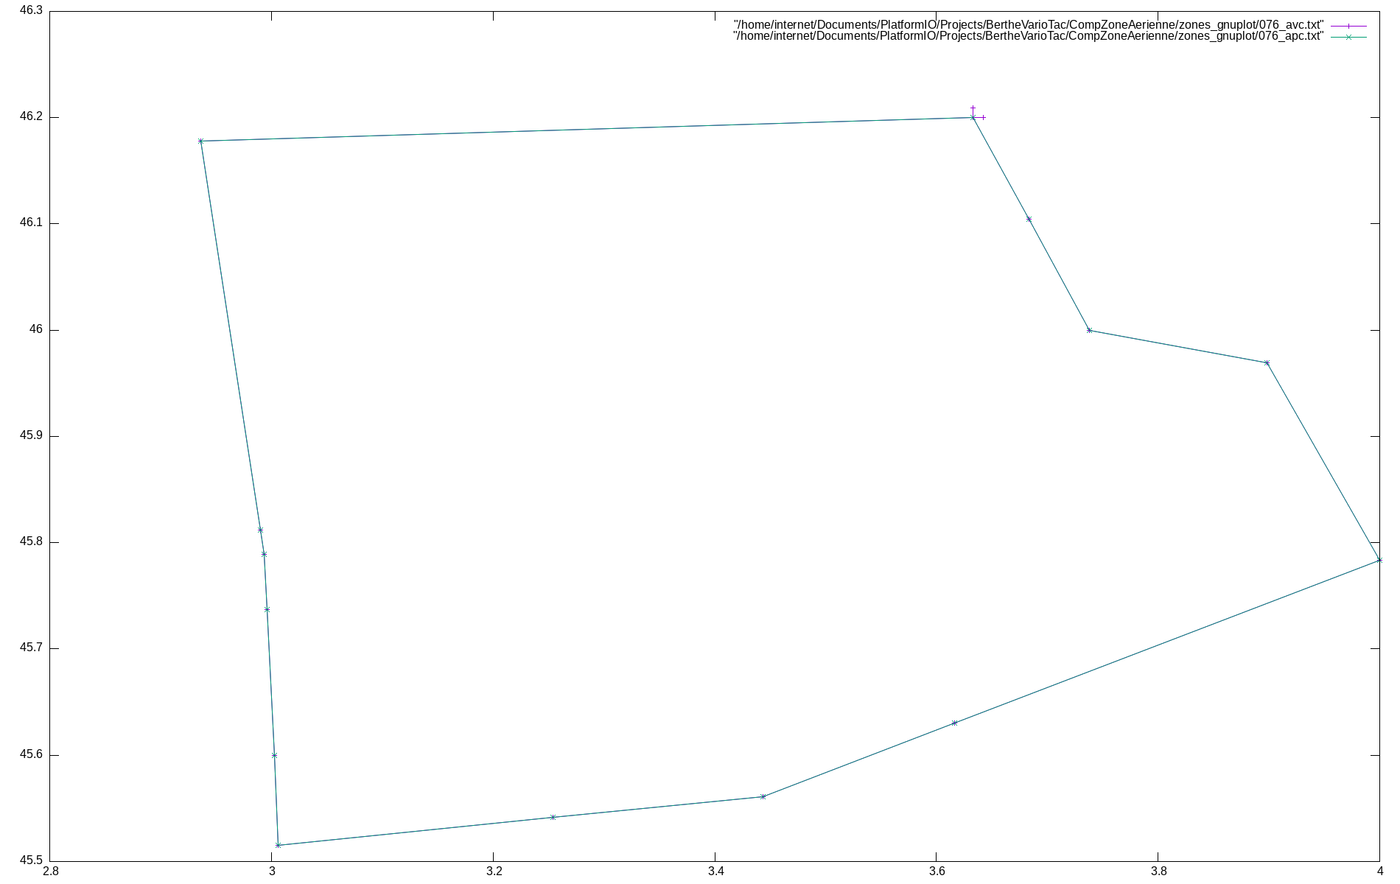
CompZoneAerienne/zones_gnuplot/076.png
