gitberthe/BertheVarioTac/CompZoneAerienne/zones_gnuplot/078.png

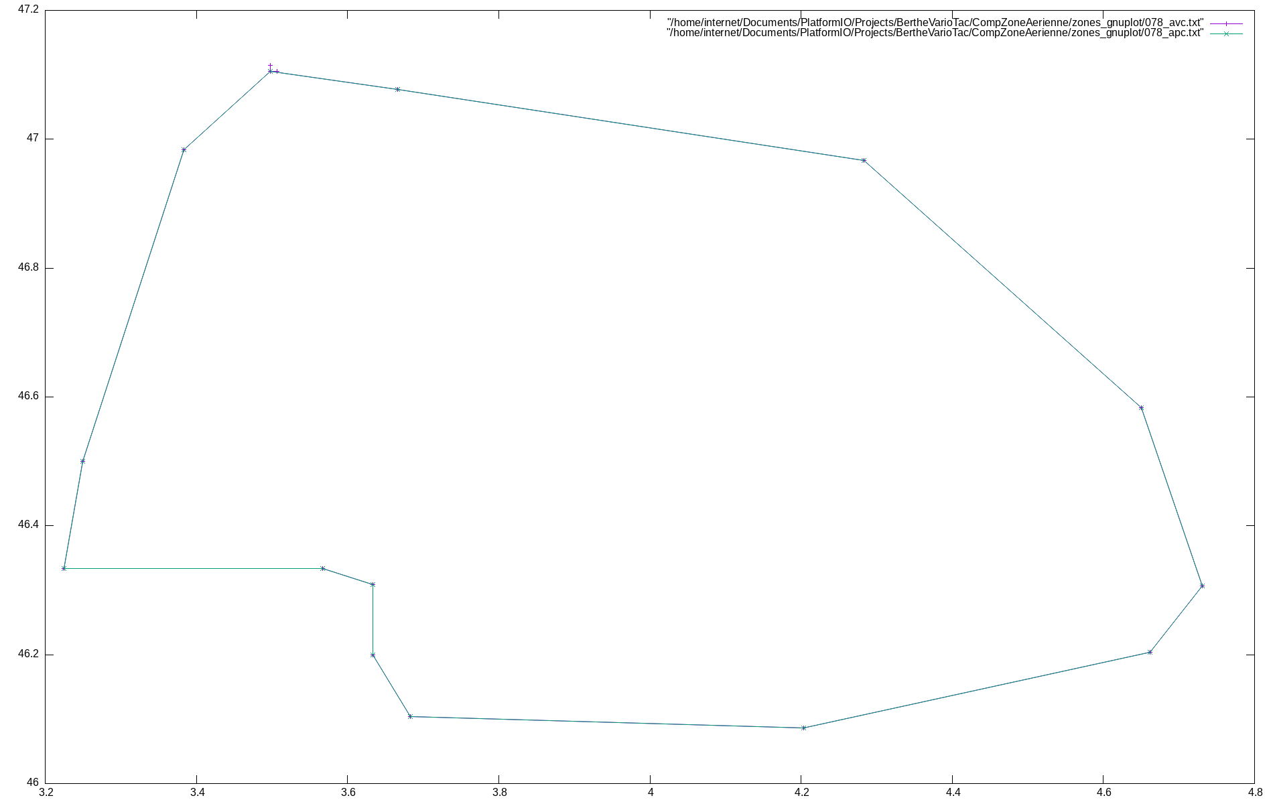
CompZoneAerienne/zones_gnuplot/078.png
