gitberthe/BertheVarioTac/CompZoneAerienne/zones_gnuplot/079.png

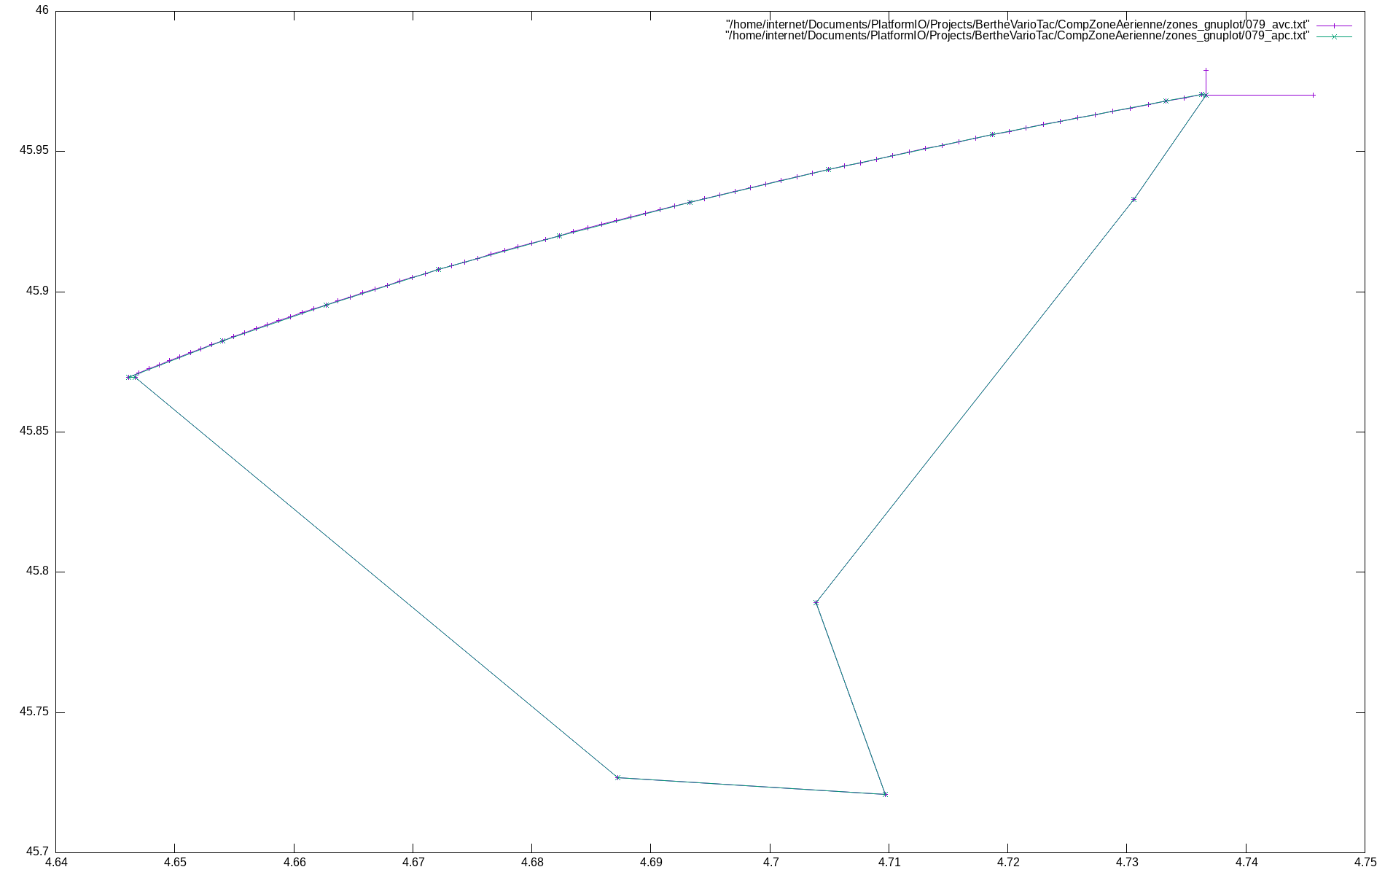
CompZoneAerienne/zones_gnuplot/079.png
