gitberthe/BertheVarioTac/CompZoneAerienne/zones_gnuplot/082.png

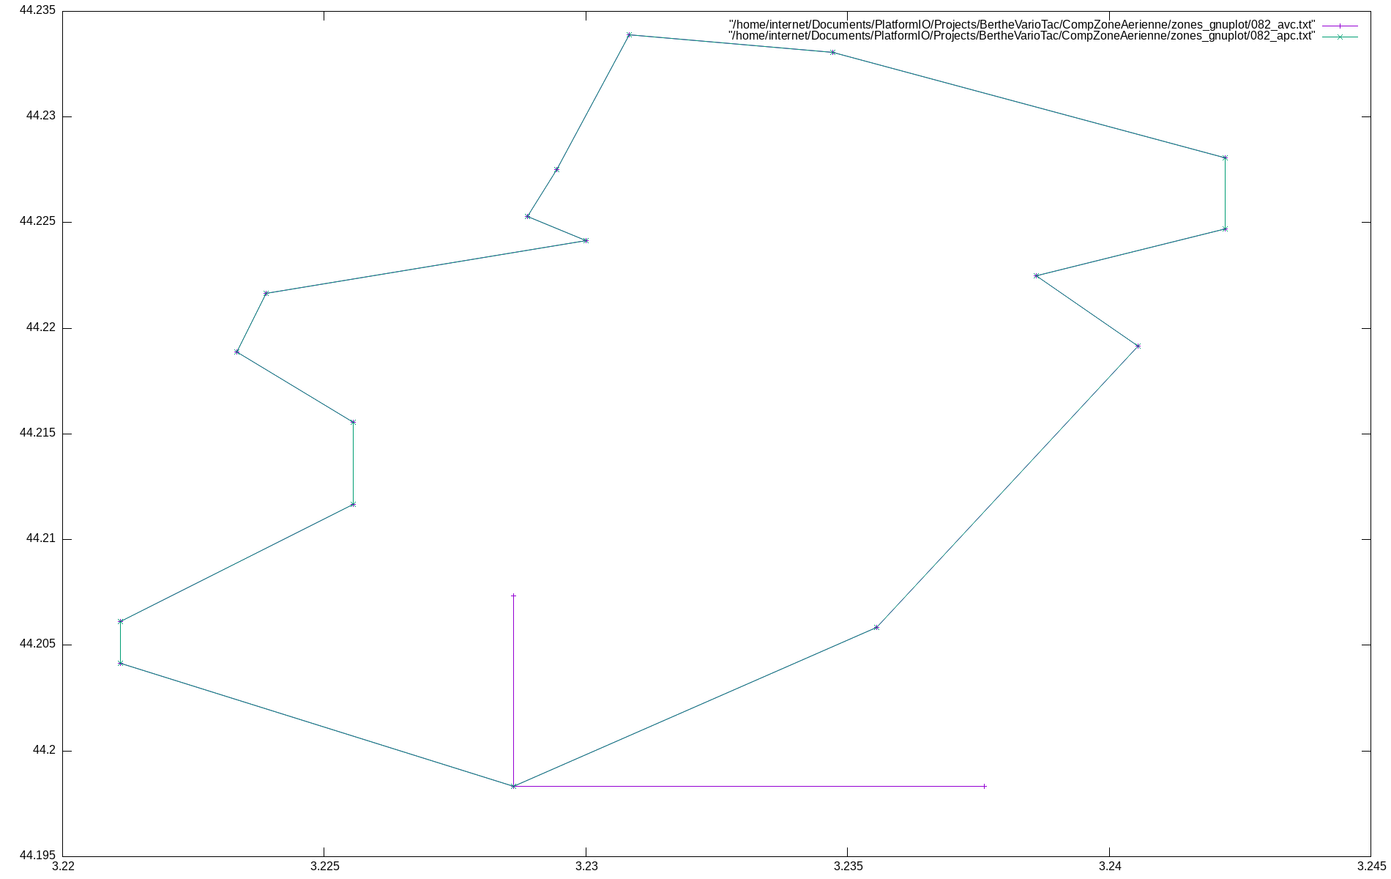
CompZoneAerienne/zones_gnuplot/082.png
