gitberthe/BertheVarioTac/CompZoneAerienne/zones_gnuplot/083.png

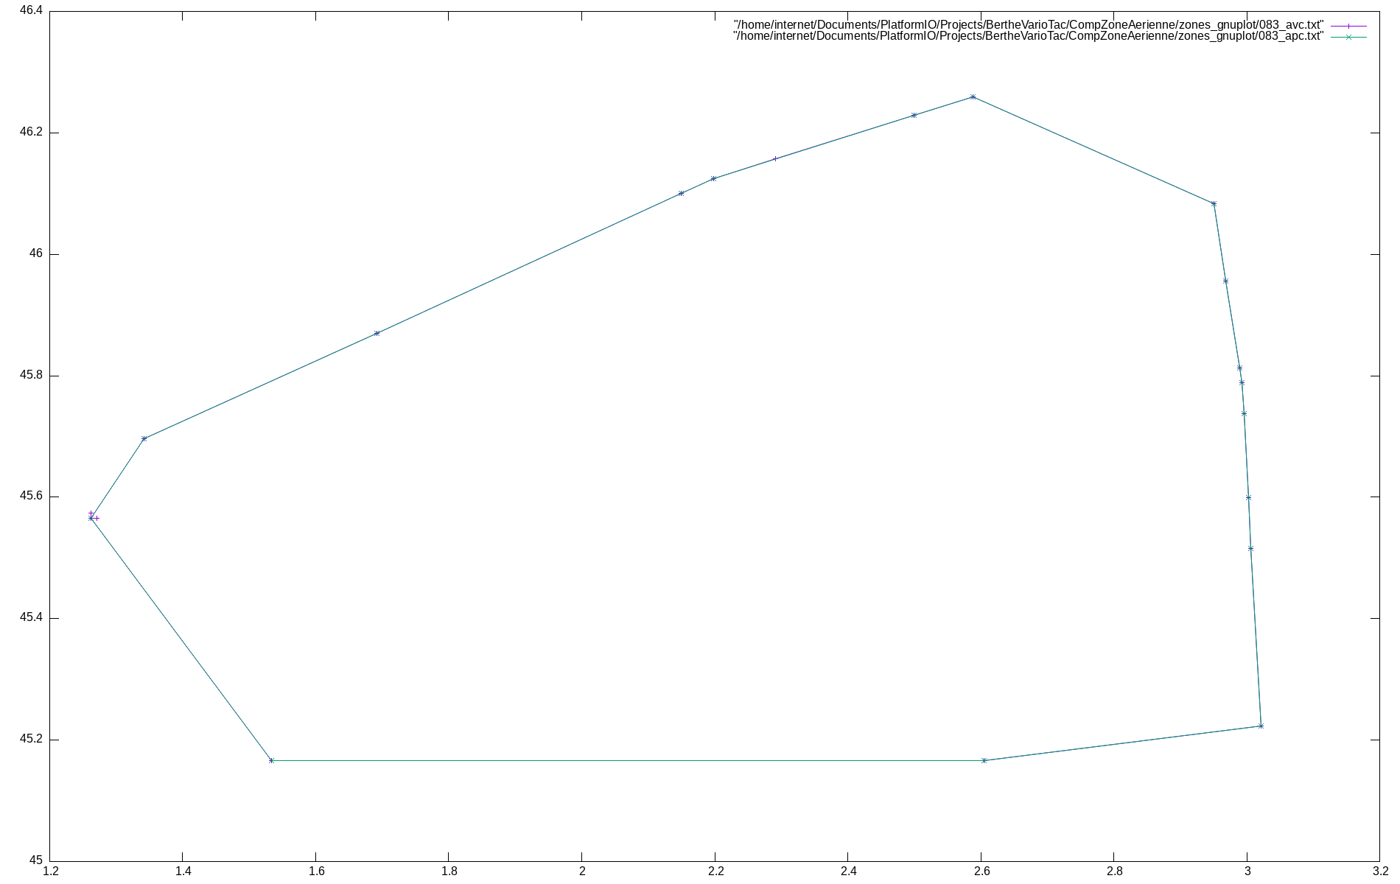
CompZoneAerienne/zones_gnuplot/083.png
