gitberthe/BertheVarioTac/CompZoneAerienne/zones_gnuplot/084.png

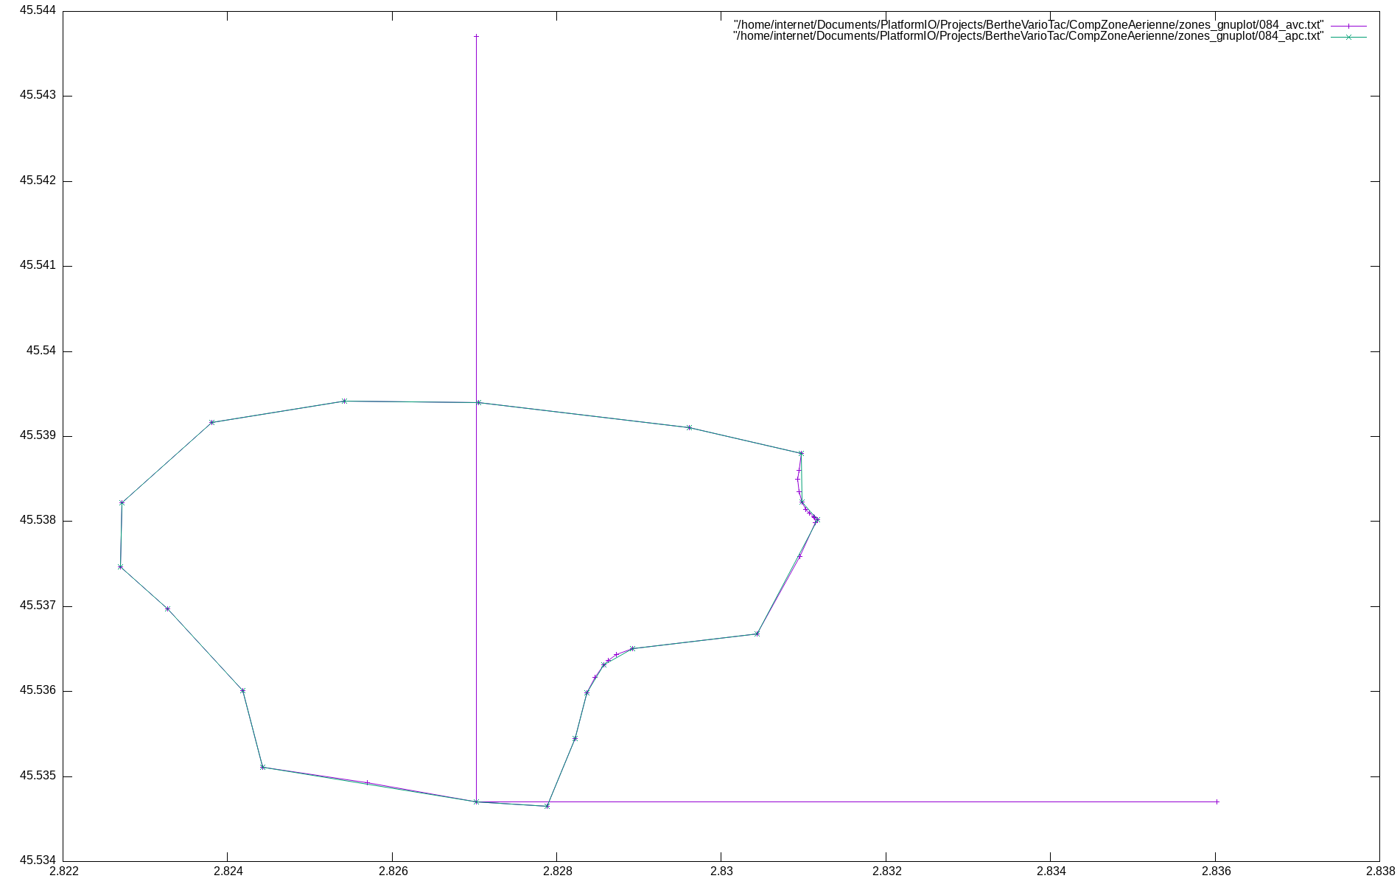
CompZoneAerienne/zones_gnuplot/084.png
