gitberthe/BertheVarioTac/CompZoneAerienne/zones_gnuplot/085.png

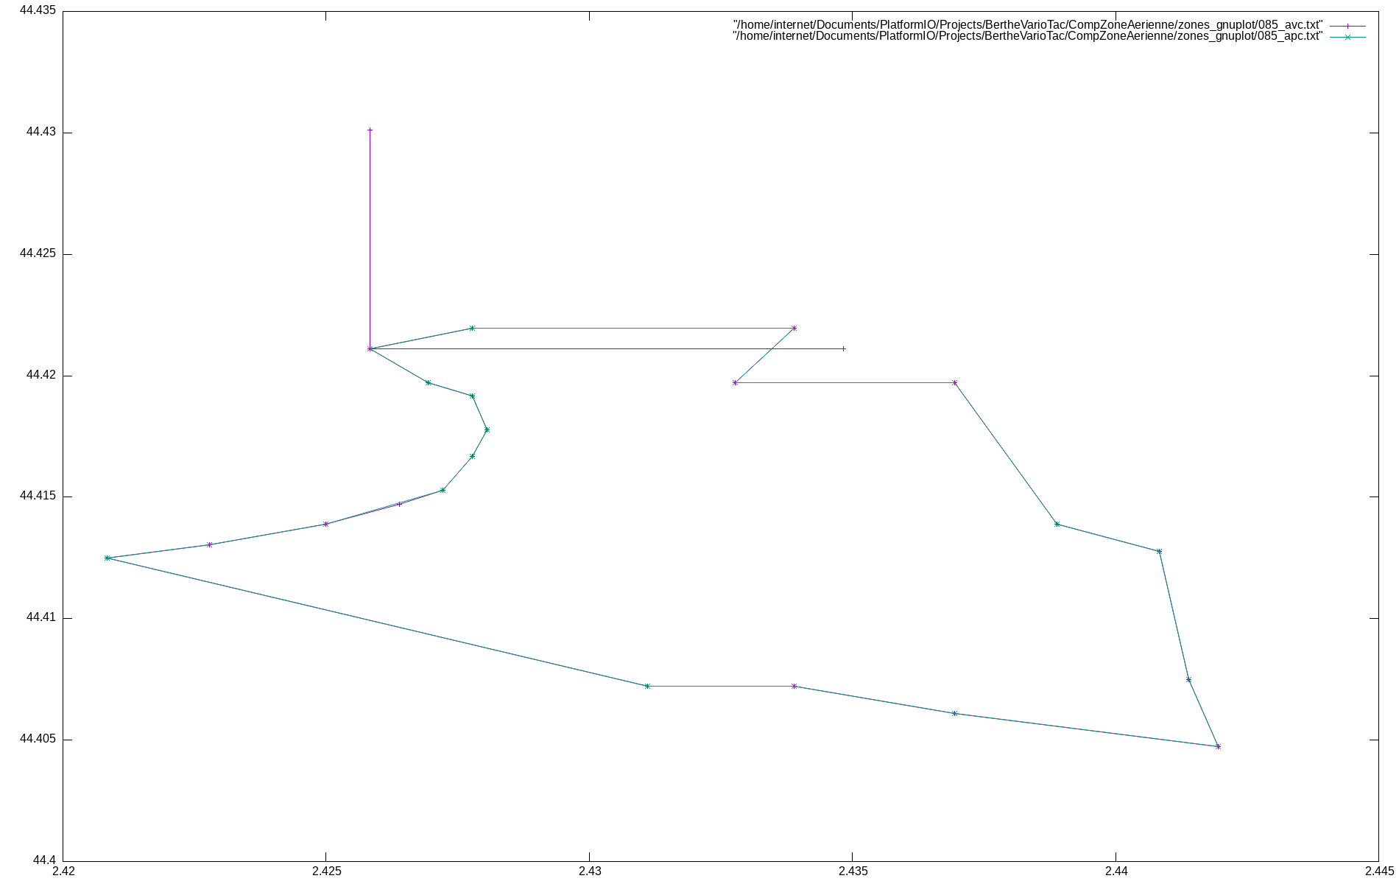
CompZoneAerienne/zones_gnuplot/085.png
