gitberthe/BertheVarioTac/CompZoneAerienne/zones_gnuplot/086.png

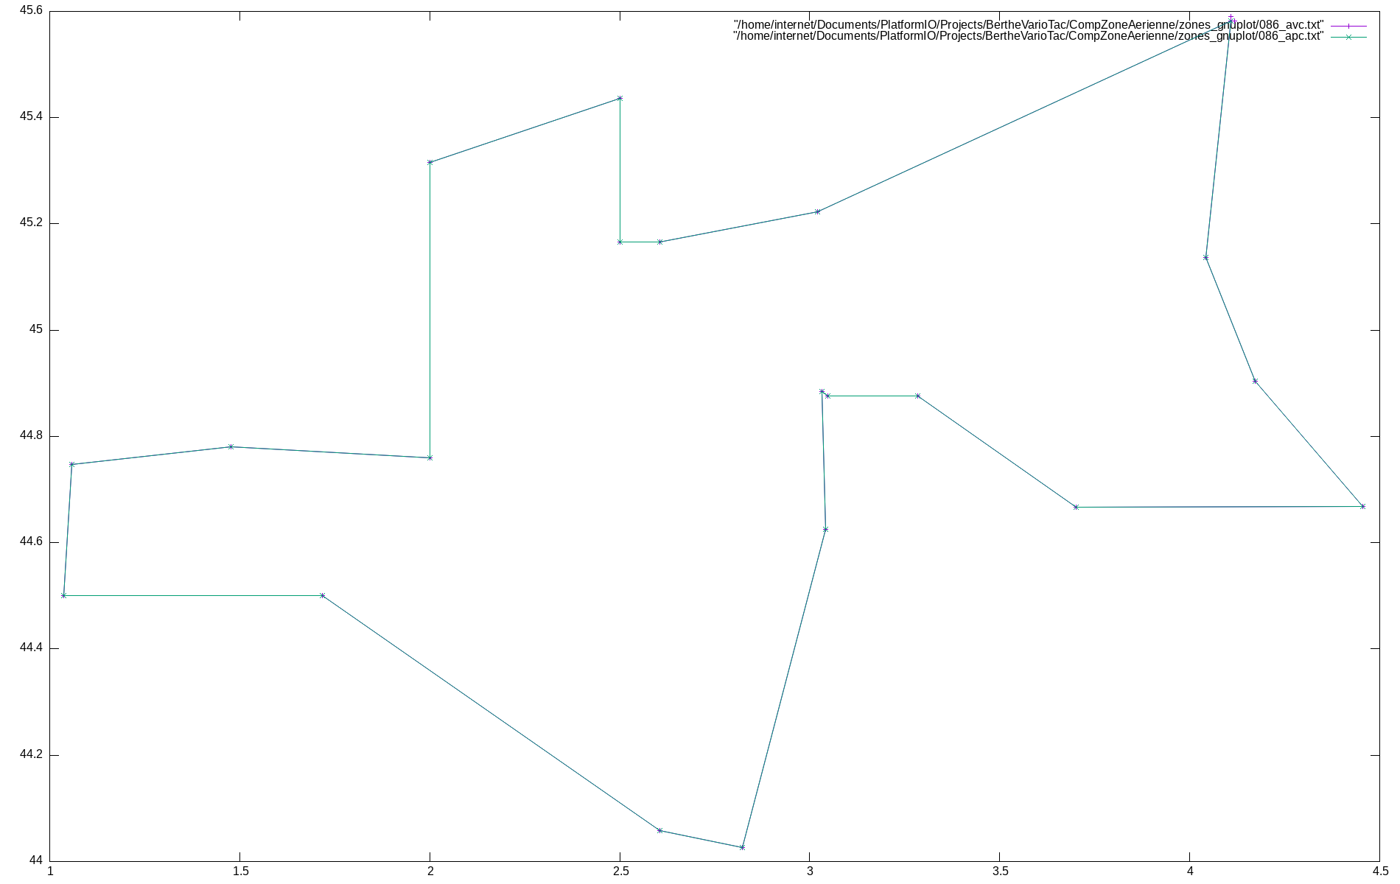
CompZoneAerienne/zones_gnuplot/086.png
