gitberthe/BertheVarioTac/CompZoneAerienne/zones_gnuplot/087.png

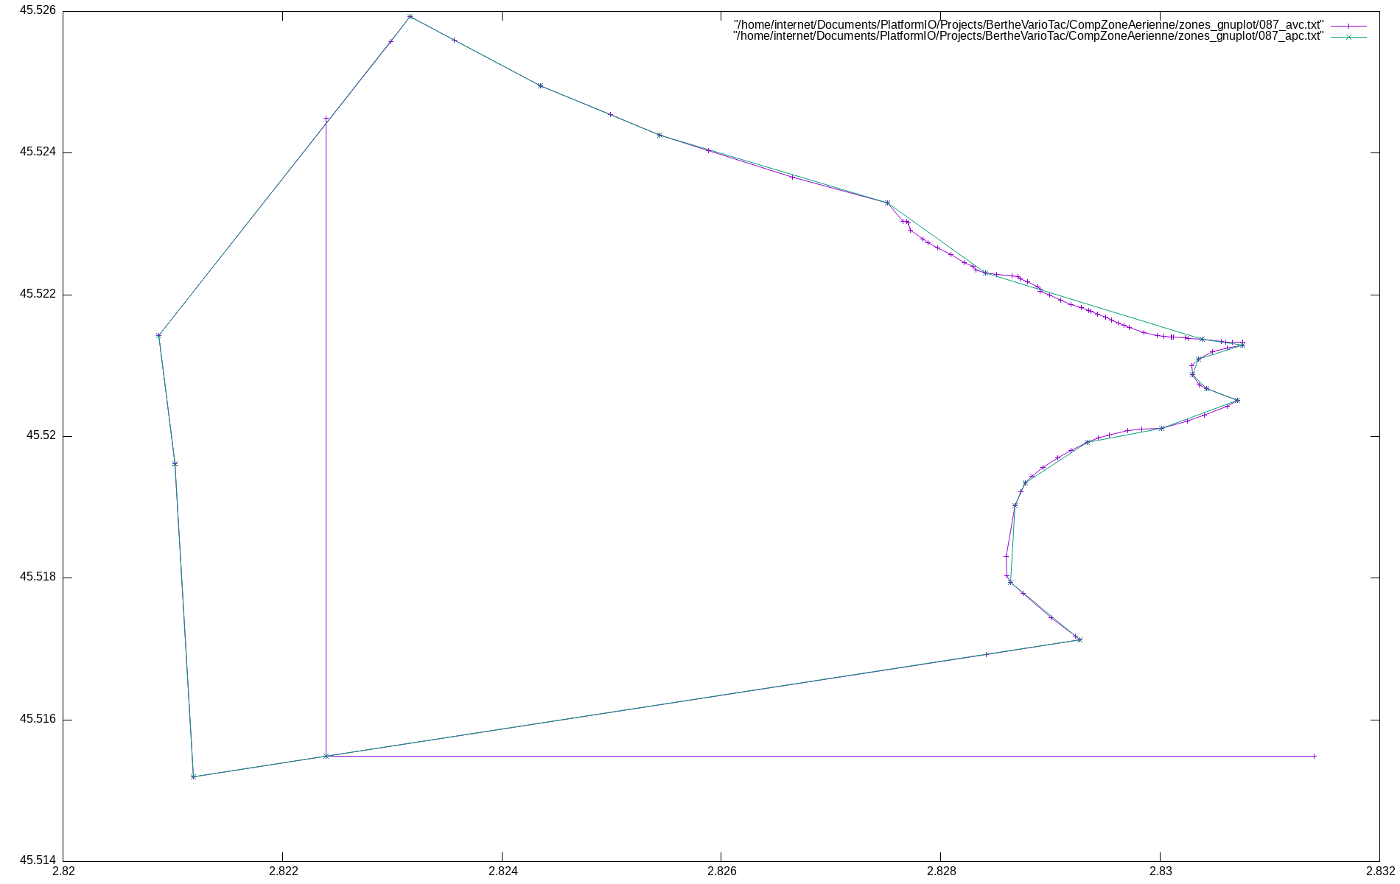
CompZoneAerienne/zones_gnuplot/087.png
