gitberthe/BertheVarioTac/CompZoneAerienne/zones_gnuplot/088.png

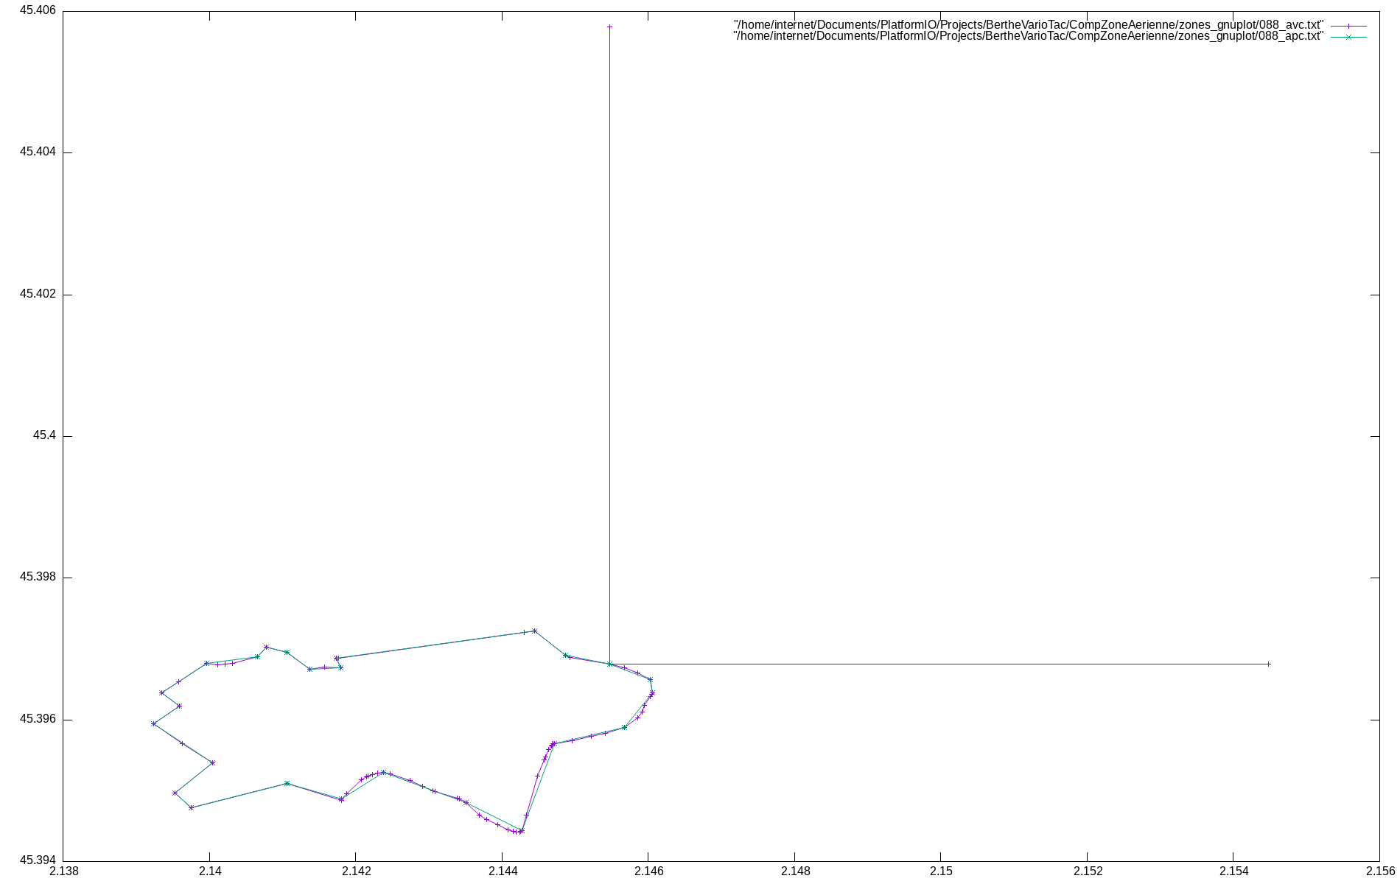
CompZoneAerienne/zones_gnuplot/088.png
