gitberthe/BertheVarioTac/CompZoneAerienne/zones_gnuplot/089.png

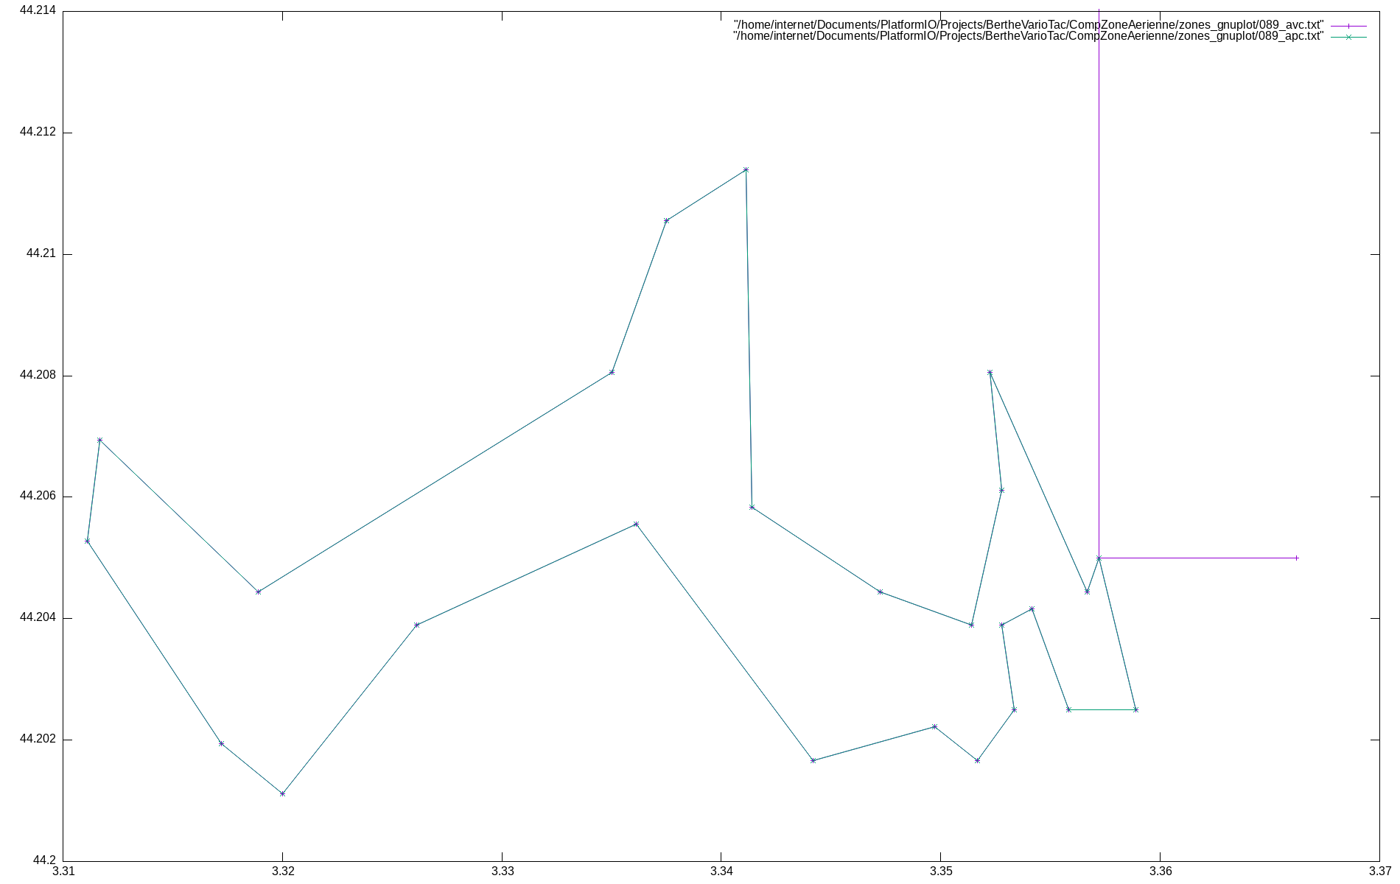
CompZoneAerienne/zones_gnuplot/089.png
