gitberthe/BertheVarioTac/CompZoneAerienne/zones_gnuplot/090.png

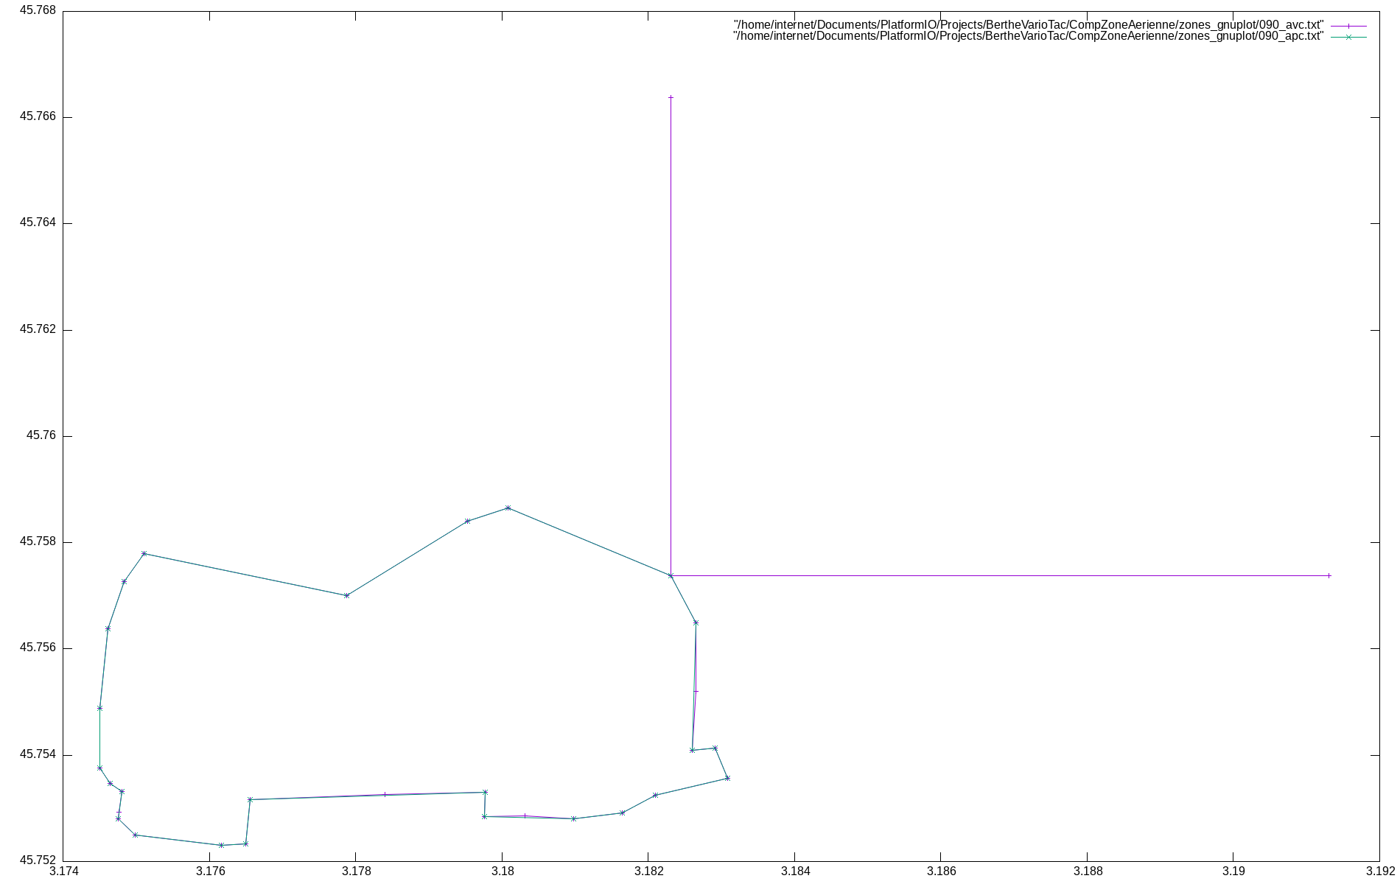
CompZoneAerienne/zones_gnuplot/090.png
