gitberthe/BertheVarioTac/CompZoneAerienne/zones_gnuplot/091.png

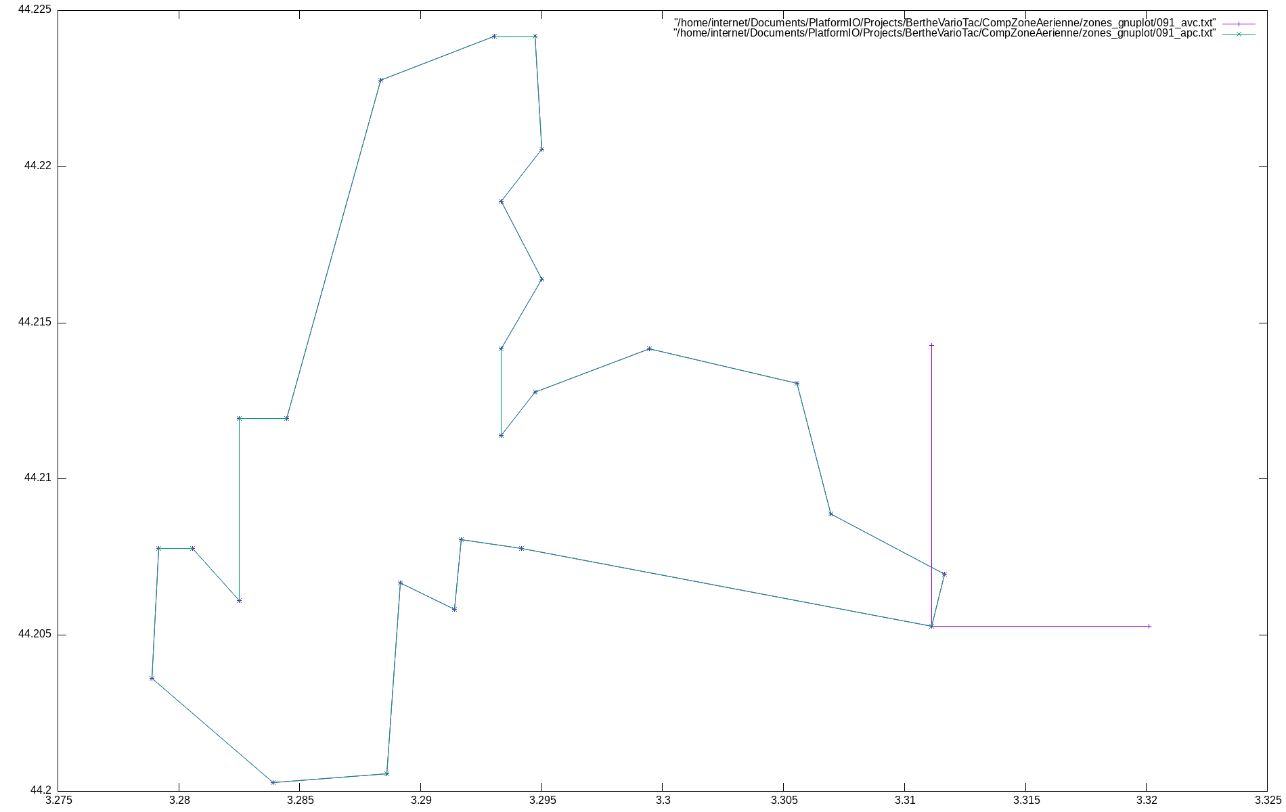
CompZoneAerienne/zones_gnuplot/091.png
