gitberthe/BertheVarioTac/CompZoneAerienne/zones_gnuplot/092.png

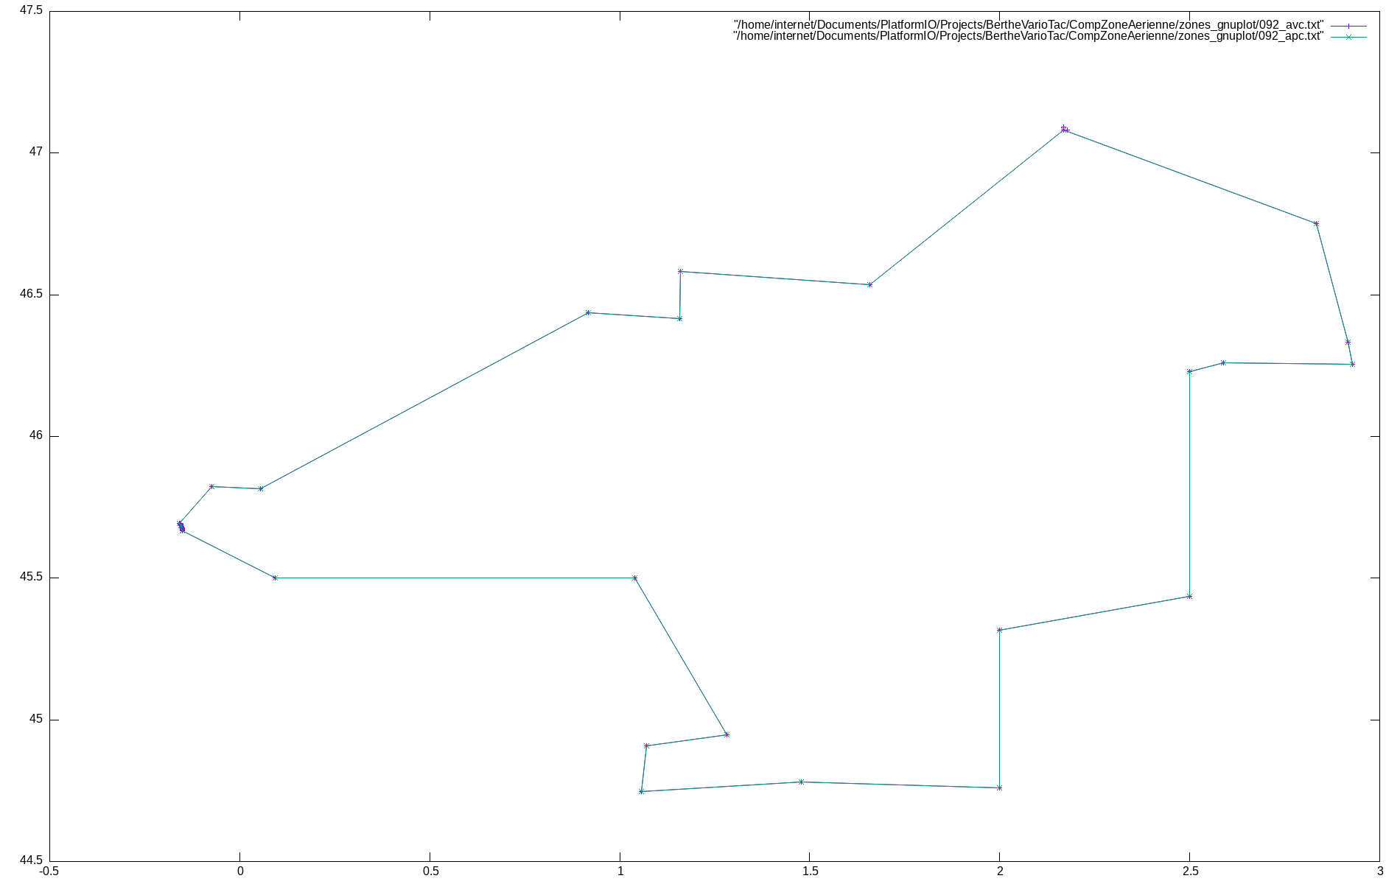
CompZoneAerienne/zones_gnuplot/092.png
