gitberthe/BertheVarioTac/CompZoneAerienne/zones_gnuplot/093.png

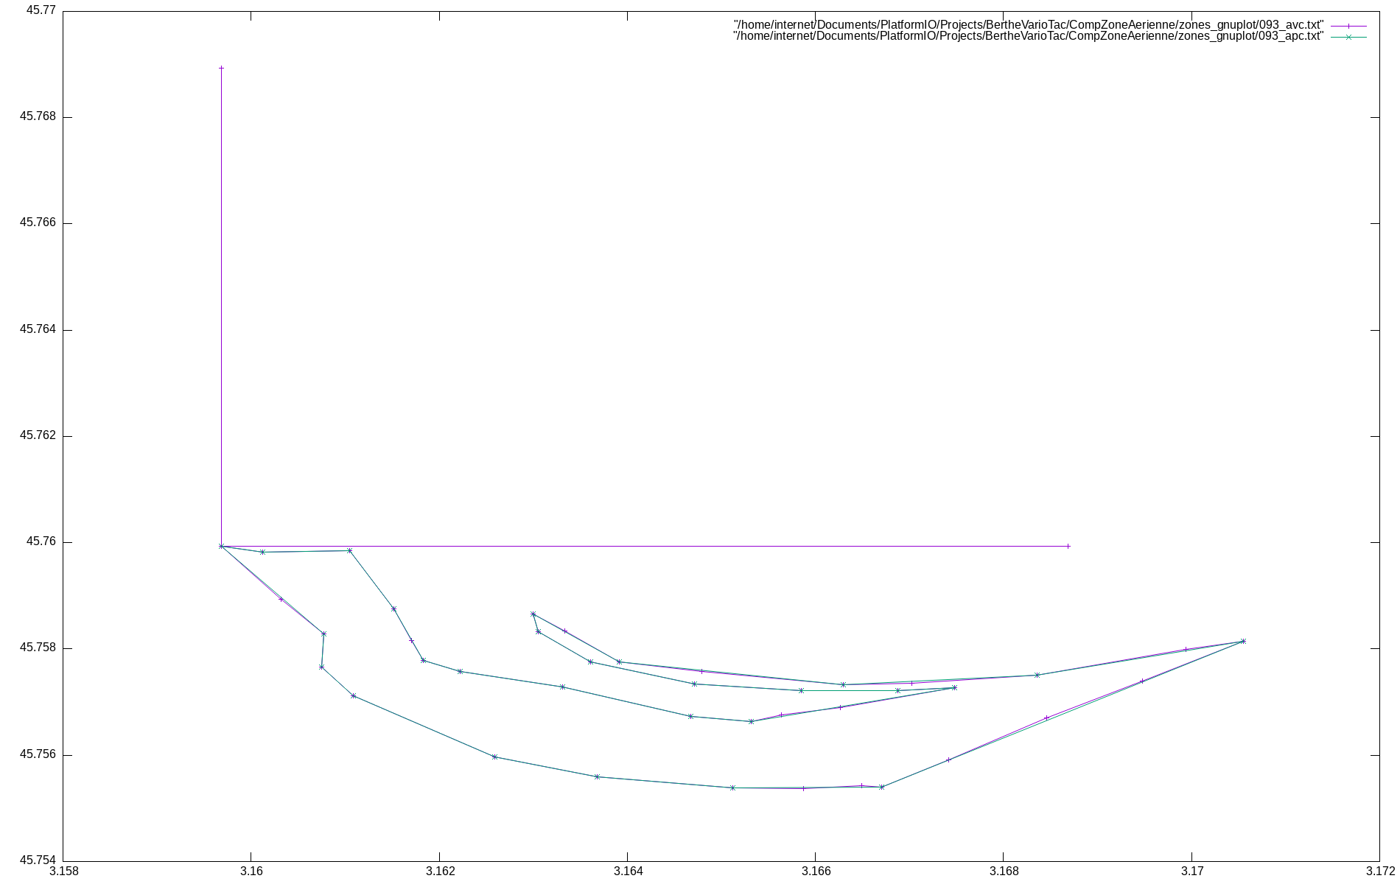
CompZoneAerienne/zones_gnuplot/093.png
