gitberthe/BertheVarioTac/CompZoneAerienne/zones_gnuplot/094.png

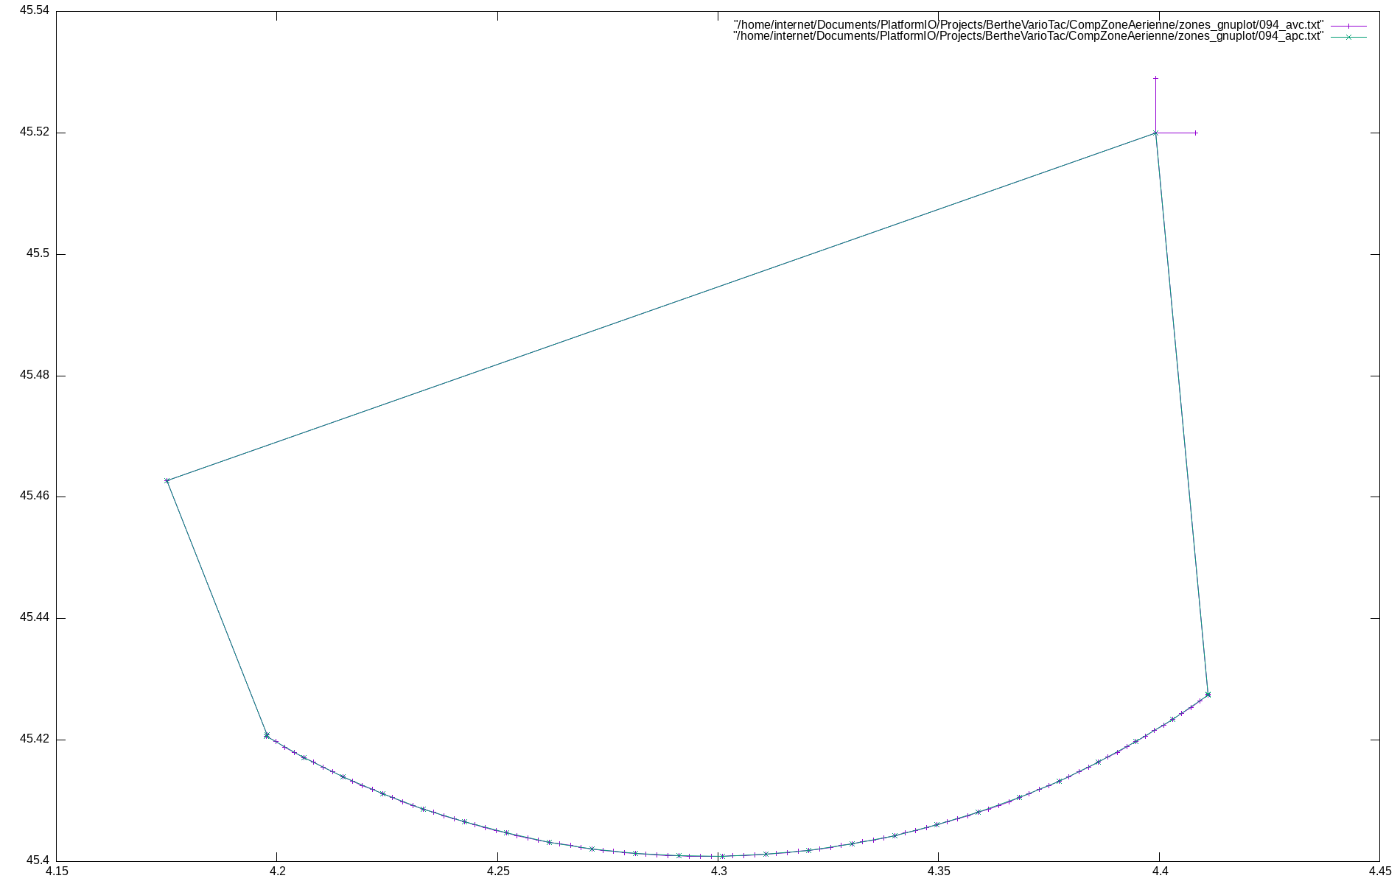
CompZoneAerienne/zones_gnuplot/094.png
