gitberthe/BertheVarioTac/CompZoneAerienne/zones_gnuplot/095.png

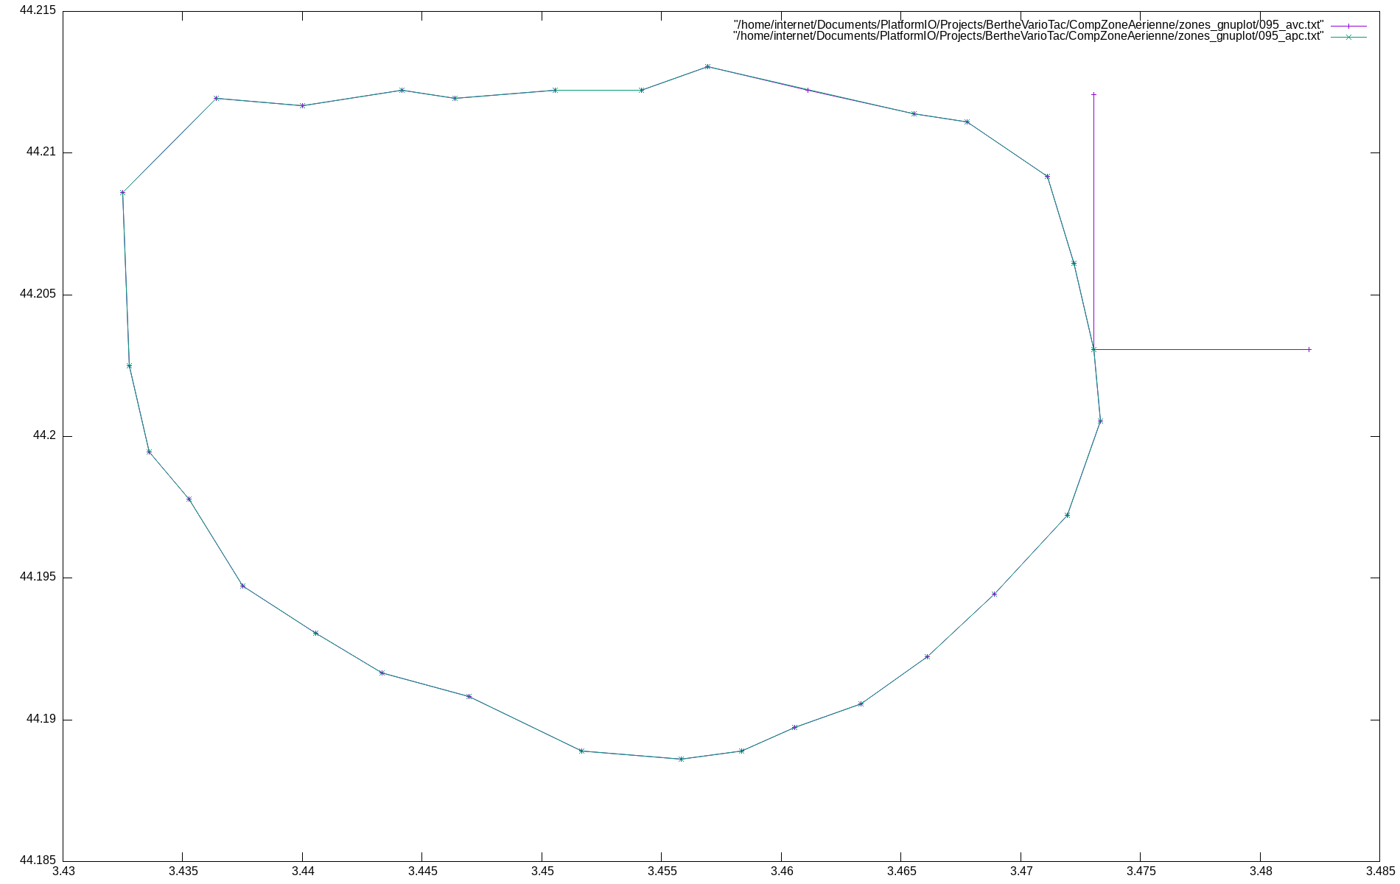
CompZoneAerienne/zones_gnuplot/095.png
