gitberthe/BertheVarioTac/CompZoneAerienne/zones_gnuplot/099.png

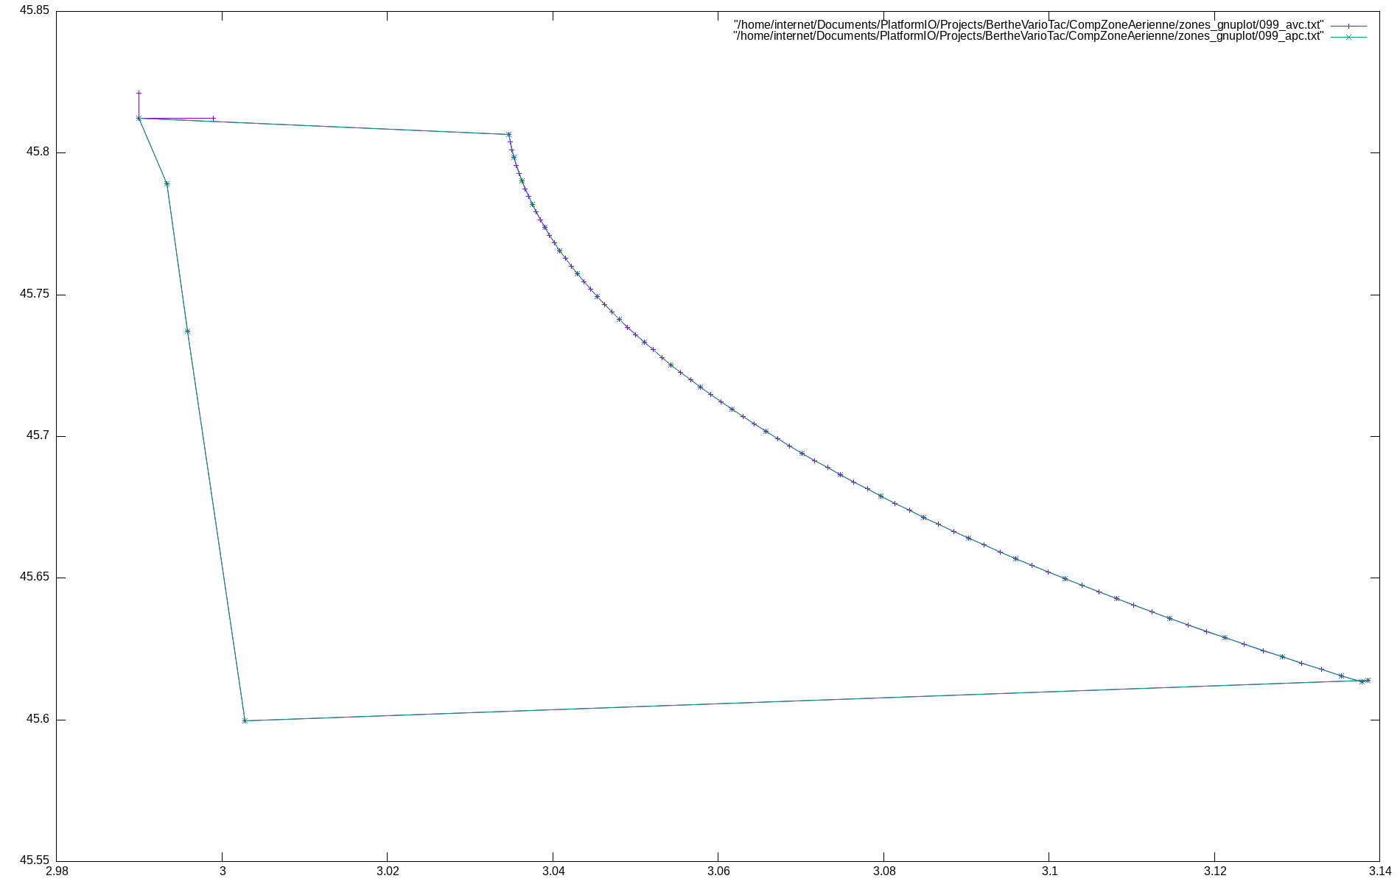
CompZoneAerienne/zones_gnuplot/099.png
