gitberthe/BertheVarioTac/CompZoneAerienne/zones_gnuplot/100.png

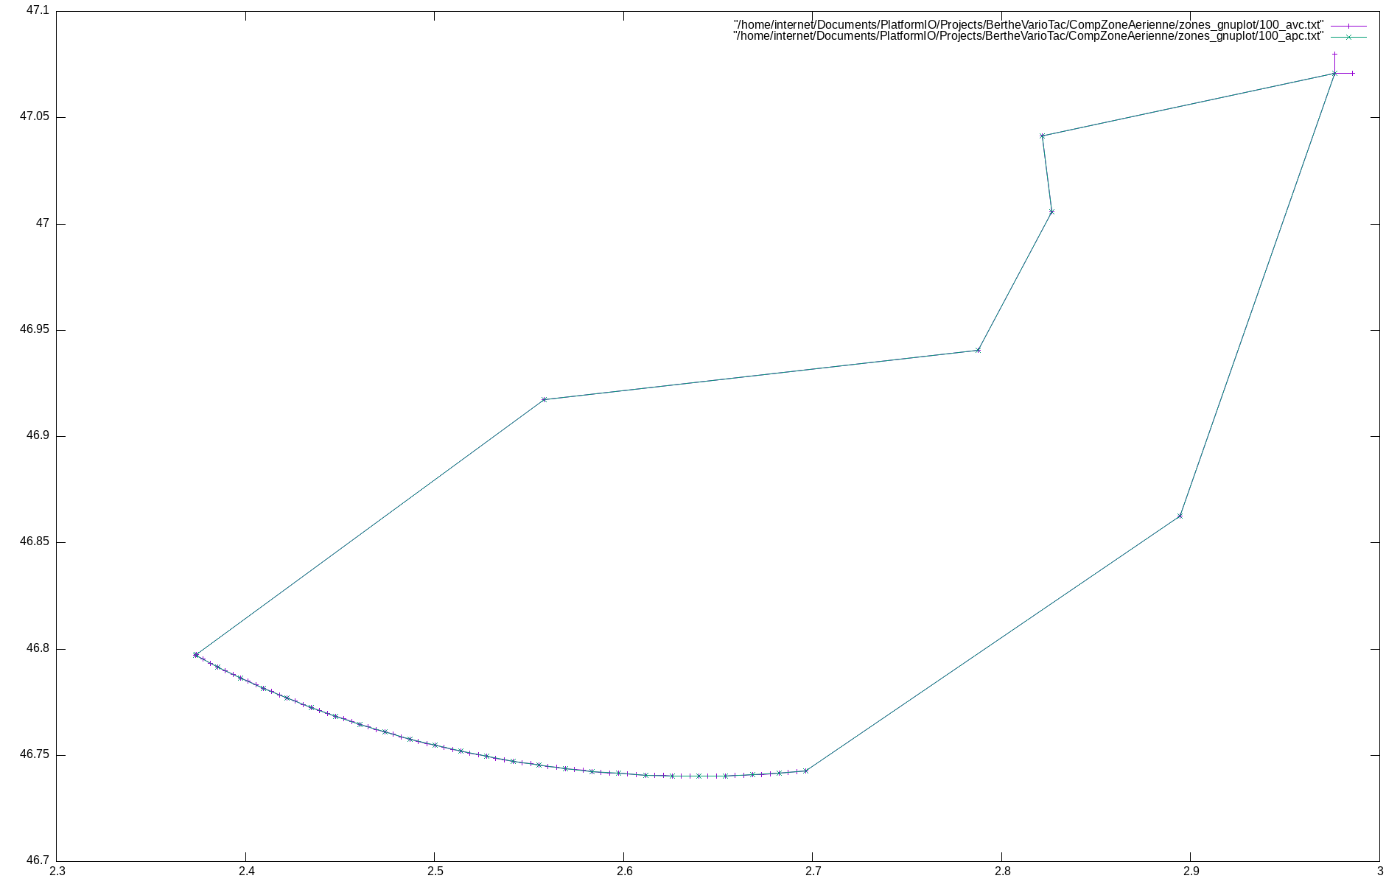
CompZoneAerienne/zones_gnuplot/100.png
