gitberthe/BertheVarioTac/CompZoneAerienne/zones_gnuplot/101.png

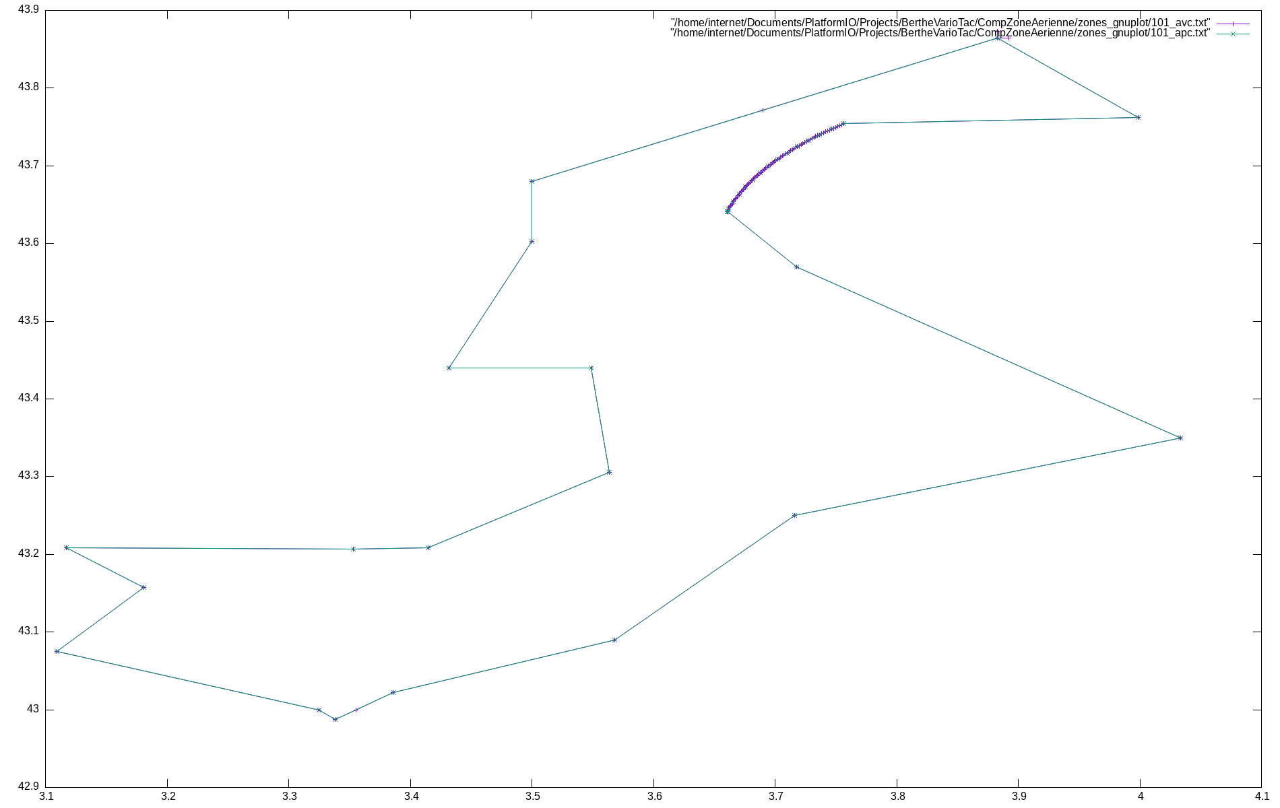
CompZoneAerienne/zones_gnuplot/101.png
