gitberthe/BertheVarioTac/CompZoneAerienne/zones_gnuplot/102.png

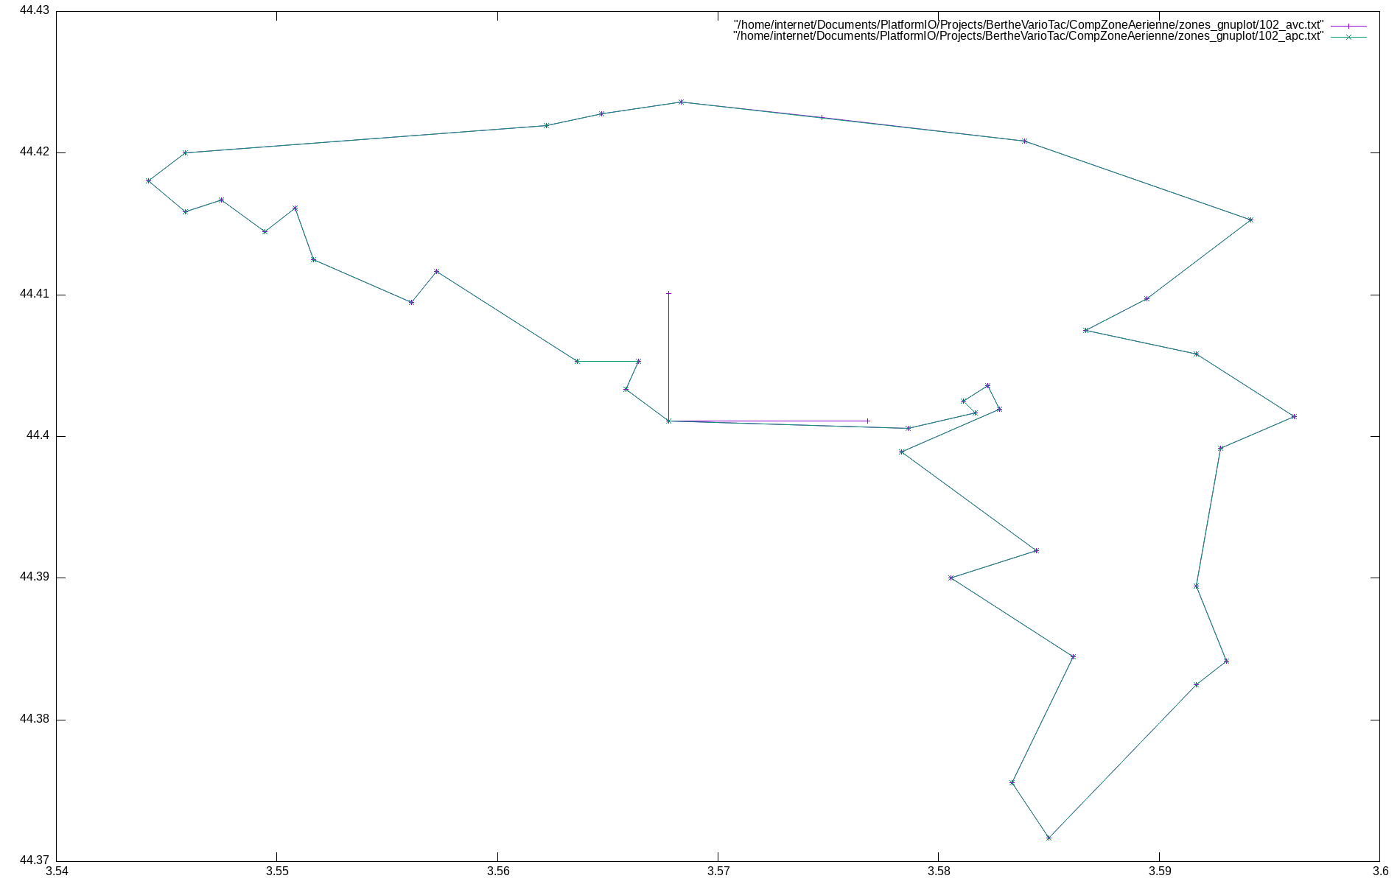
CompZoneAerienne/zones_gnuplot/102.png
