gitberthe/BertheVarioTac/CompZoneAerienne/zones_gnuplot/103.png

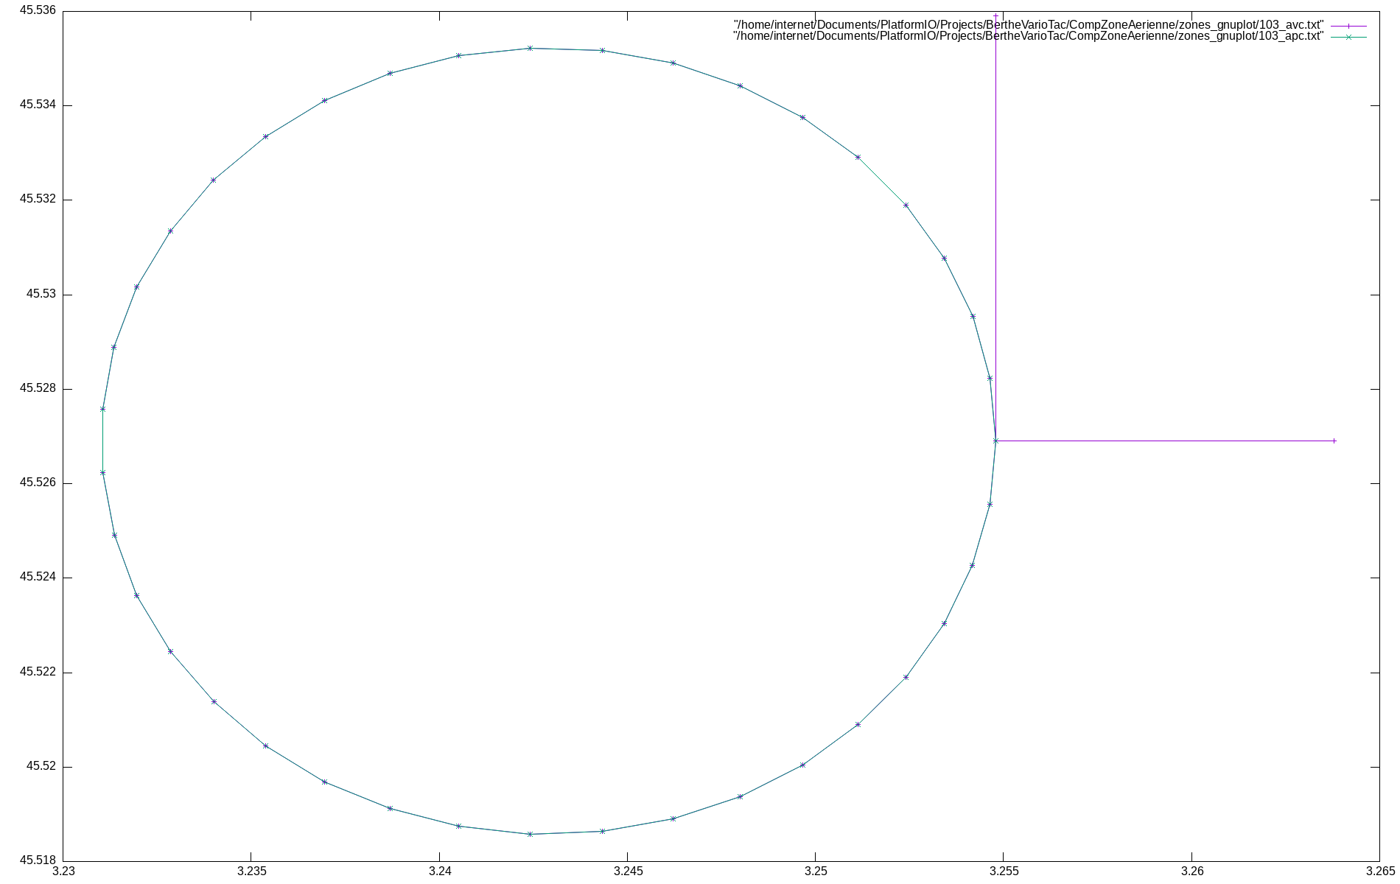
CompZoneAerienne/zones_gnuplot/103.png
