gitberthe/BertheVarioTac/CompZoneAerienne/zones_gnuplot/104.png

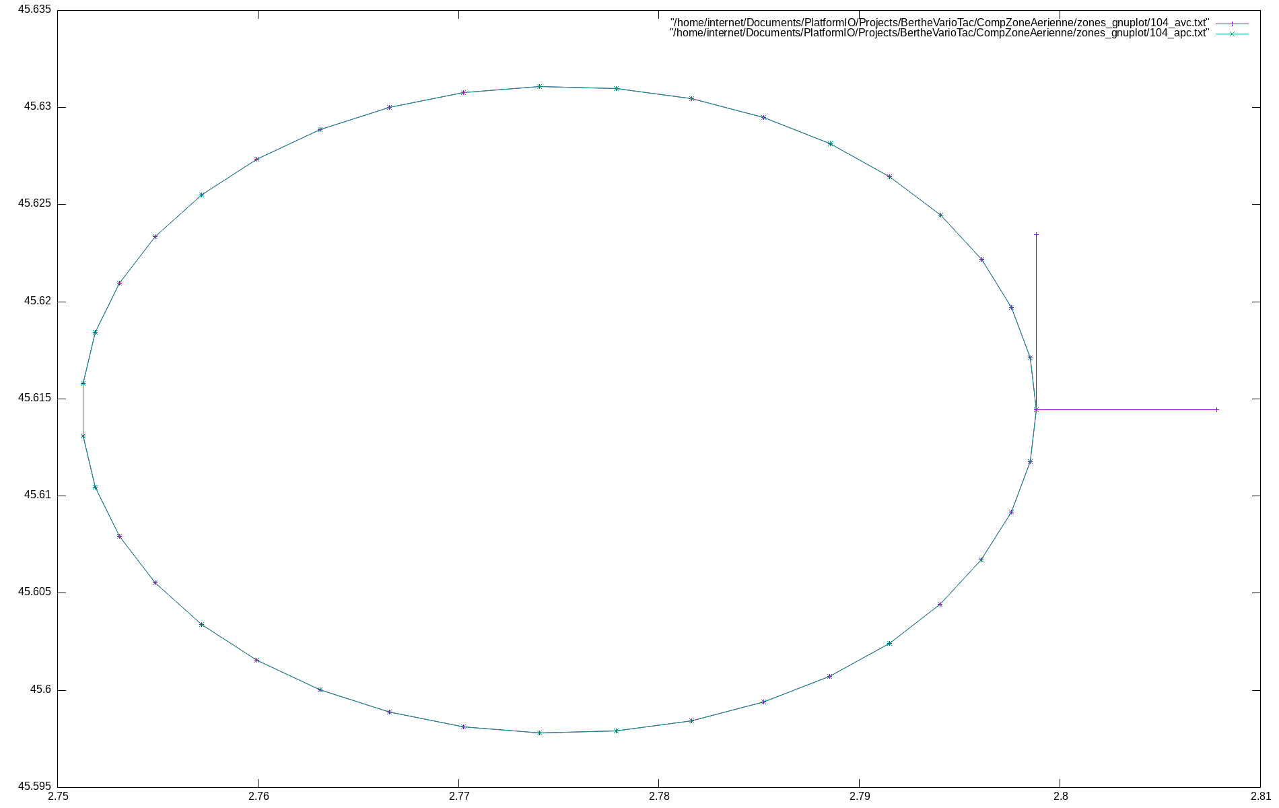
CompZoneAerienne/zones_gnuplot/104.png
