gitberthe/BertheVarioTac/CompZoneAerienne/zones_gnuplot/105.png

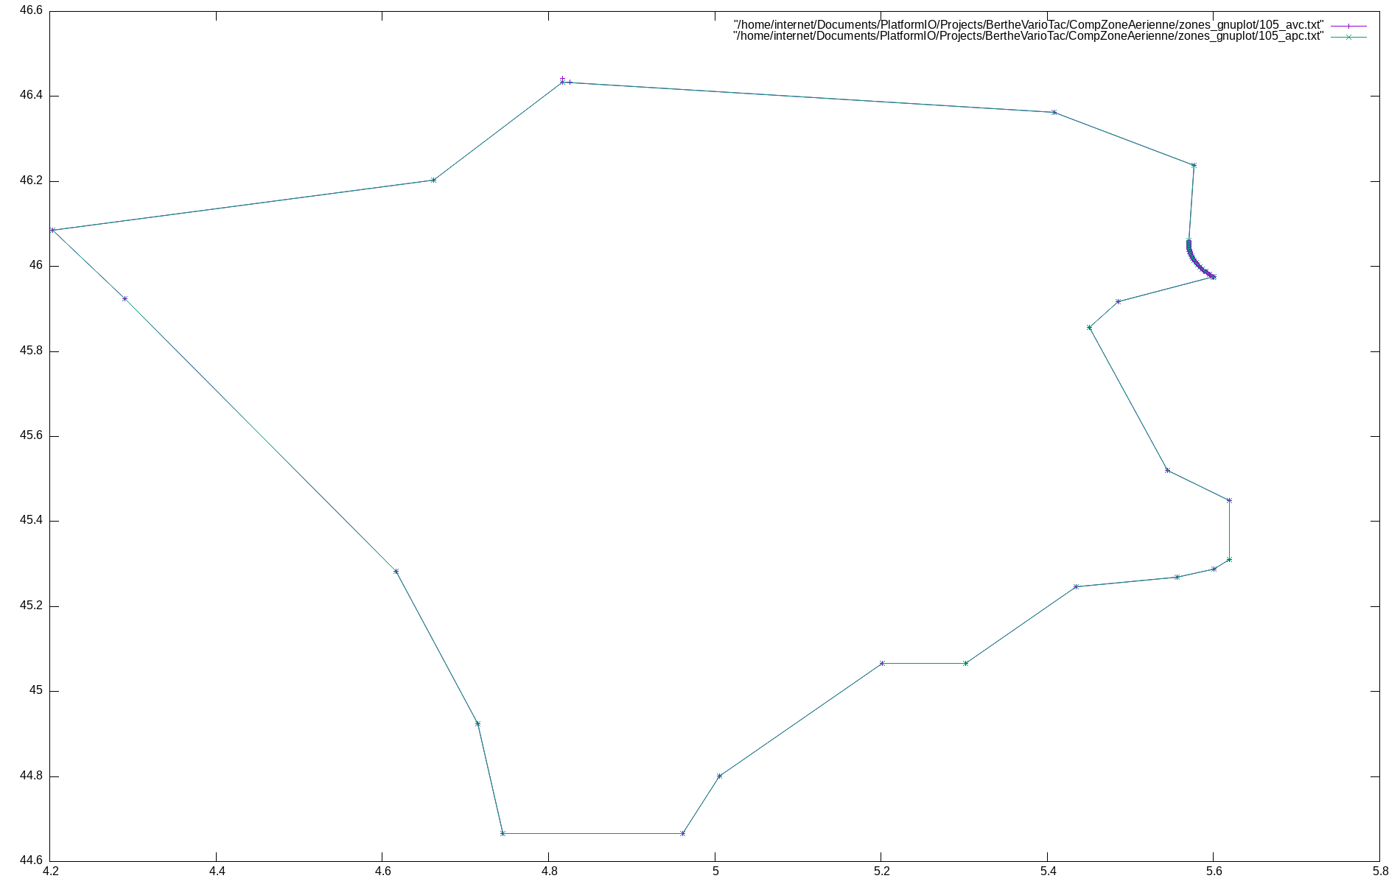
CompZoneAerienne/zones_gnuplot/105.png
