gitberthe/BertheVarioTac/CompZoneAerienne/zones_gnuplot/106.png

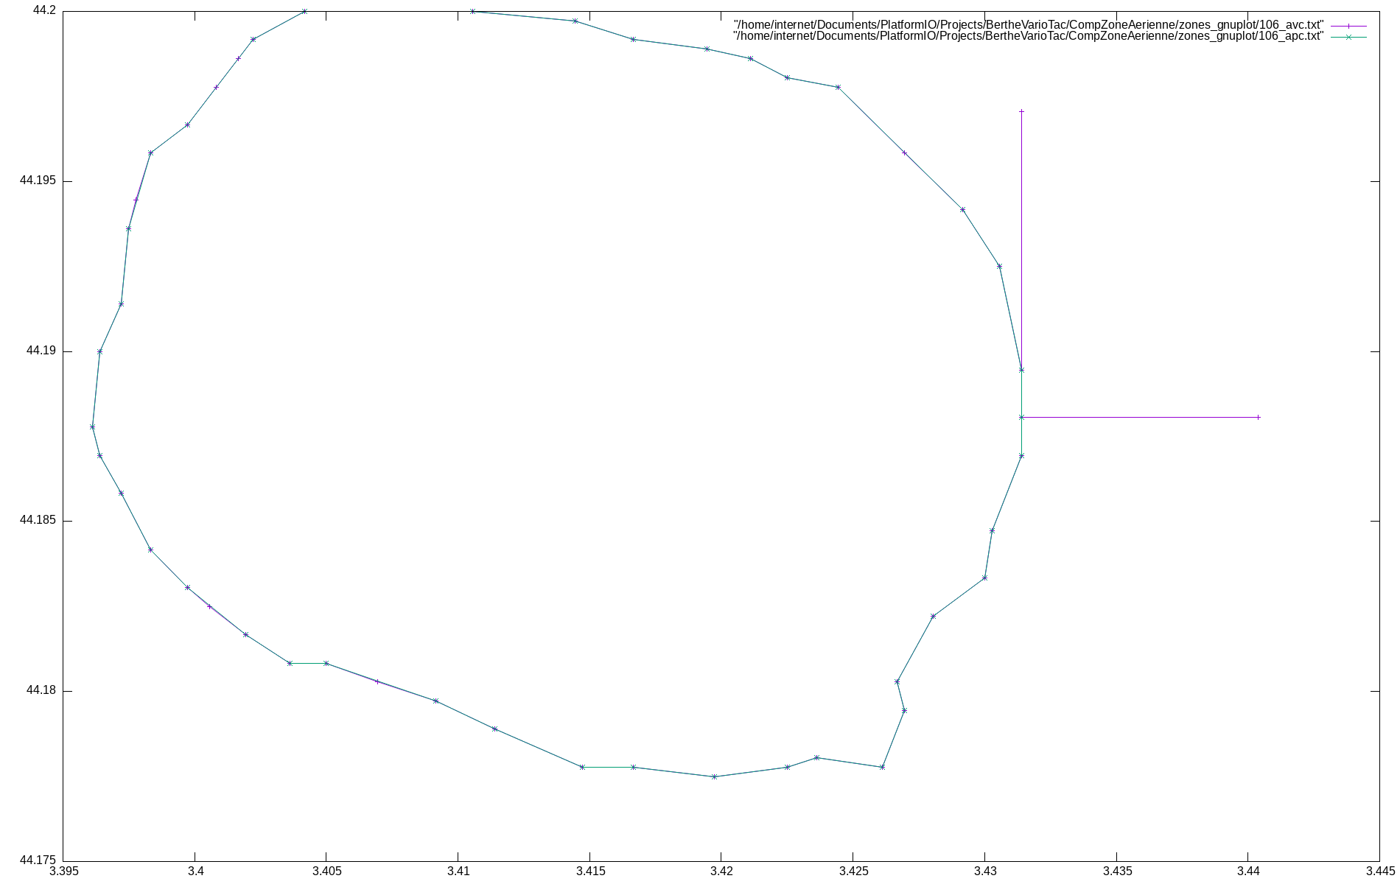
CompZoneAerienne/zones_gnuplot/106.png
