gitberthe/BertheVarioTac/CompZoneAerienne/zones_gnuplot/107.png

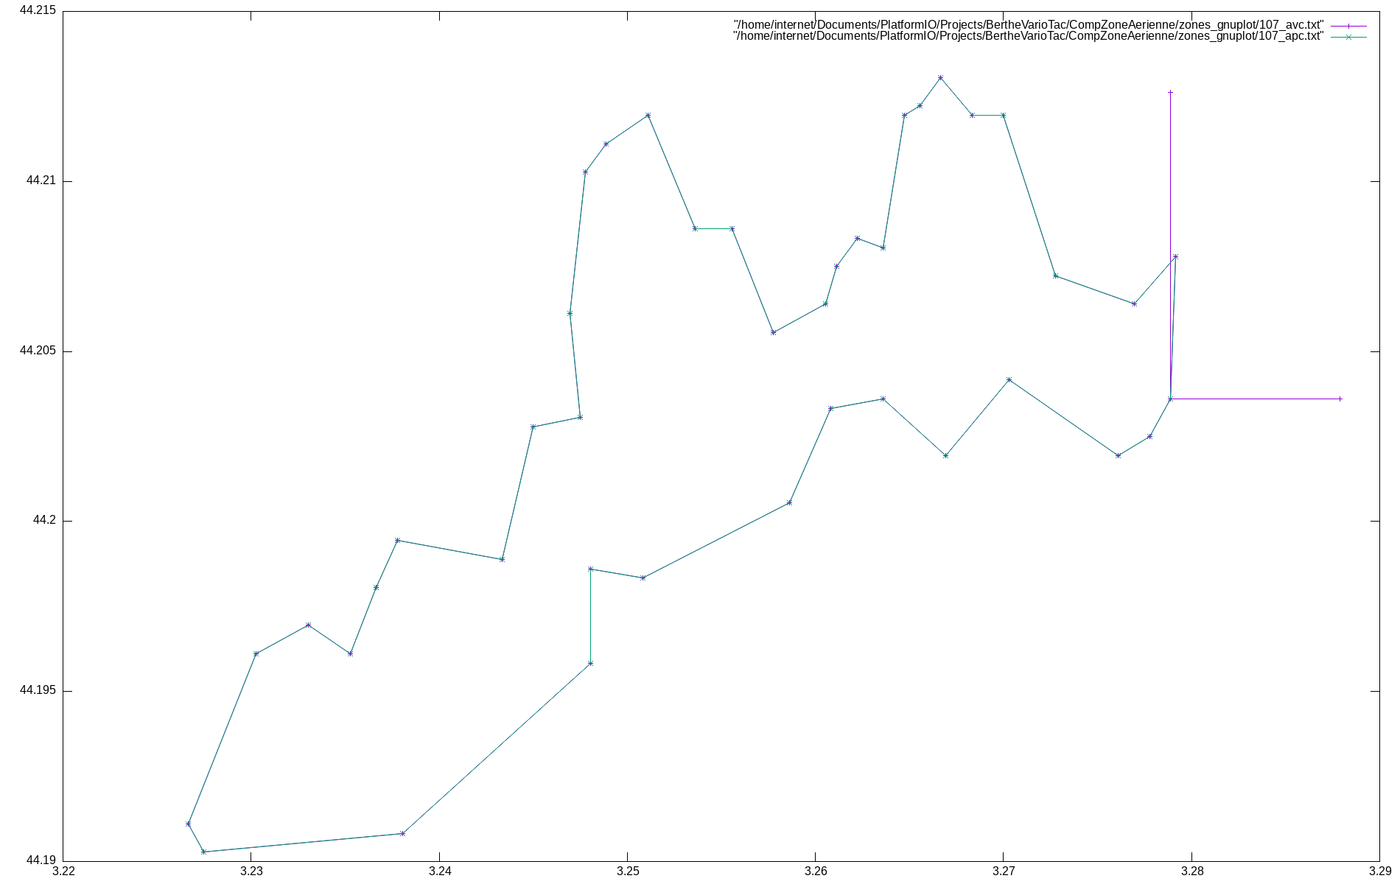
CompZoneAerienne/zones_gnuplot/107.png
