gitberthe/BertheVarioTac/CompZoneAerienne/zones_gnuplot/109.png

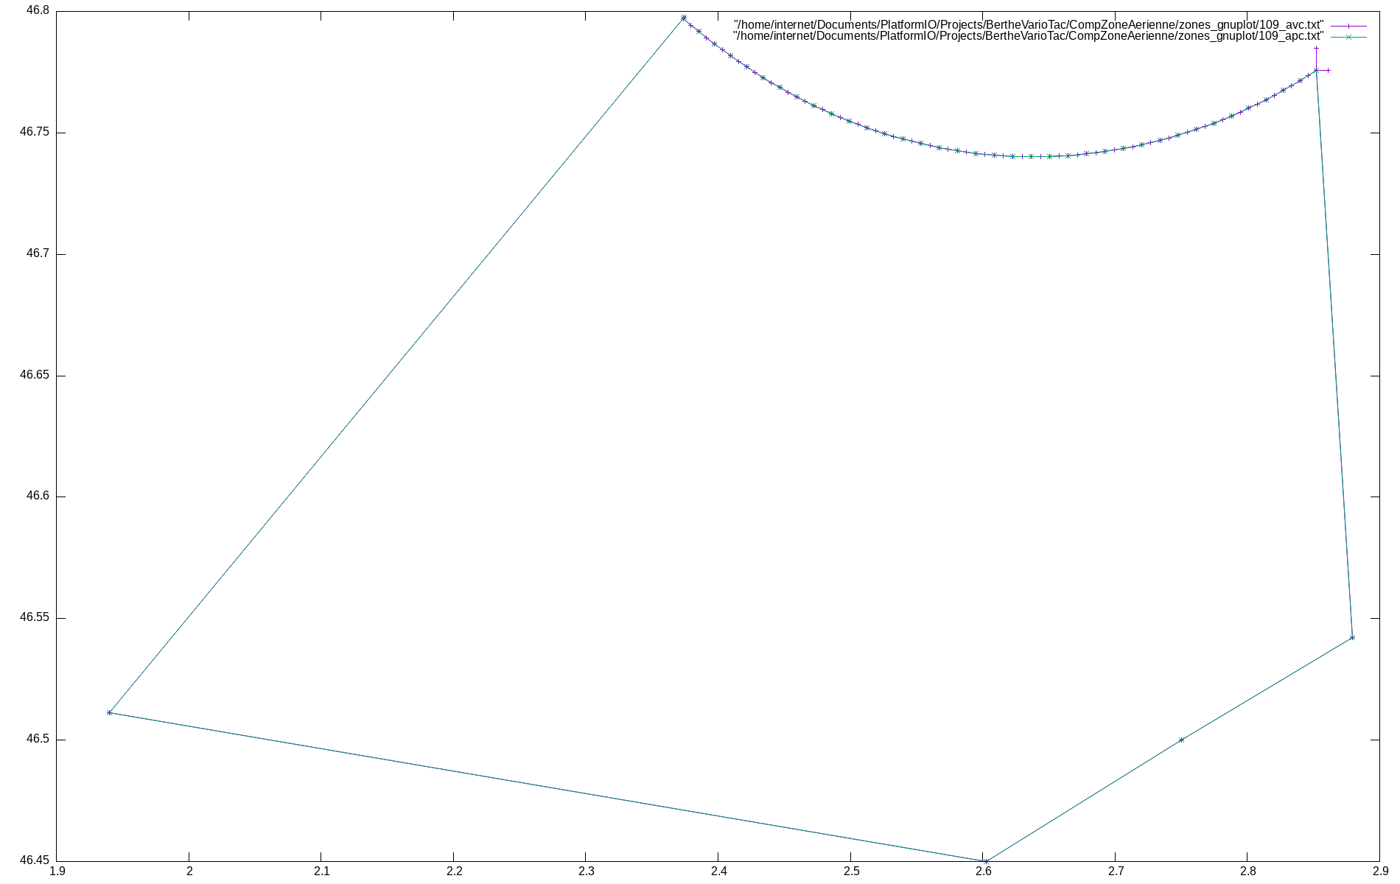
CompZoneAerienne/zones_gnuplot/109.png
