gitberthe/BertheVarioTac/CompZoneAerienne/zones_gnuplot/110.png

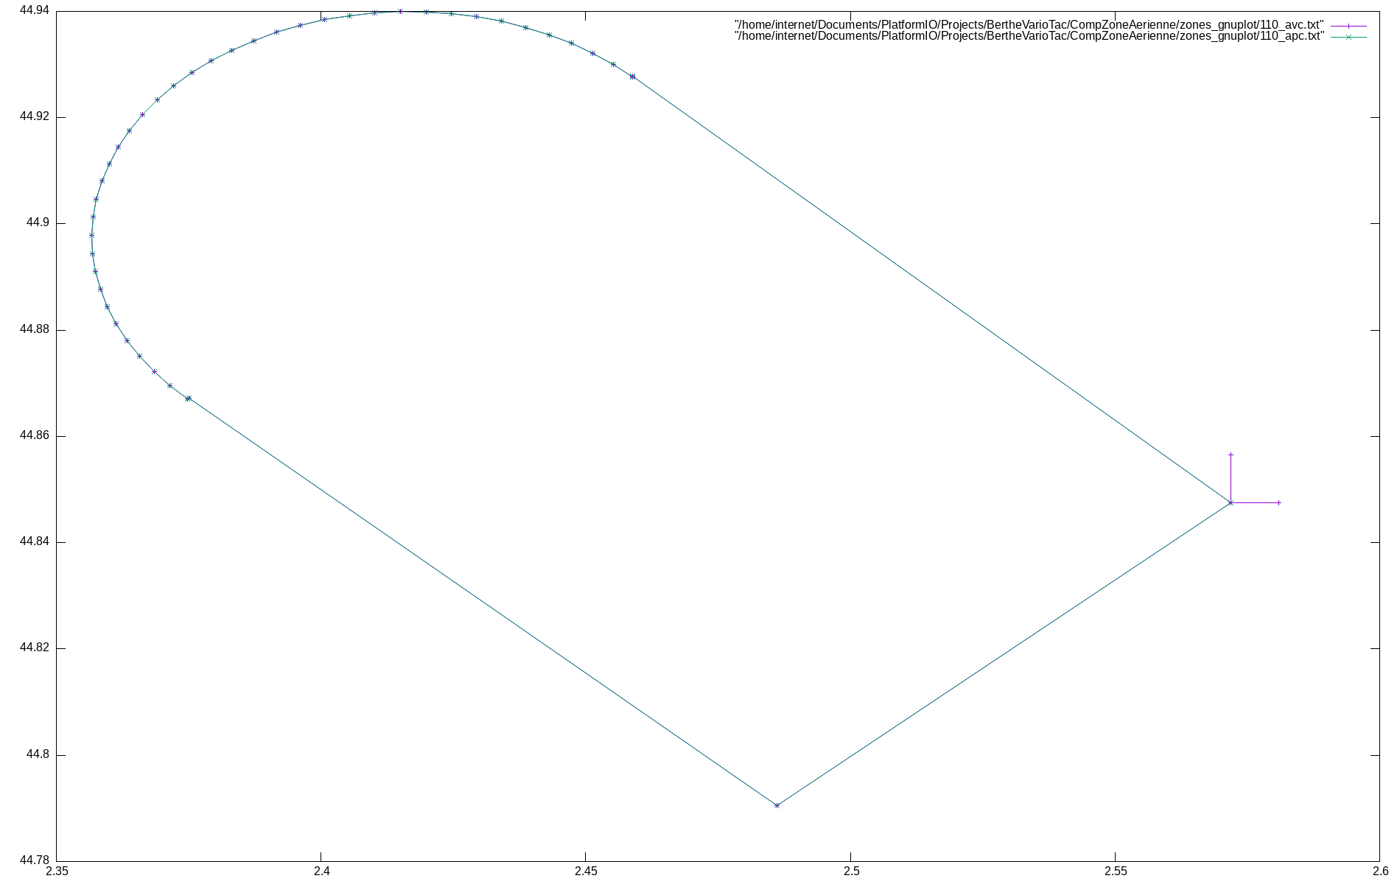
CompZoneAerienne/zones_gnuplot/110.png
