gitberthe/BertheVarioTac/CompZoneAerienne/zones_gnuplot/111.png

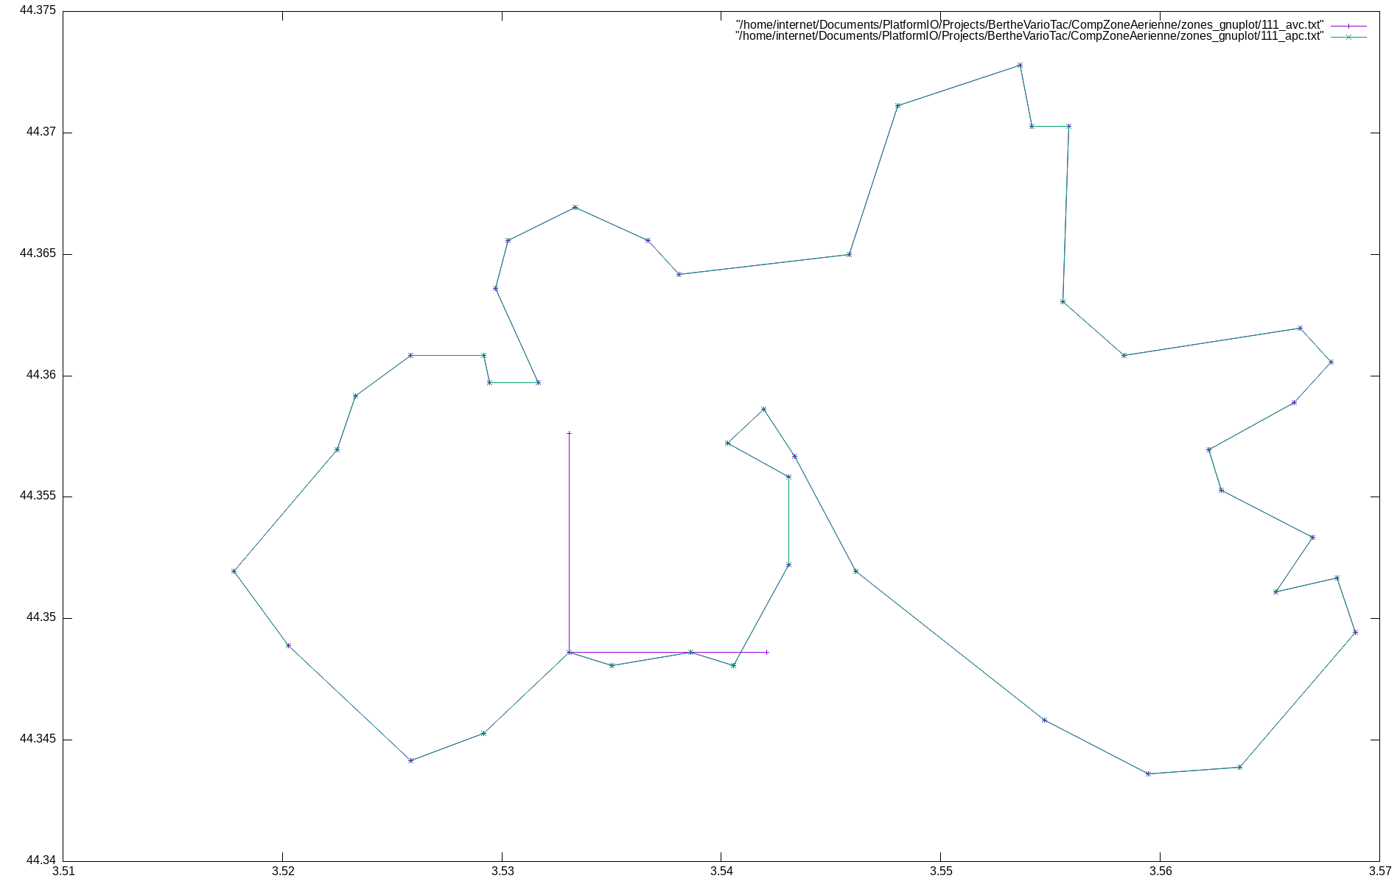
CompZoneAerienne/zones_gnuplot/111.png
