gitberthe/BertheVarioTac/CompZoneAerienne/zones_gnuplot/112.png

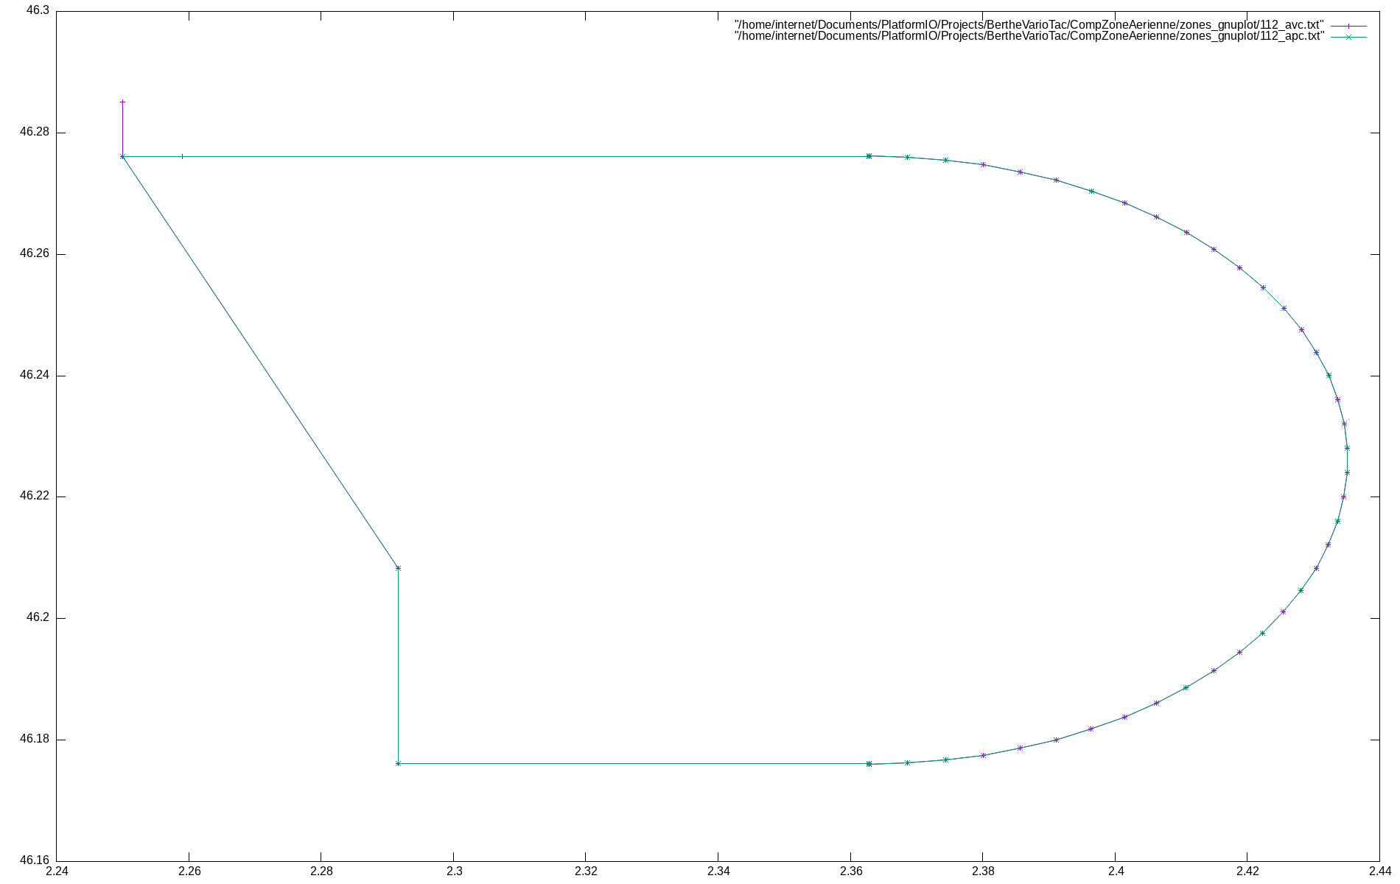
CompZoneAerienne/zones_gnuplot/112.png
