gitberthe/BertheVarioTac/CompZoneAerienne/zones_gnuplot/113.png

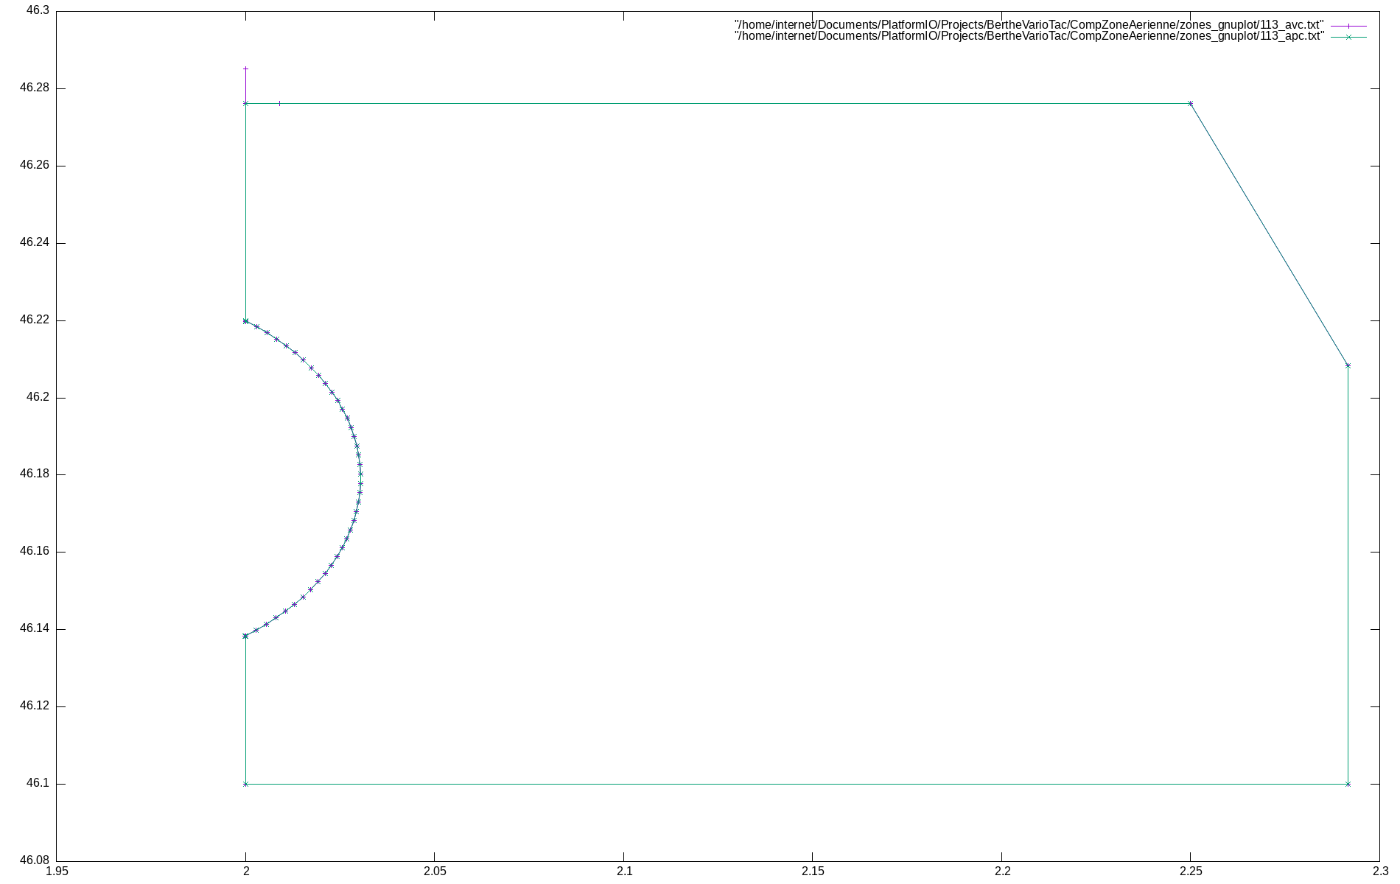
CompZoneAerienne/zones_gnuplot/113.png
