gitberthe/BertheVarioTac/CompZoneAerienne/zones_gnuplot/114.png

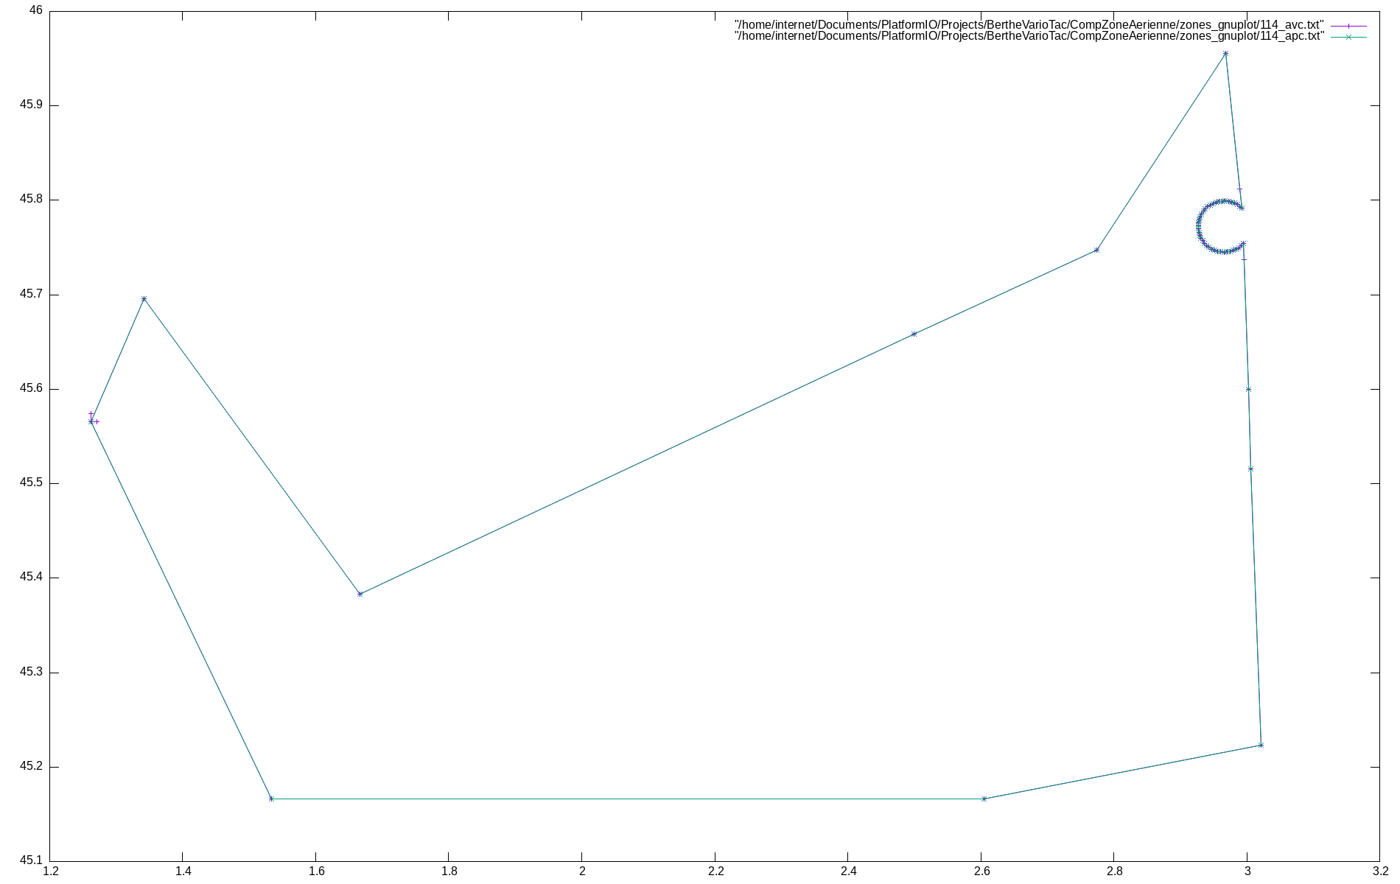
CompZoneAerienne/zones_gnuplot/114.png
