gitberthe/BertheVarioTac/CompZoneAerienne/zones_gnuplot/116.png

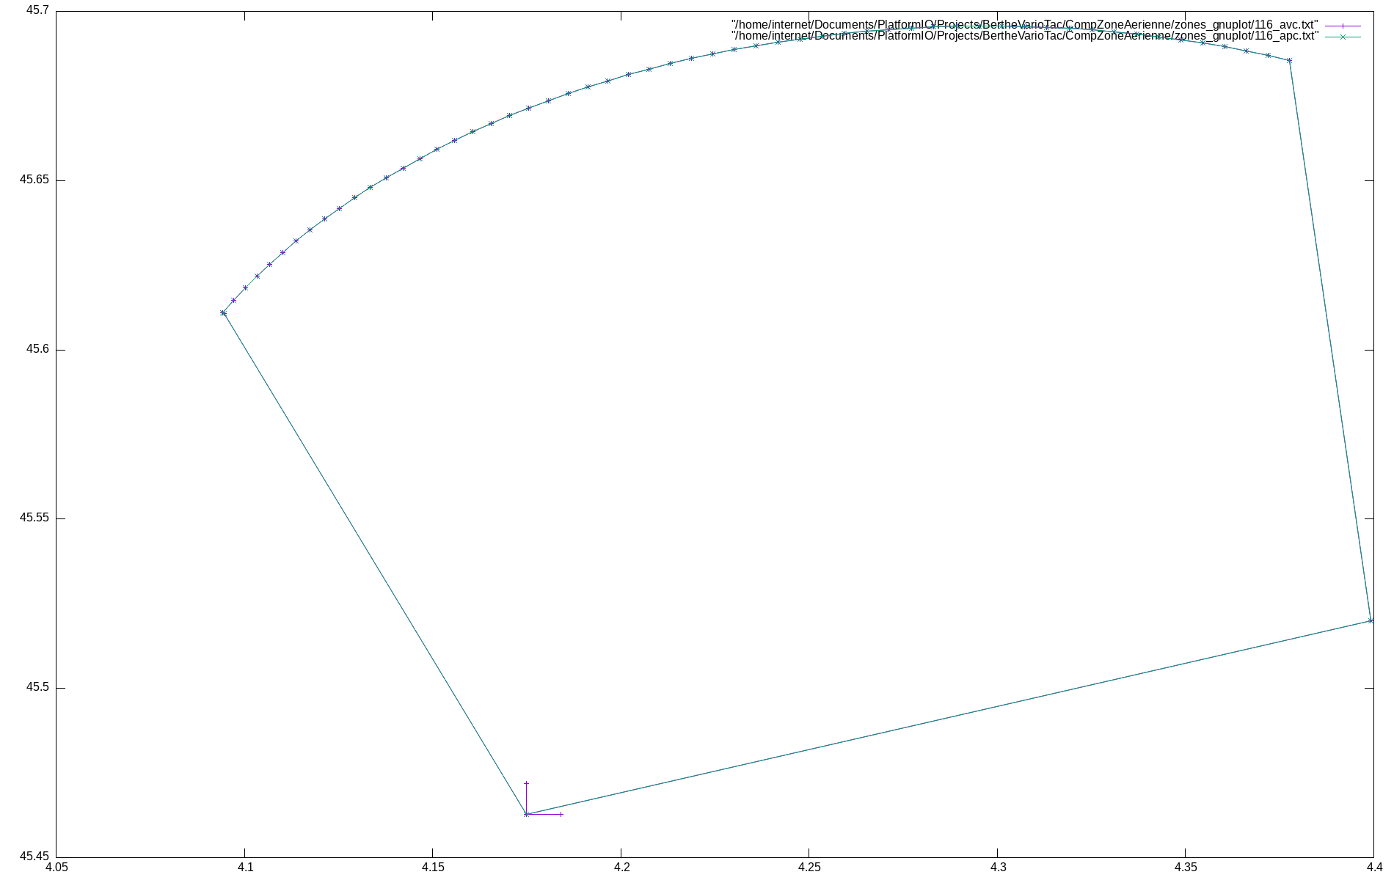
CompZoneAerienne/zones_gnuplot/116.png
