gitberthe/BertheVarioTac/CompZoneAerienne/zones_gnuplot/117.png

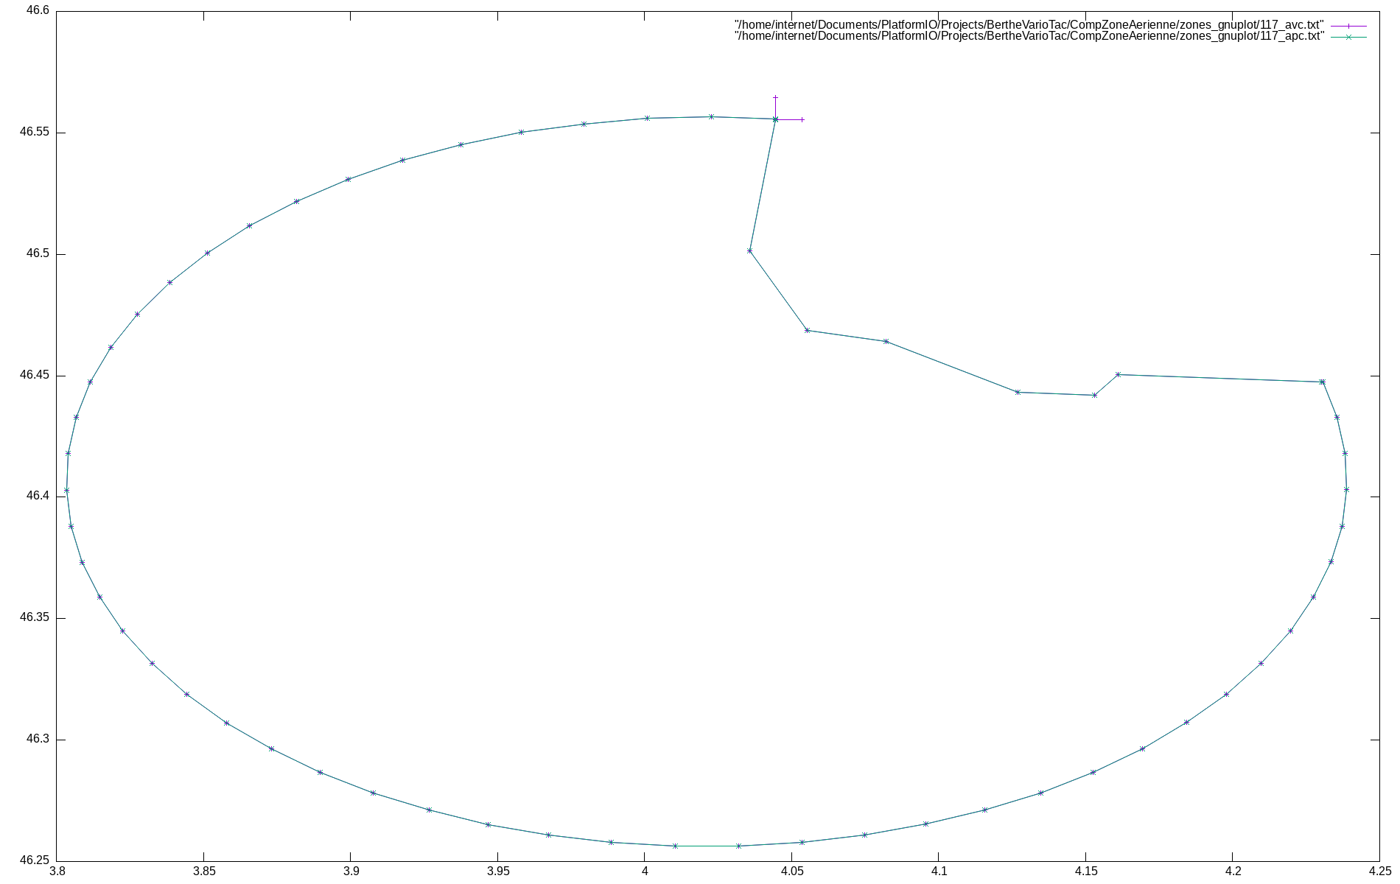
CompZoneAerienne/zones_gnuplot/117.png
