gitberthe/BertheVarioTac/CompZoneAerienne/zones_gnuplot/118.png

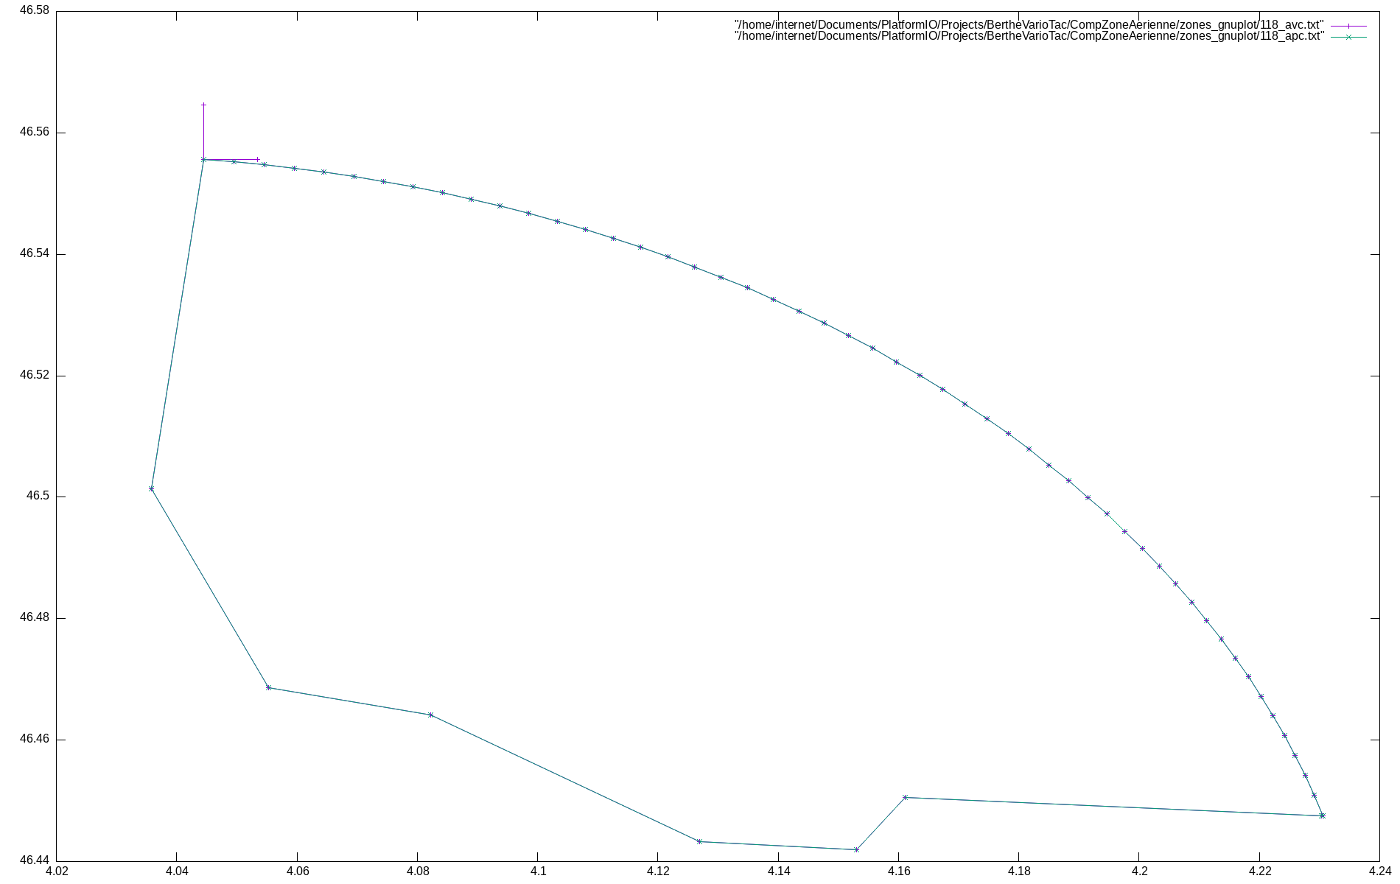
CompZoneAerienne/zones_gnuplot/118.png
