gitberthe/BertheVarioTac/CompZoneAerienne/zones_gnuplot/120.png

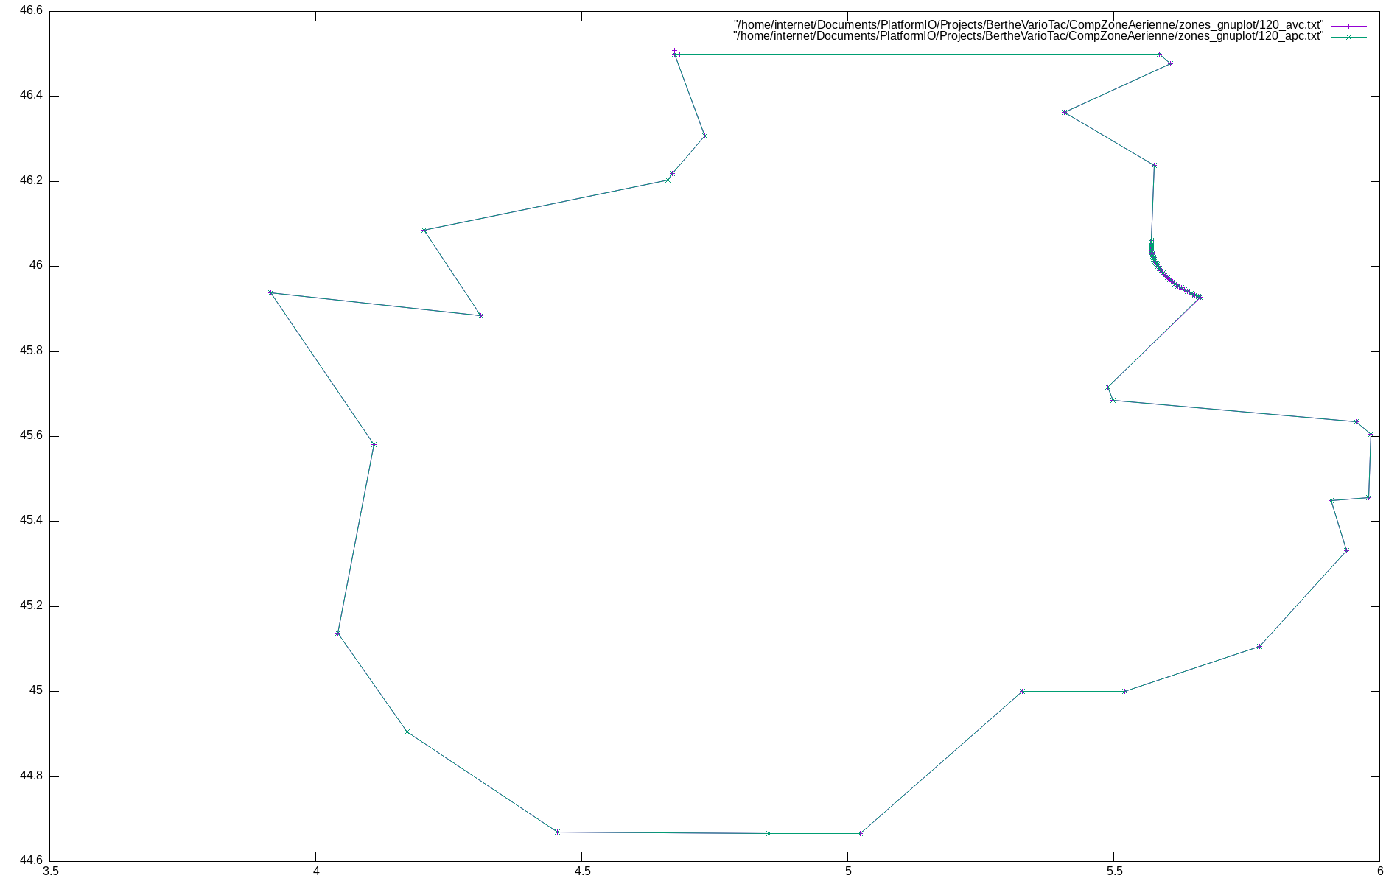
CompZoneAerienne/zones_gnuplot/120.png
