gitberthe/BertheVarioTac/CompZoneAerienne/zones_gnuplot/121.png

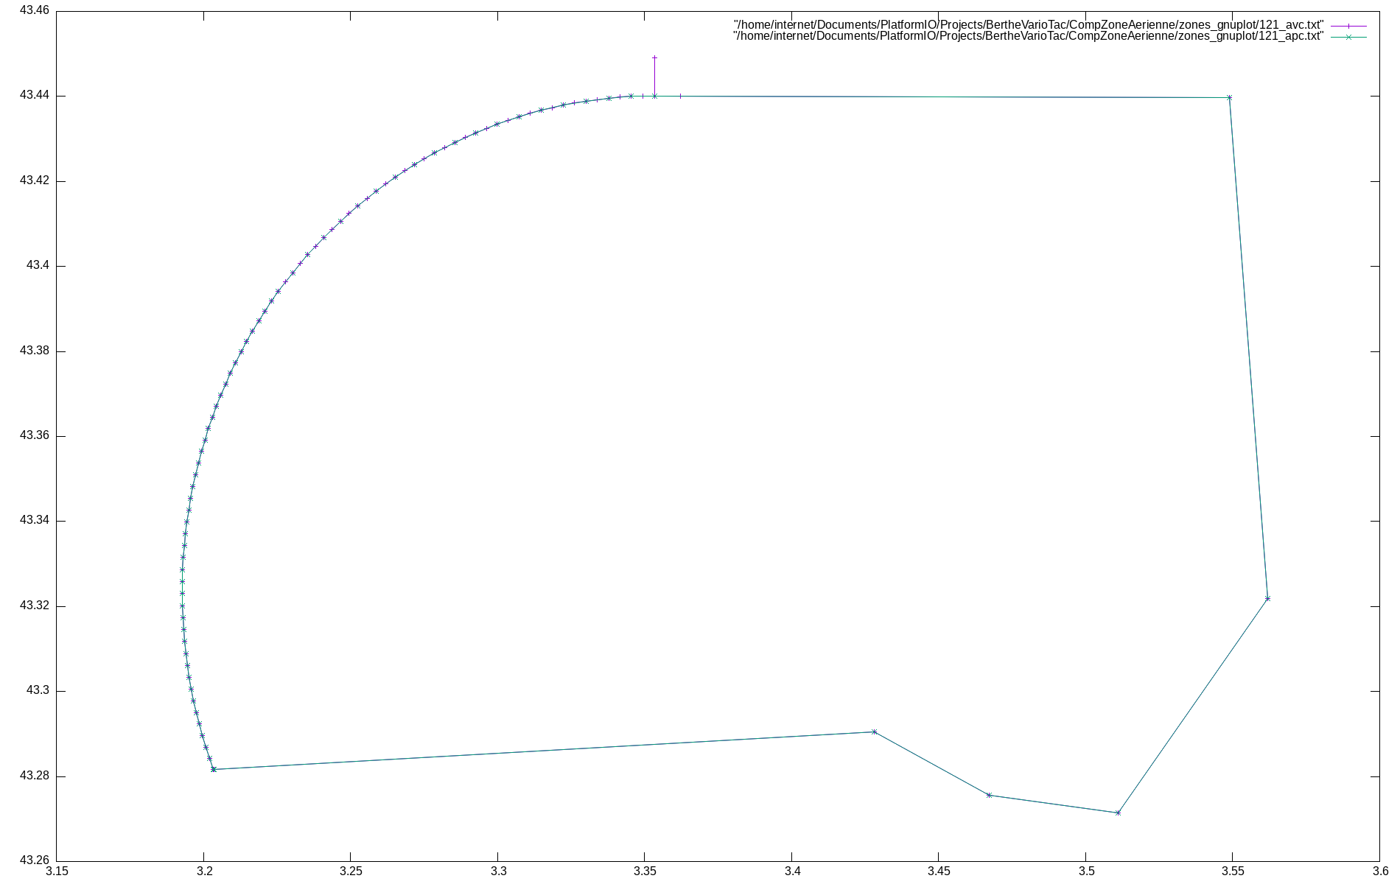
CompZoneAerienne/zones_gnuplot/121.png
