gitberthe/BertheVarioTac/CompZoneAerienne/zones_gnuplot/122.png

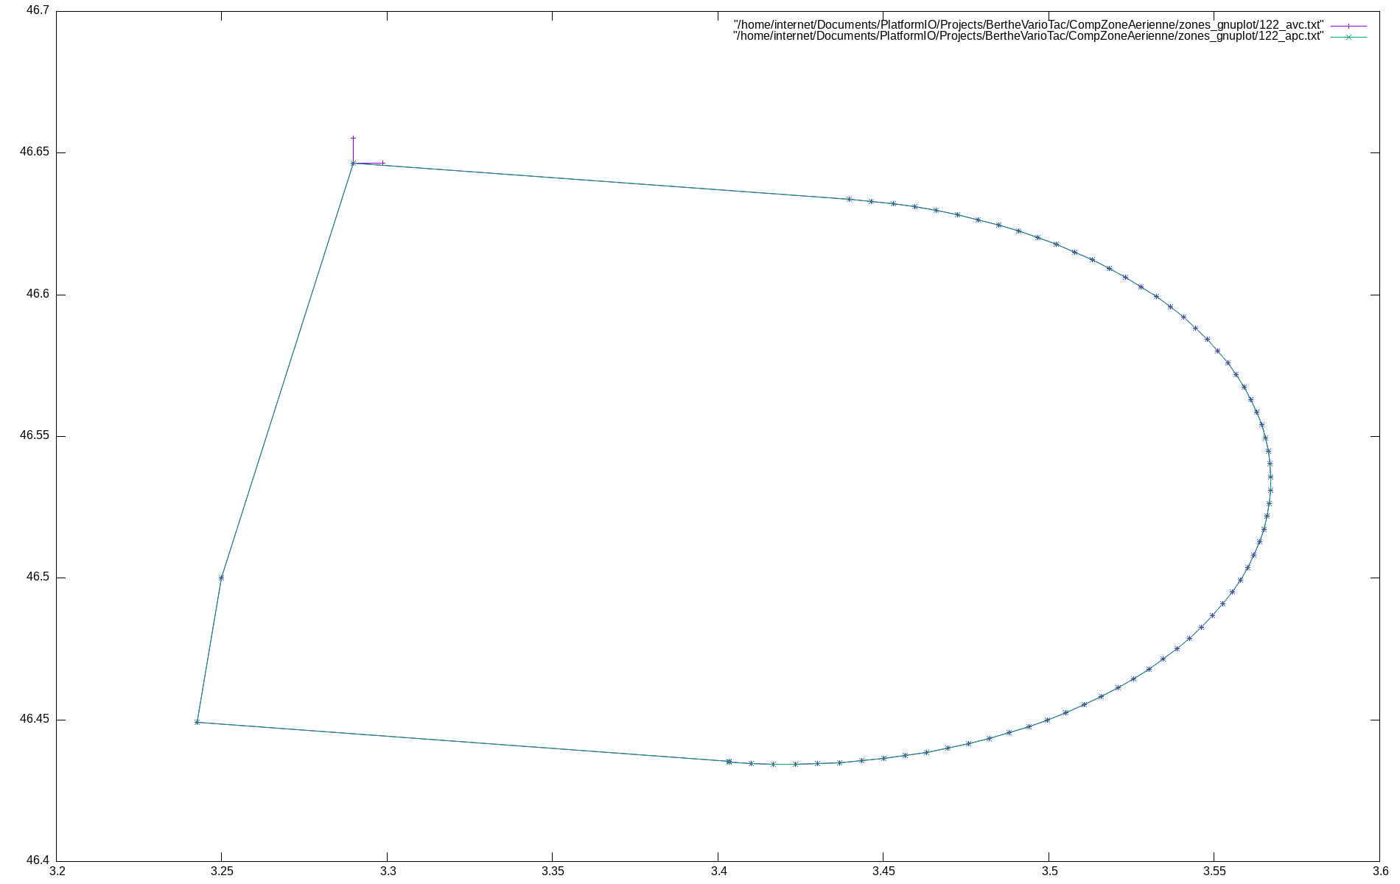
CompZoneAerienne/zones_gnuplot/122.png
