gitberthe/BertheVarioTac/CompZoneAerienne/zones_gnuplot/123.png

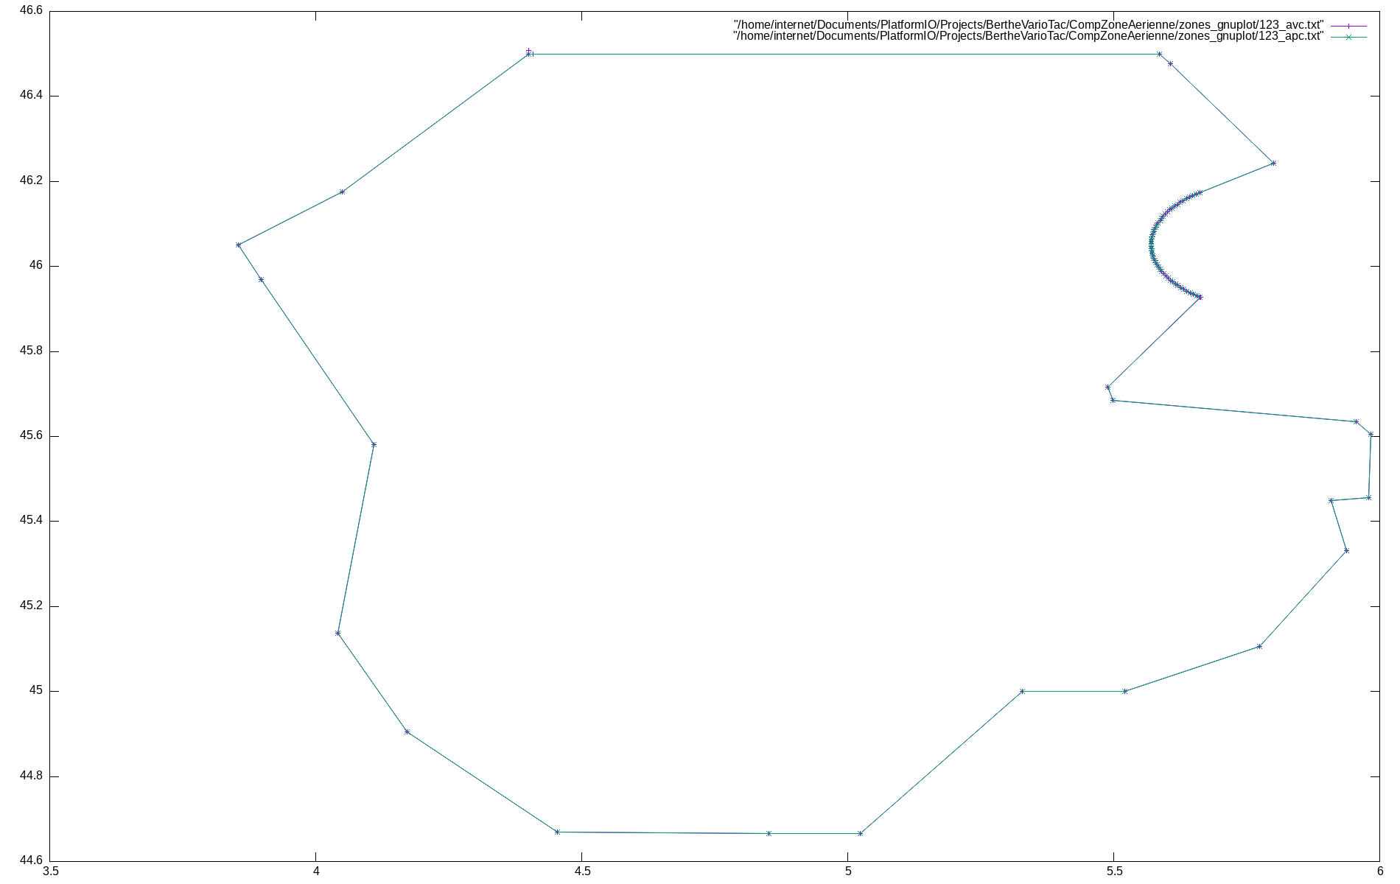
CompZoneAerienne/zones_gnuplot/123.png
