gitberthe/BertheVarioTac/CompZoneAerienne/zones_gnuplot/124.png

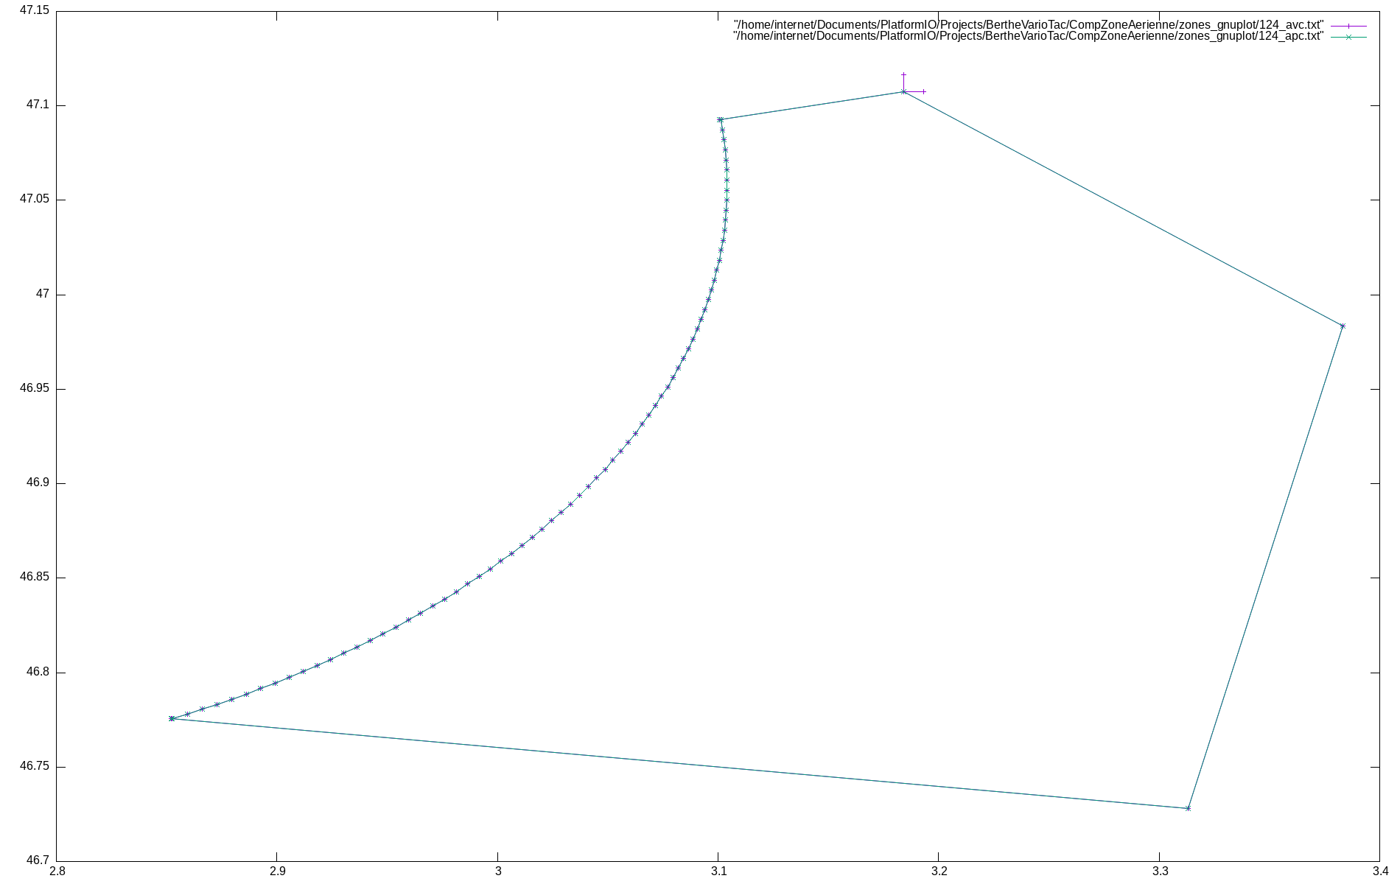
CompZoneAerienne/zones_gnuplot/124.png
