gitberthe/BertheVarioTac/CompZoneAerienne/zones_gnuplot/125.png

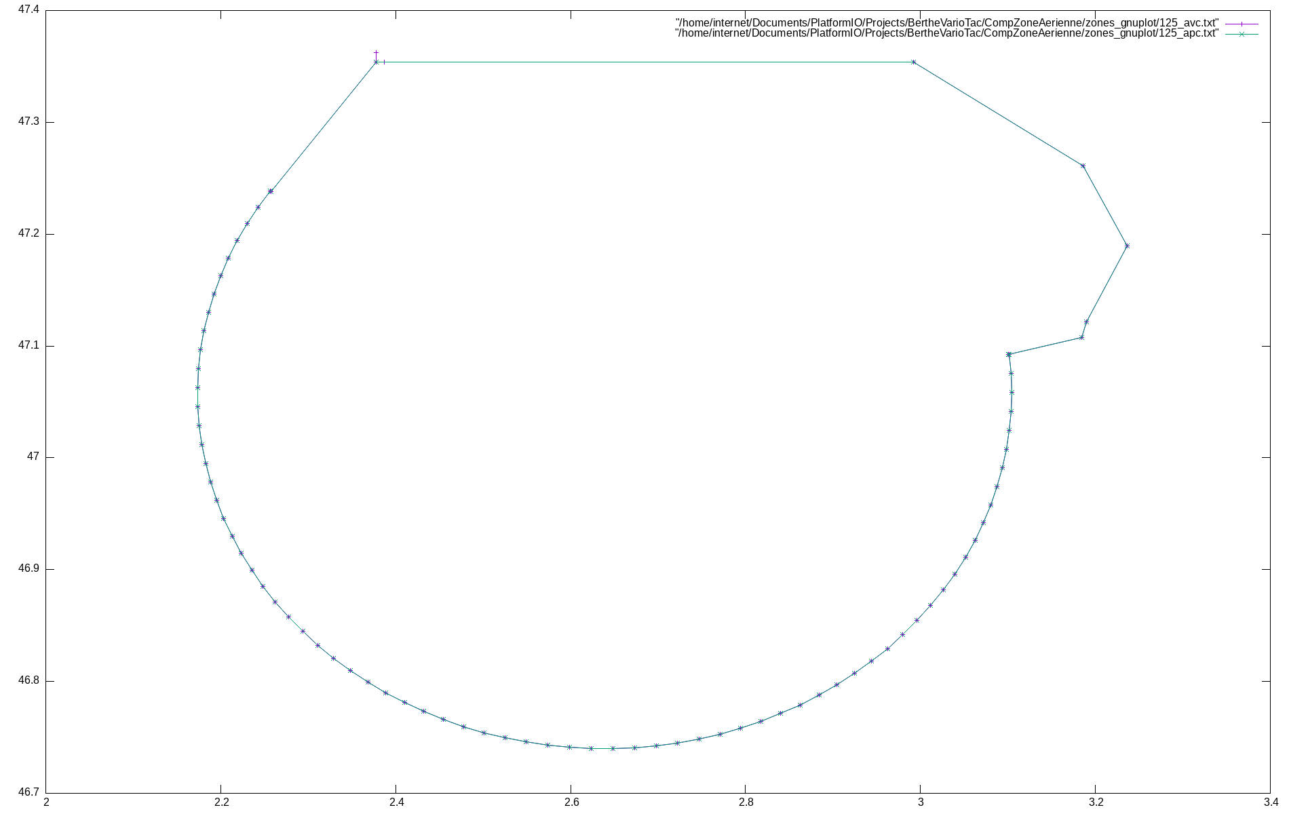
CompZoneAerienne/zones_gnuplot/125.png
