gitberthe/BertheVarioTac/CompZoneAerienne/zones_gnuplot/126.png

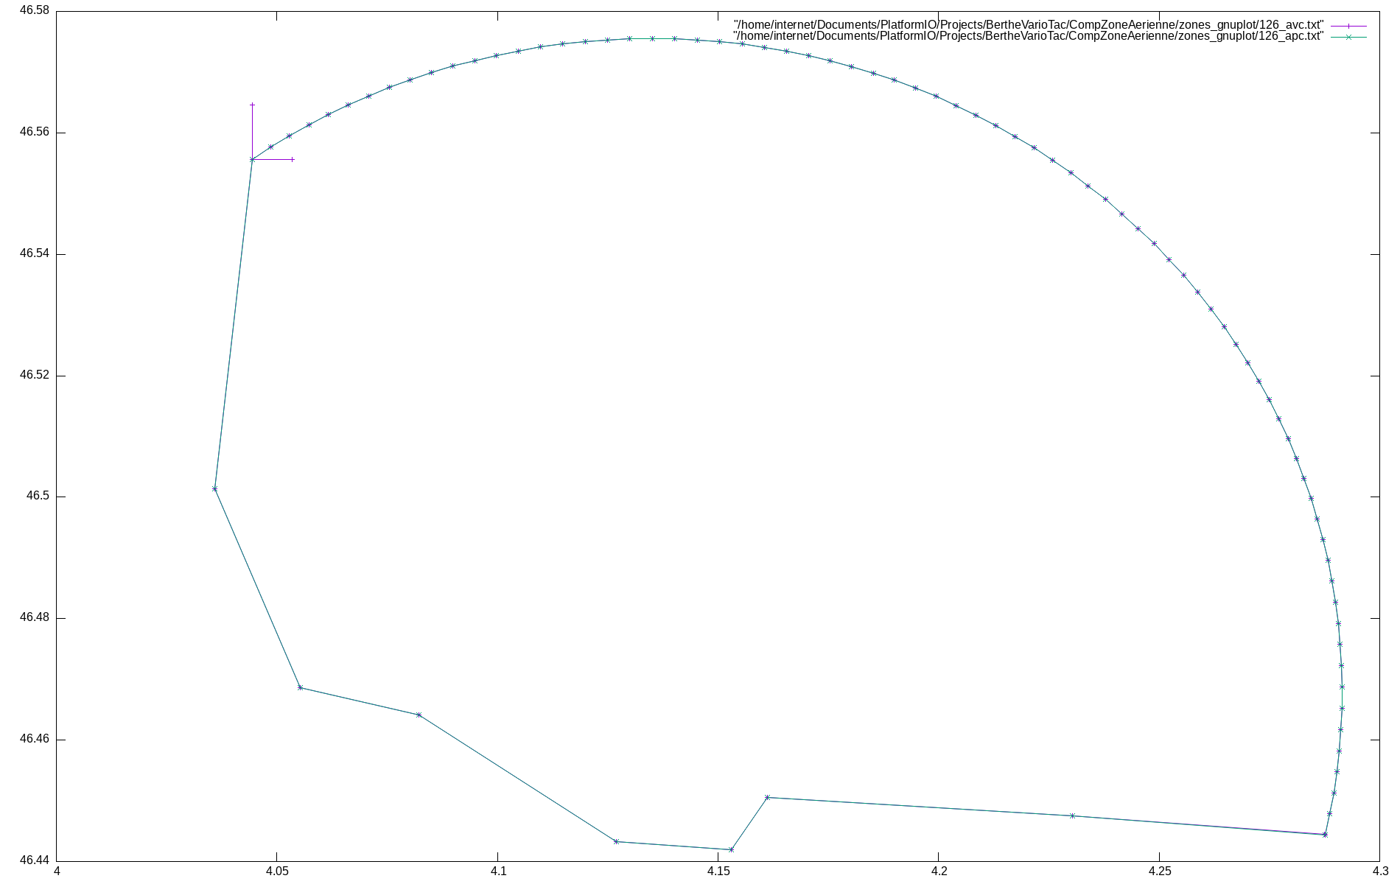
CompZoneAerienne/zones_gnuplot/126.png
