gitberthe/BertheVarioTac/CompZoneAerienne/zones_gnuplot/127.png

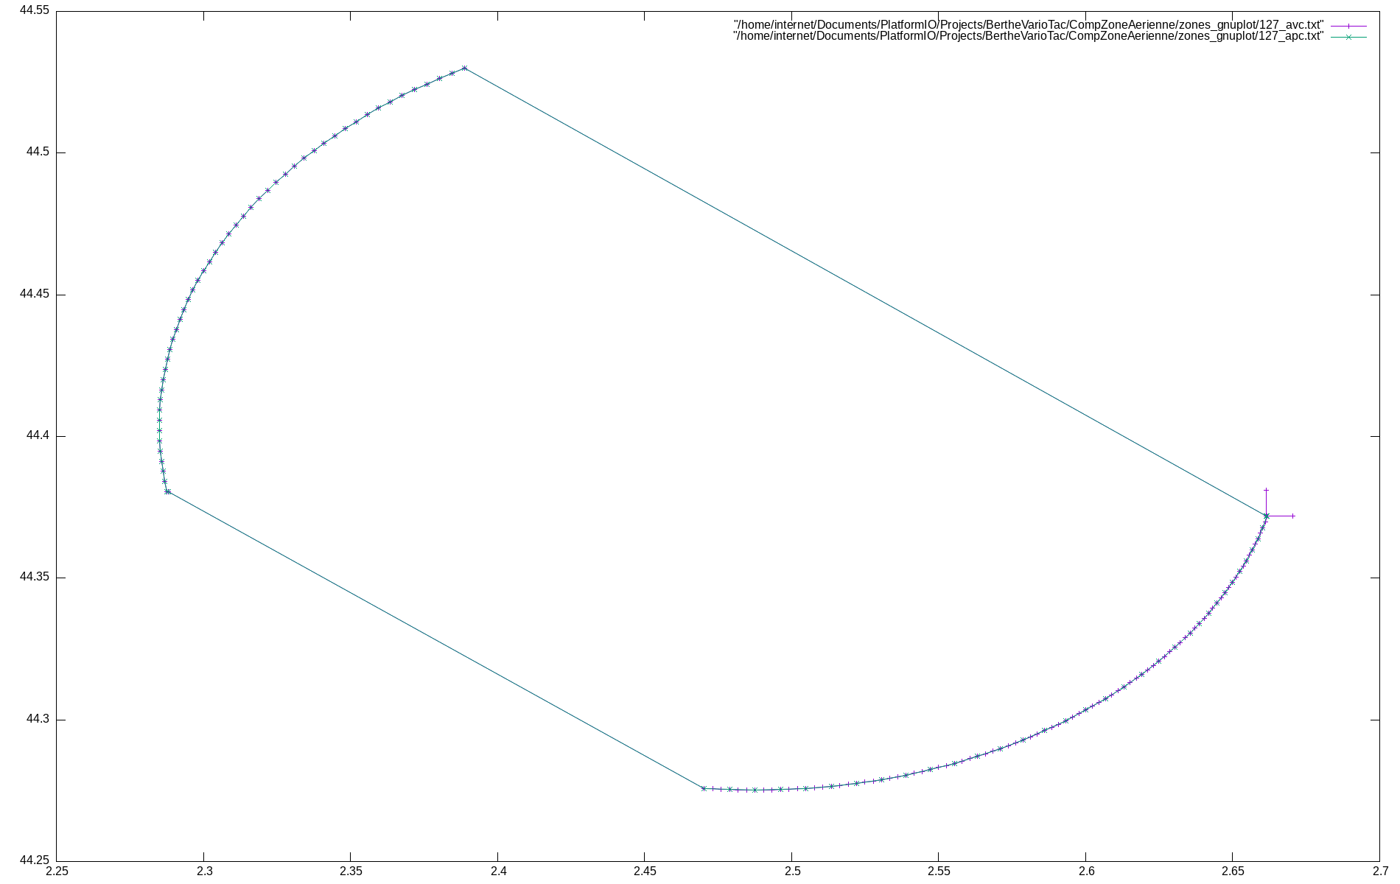
CompZoneAerienne/zones_gnuplot/127.png
