gitberthe/BertheVarioTac/CompZoneAerienne/zones_gnuplot/129.png

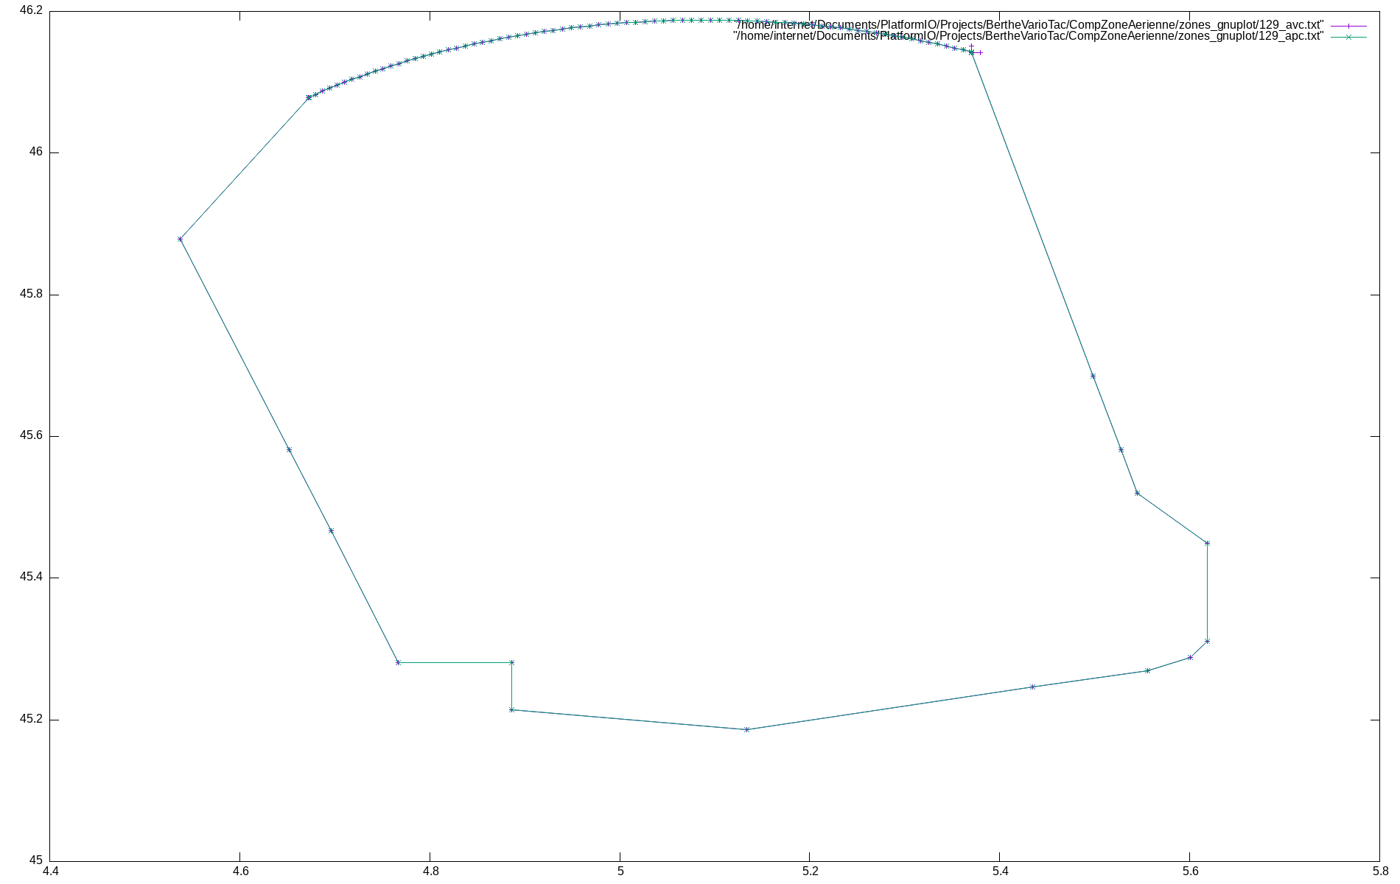
CompZoneAerienne/zones_gnuplot/129.png
