gitberthe/BertheVarioTac/CompZoneAerienne/zones_gnuplot/130.png

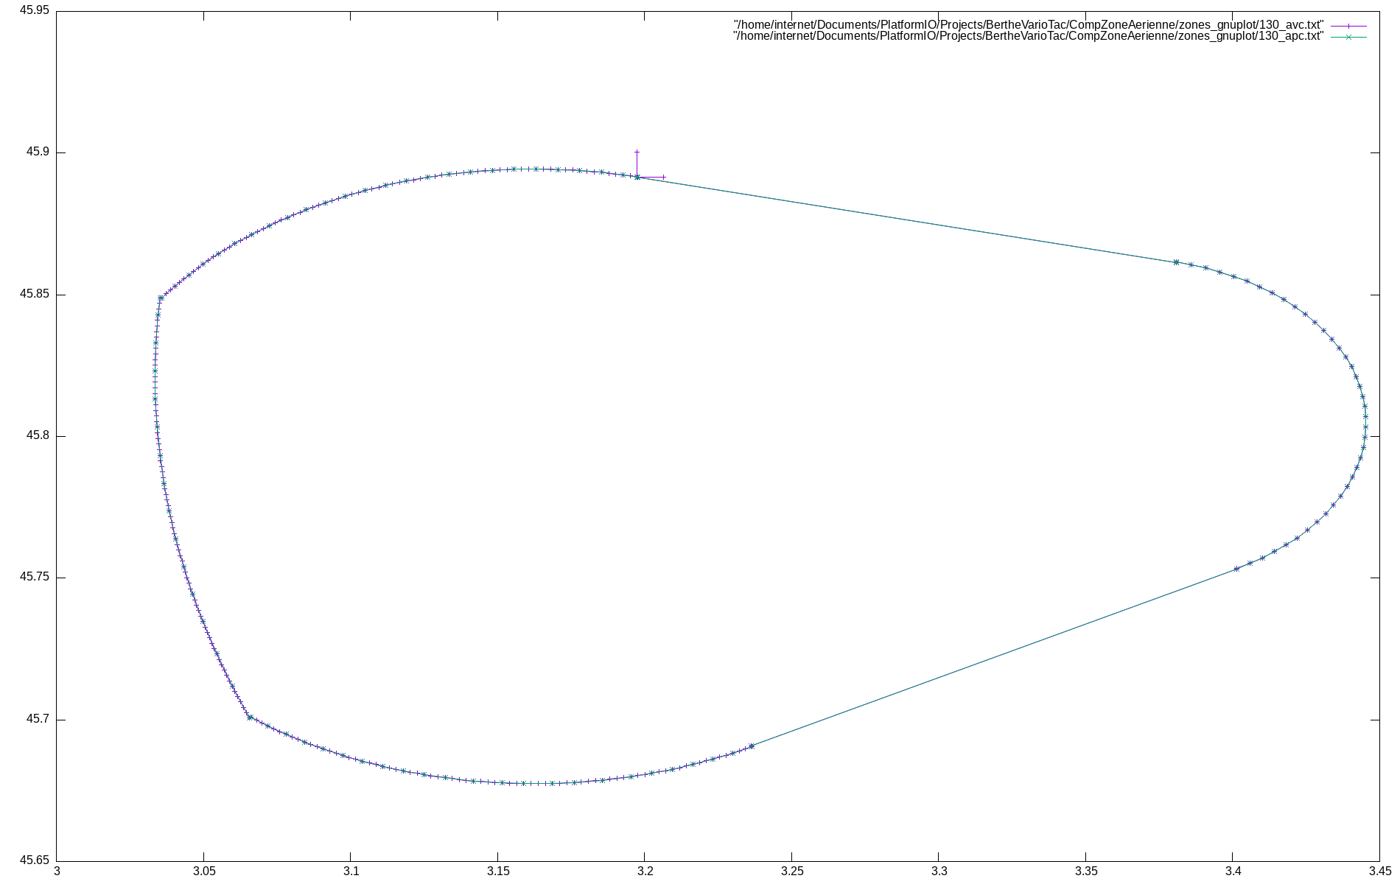
CompZoneAerienne/zones_gnuplot/130.png
