gitberthe/BertheVarioTac/CompZoneAerienne/zones_gnuplot/131.png

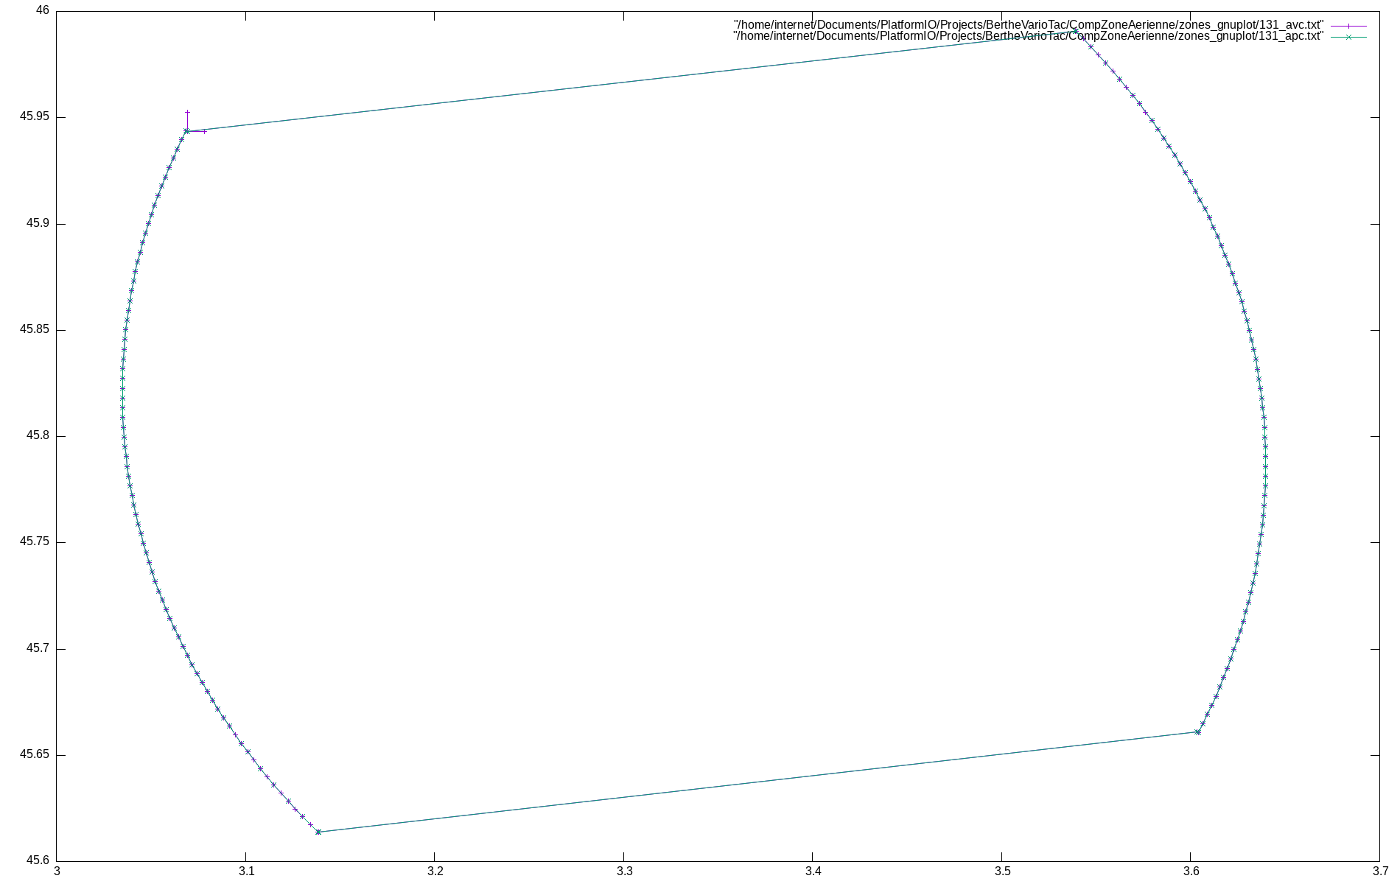
CompZoneAerienne/zones_gnuplot/131.png
