gitberthe/BertheVarioTac/CompZoneAerienne/zones_gnuplot/132.png

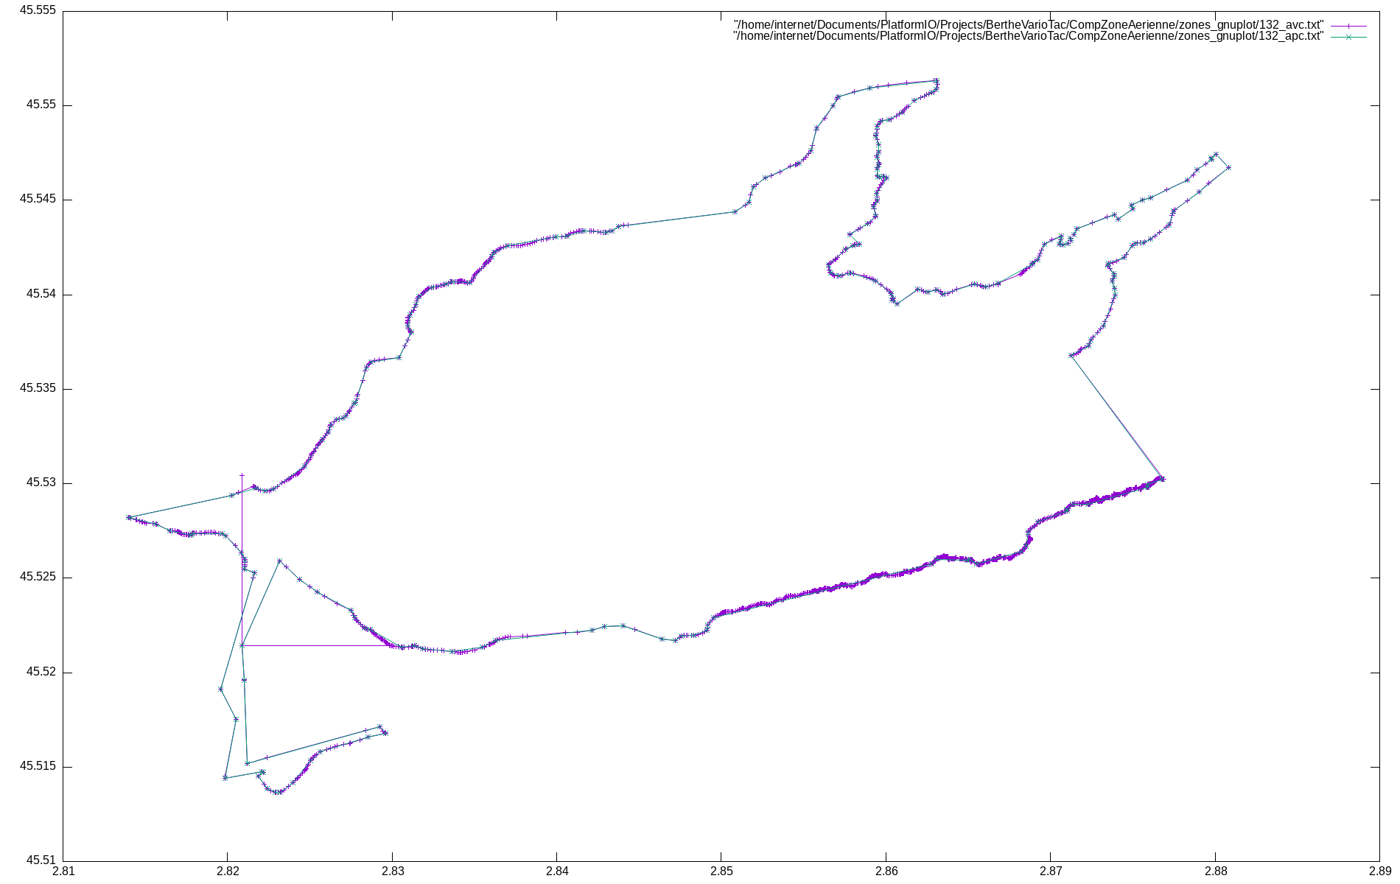
CompZoneAerienne/zones_gnuplot/132.png
