gitberthe/BertheVarioTac/CompZoneAerienne/zones_gnuplot/133.png

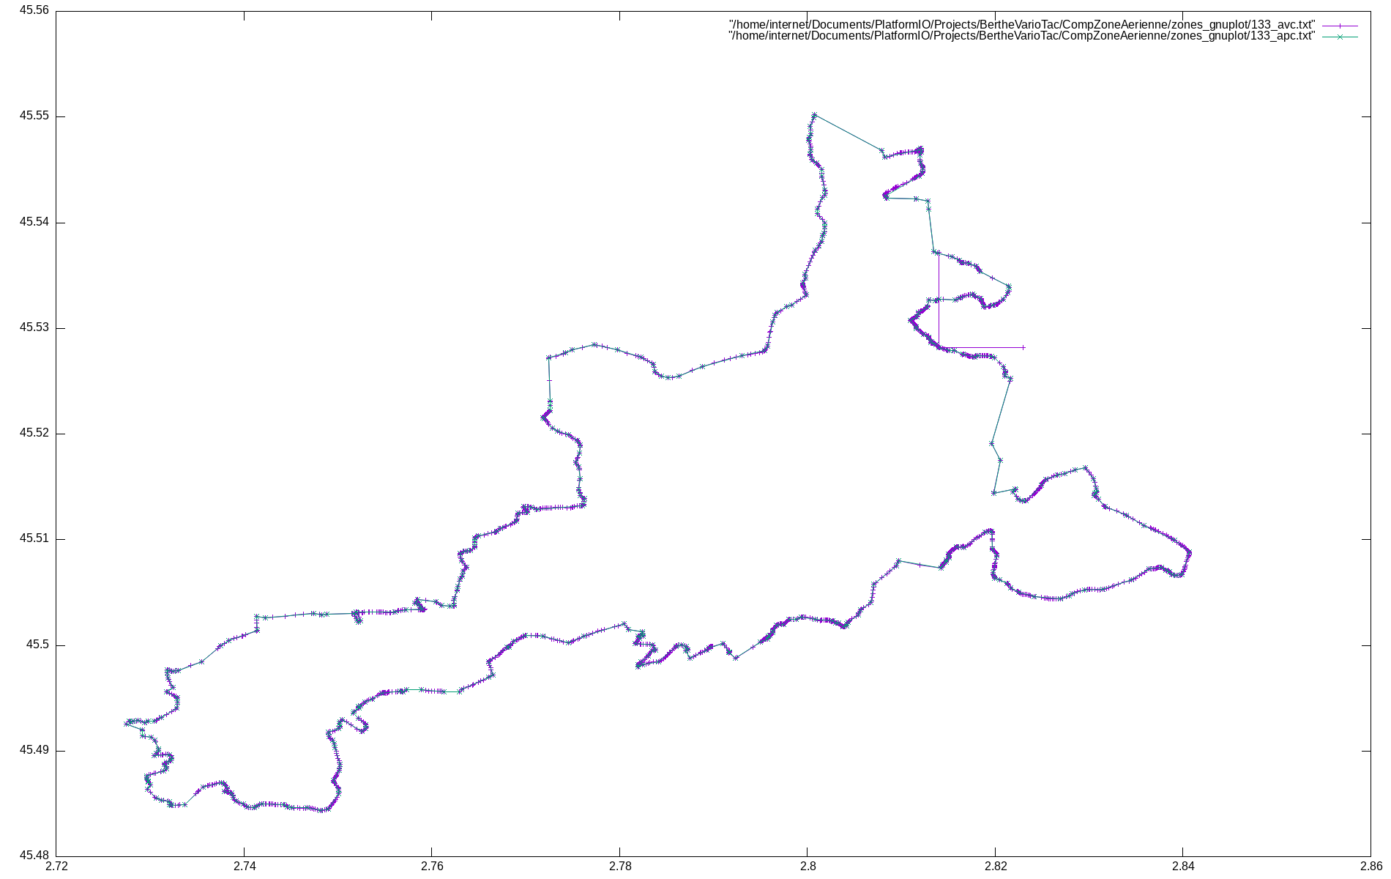
CompZoneAerienne/zones_gnuplot/133.png
