gitberthe/BertheVarioTac/CompZoneAerienne/zones_gnuplot/134.png

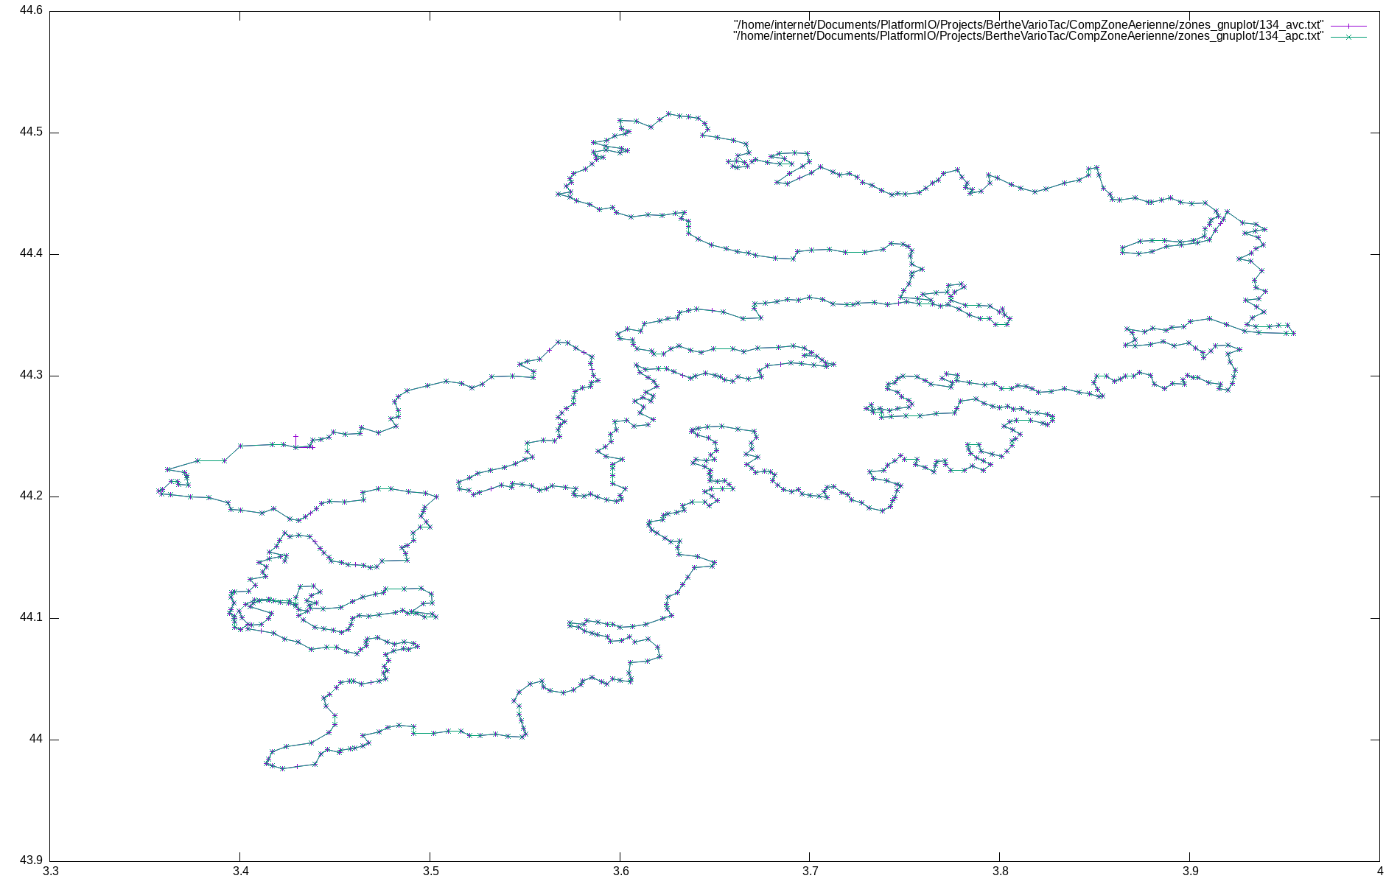
CompZoneAerienne/zones_gnuplot/134.png
