gitberthe/BertheVarioTac/documentation/01-specifiation-carte/ESP32-WROOM-1 Pin definition.png

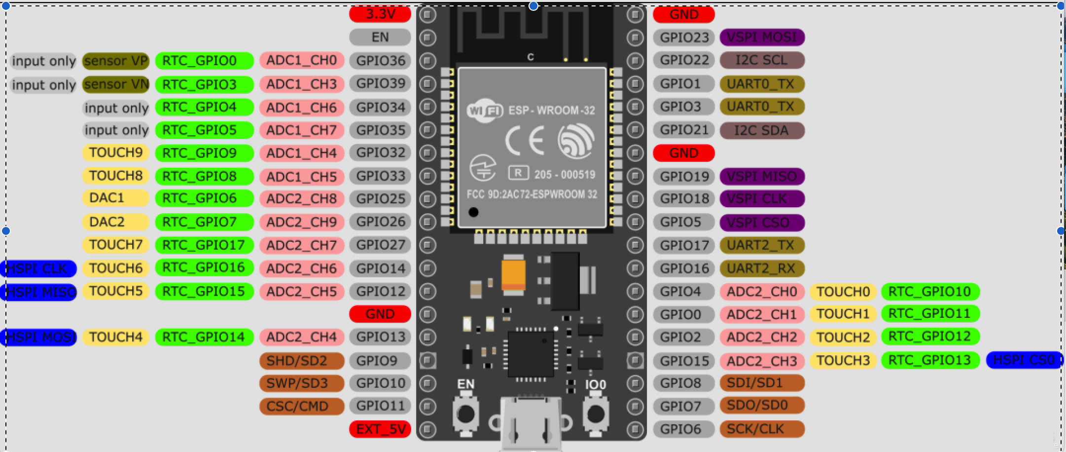
documentation/01-specifiation-carte/ESP32-WROOM-1 Pin definition.png
