gitberthe/BertheVarioTac/documentation/04-shema/ESP32-2432S028-LCM.jpg

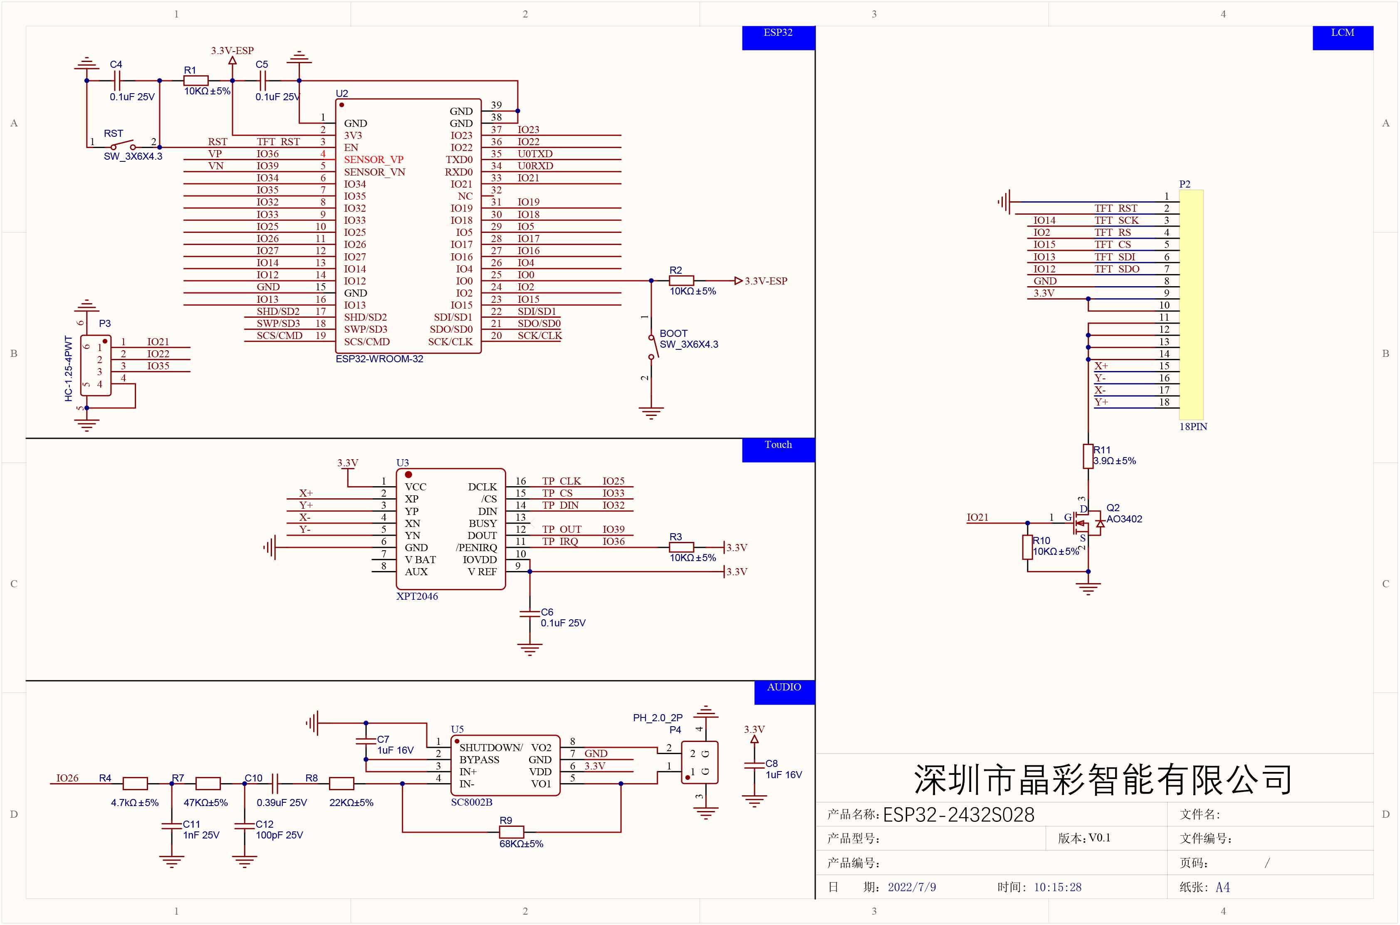
documentation/04-shema/ESP32-2432S028-LCM.jpg
