gitberthe/BertheVarioTac/documentation/04-shema/ESP32-2432S028-MCU.jpg

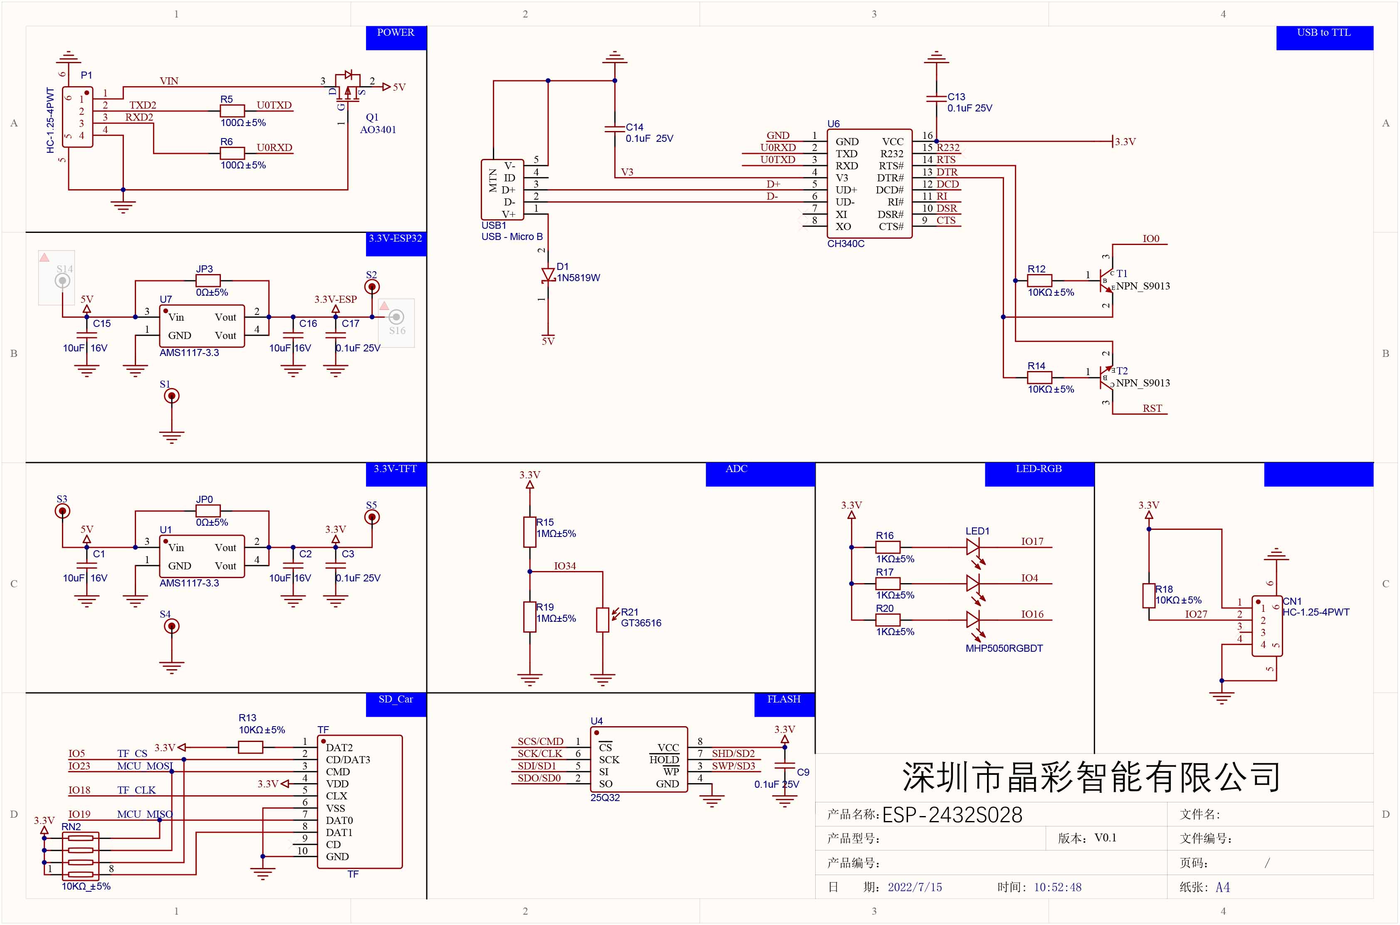
documentation/04-shema/ESP32-2432S028-MCU.jpg
