gitberthe/BertheVarioTac/BertheVarioTacPlatformIO/src/VarioCapBeep/CSoundSvr.cpp

////////////////////////////////////////////////////////////////////////////////
/// \file CSoundSvr.h
///
/// \brief
///
/// \date creation     : 03/10/2024
/// \date modification : 29/01/2025
///

#include "../BertheVarioTac.h"

////////////////////////////////////////////////////////////////////////////////
/// \brief Creation de la pile de demande
CSoundSvr::CSoundSvr()
{
// taille de 8
m_queue = xQueueCreate(SOUND_BUFFER_SIZE, sizeof(StSoundRequest));
}

////////////////////////////////////////////////////////////////////////////////
/// \brief Met un son dans la file d'attente.
void CSoundSvr::PostSoundRequest( const StSoundRequest * pReq )
{
xQueueSend(m_queue, (void*)pReq, (TickType_t)0);
}

////////////////////////////////////////////////////////////////////////////////
/// \brief Lance la tache de son
void CSoundSvr::LanceTacheSound()
{
g_GlobalVar.m_TaskArr[SOUNDSVR_NUM_TASK].m_Run = true ;
g_GlobalVar.m_TaskArr[SOUNDSVR_NUM_TASK].m_Stopped = false ;
xTaskCreatePinnedToCore(TacheSoundSvr, "SoundSvr", SOUNDSVR_STACK_SIZE , this, SOUNDSVR_PRIORITY, NULL, SOUNDSVR_CORE);
}

////////////////////////////////////////////////////////////////////////////////
/// \brief Tache pour jouer les sons qui sont dans la file d'attente.
void CSoundSvr::TacheSoundSvr(void* param)
{
g_GlobalVar.m_TaskArr[SOUNDSVR_NUM_TASK].m_Stopped = false ;

const int channel = 1 ;
const int resolution = 8; // Résolution de 8 bits, 256 valeurs possibles

// boucle du serveur
StSoundRequest SoundRequest ;
ledcAttachChannel(SPEAKER_PIN, SoundRequest.m_Frequence , resolution , channel );
ledcDetach(SPEAKER_PIN) ;
while (g_GlobalVar.m_TaskArr[SOUNDSVR_NUM_TASK].m_Run)
    {
    // attente 10 millisecondes
    if( !xQueueReceive(g_GlobalVar.m_queue, &(SoundRequest), (TickType_t)0))
        {
        delay( 5 ) ;
        continue ;
        }

    // traitement de la demande
    if ( SoundRequest.m_Frequence > 0 )
        {
        ledcAttachChannel(SPEAKER_PIN, SoundRequest.m_Frequence , resolution , channel );
        ledcWrite(SPEAKER_PIN, SoundRequest.m_Cycle );
        }

    // attente pendant le son
    delay( SoundRequest.m_DelayMs ) ;

    // desactivation du son
    ledcDetach(SPEAKER_PIN) ;
    }

g_GlobalVar.m_TaskArr[SOUNDSVR_NUM_TASK].m_Stopped = true ;
while( true )
    vTaskDelete(NULL) ;
}

/*
////////////////////////////////////////////////////////////////////////////////
/// \brief Tache pour jouer les sons qui sont dans la file d'attente.
void CSoundSvr::TacheSoundSvr(void* param)
{
g_GlobalVar.m_TaskArr[SOUNDSVR_NUM_TASK].m_Stopped = false ;

// utilisation du convertisseur DA
dac_output_enable(DAC_CHANNEL_2);
dac_cw_config_t config ;
config.en_ch = DAC_CHANNEL_2 ; // DAC_GPIO26_CHANNEL ;
//config.scale = DAC_CW_SCALE_8 ;   // le moins fort
//config.scale = DAC_CW_SCALE_1 ; // le plus fort

// boucle du serveur
StSoundRequest SoundRequest ;
while (g_GlobalVar.m_TaskArr[SOUNDSVR_NUM_TASK].m_Run)
    {
    // attente 10 millisecondes
    if( !xQueueReceive(g_GlobalVar.m_queue, &(SoundRequest), (TickType_t)0))
        {
        delay( 10 ) ;
        continue ;
        }

    //g_GlobalVar.m_Screen.m_MutexTft.PrendreMutex() ;

    // traitement de la demande
    if ( SoundRequest.m_Frequence > 0 )
        {
        config.freq = SoundRequest.m_Frequence ;
        config.scale= SoundRequest.m_Volume ;
        dac_cw_generator_config( & config ) ;
        dac_cw_generator_enable() ;
        }

    //g_GlobalVar.m_Screen.m_MutexTft.RelacherMutex() ;

    // attente pendant le son
    delay( SoundRequest.m_DelayMs ) ;

    // desactivation du son
    //g_GlobalVar.m_Screen.m_MutexTft.PrendreMutex() ;
     dac_cw_generator_disable() ;
    //g_GlobalVar.m_Screen.m_MutexTft.RelacherMutex() ;
    }

g_GlobalVar.m_TaskArr[SOUNDSVR_NUM_TASK].m_Stopped = true ;
while( true )
    vTaskDelete(NULL) ;
}
*/

//fin :
//pinMode(26, OUTPUT);
/*int freq = 3000; // 3000 Hz
const int ledChannel = 1;
const int resolution = 8; // Résolution de 8 bits
const int ledPin = 26;
int dutyCycle = 255/2 ;

ledcWrite(ledChannel, dutyCycle);
ledcSetup(ledChannel, freq, resolution);
ledcAttachPin(ledPin, ledChannel);
//ledcWriteTone( ledChannel, freq ) ;
//pinMode(22, OUTPUT);

while( true )
    delay( 2000 ) ;

freq = 7000 ;
ledcWrite(ledChannel, dutyCycle);
ledcSetup(ledChannel, freq, resolution);
ledcAttachPin(ledPin, ledChannel);
//ledcWriteTone( ledChannel, freq ) ;
ledcDetachPin( ledPin ) ; //*/
