gitberthe/BertheVarioTac/BertheVarioTacPlatformIO/src/Screen/CText2Screen.cpp

////////////////////////////////////////////////////////////////////////////////
/// \file CText2Screen.cpp
///
/// \brief Texte a afficher
///
/// \date creation     : 21/09/2024
/// \date modification : 25/11/2024
///

#include "../BertheVarioTac.h"

////////////////////////////////////////////////////////////////////////////////
/// \brief
CText2Screen::CText2Screen()
{
}

////////////////////////////////////////////////////////////////////////////////
/// \brief Parametrage des variables
void CText2Screen::SetPos( uint16_t x , uint16_t y , uint16_t taille , char Unite )
{
m_x = x ;
m_y = y ;
m_Taille = taille ;
m_Unite = Unite ;
}

////////////////////////////////////////////////////////////////////////////////
/// \brief Affichage sans flick.
void CText2Screen::Affiche(const char* pChar , int color )
{
//bool TextChange = m_TextePrincipal != pChar ;
bool TextChange = true ;

// si le tete a changé
if ( m_TextePrincipal != NULL )
    TextChange = strcmp( m_TextePrincipal , pChar ) ;

// si le texte n'a pas changé
if ( !TextChange && !m_ForceAffichage )
    return ;

// position de depart
g_tft.setCursor( m_x , m_y ) ;

// texte
g_tft.setTextSize(m_Taille) ;

// effacement ancien texte si pas constant
g_tft.setCursor( m_x , m_y ) ;
g_tft.setTextColor(TFT_BLACK) ;
//g_tft.print(m_TextePrincipal.c_str());
if ( m_TextePrincipal != NULL )
    g_tft.print(m_TextePrincipal);

// nouveau text
g_tft.setCursor( m_x , m_y ) ;
g_tft.setTextColor(color) ;
g_tft.print(pChar);

if ( m_TextePrincipal != NULL )
    delete [] m_TextePrincipal ;
m_TextePrincipal = new char [ strlen(pChar) + 1 ] ;
strcpy( m_TextePrincipal , pChar ) ;
//m_TextePrincipal = pChar ;

// unite
/*if ( m_Taille == TXT_MOYEN )
    g_tft.setTextSize(3) ;
else
    g_tft.setTextSize(6) ;*/

m_XUnit = g_tft.getCursorX() ;
m_YUnit = g_tft.getCursorY() ;
if ( m_Unite != ' ' )
    g_tft.print(m_Unite);

g_tft.setTextColor(TFT_WHITE) ;
}

////////////////////////////////////////////////////////////////////////////////
/// \brief
void CText2Screen::ChangeUnit( char c )
{
g_tft.setTextColor(TFT_BLACK) ;
g_tft.setTextSize(m_Taille) ;

g_tft.setCursor( m_XUnit , m_YUnit ) ;
g_tft.print(m_Unite);
m_Unite = c ;

g_tft.setTextColor(TFT_WHITE) ;
g_tft.setCursor( m_XUnit , m_YUnit ) ;
g_tft.print(m_Unite);
}
