gitberthe/BertheVarioTac/BertheVarioTacPlatformIO/src/GlobalVar/CMutex.cpp

////////////////////////////////////////////////////////////////////////////////
/// \file CMutex.cpp
///
/// \brief
///
/// \date creation     : 12/03/2024
/// \date modification : 21/09/2024
///

#include "../BertheVarioTac.h"

////////////////////////////////////////////////////////////////////////////////
/// \brief Init du mutex
CMutex::CMutex()
{
m_shared_var_mutex = xSemaphoreCreateMutex() ;
}

////////////////////////////////////////////////////////////////////////////////
/// \brief
void CMutex::PrendreMutex()
{
xSemaphoreTake(m_shared_var_mutex, portMAX_DELAY) ;
}

////////////////////////////////////////////////////////////////////////////////
/// \brief
void CMutex::RelacherMutex()
{
xSemaphoreGive(m_shared_var_mutex);
}
